SmichaelSmolley/Diplom_Arbeit/Dokumentation/Oficell/michael.watzek@el.htl-hl.ac.at_2026-09-18_11-34-14-229.pdf

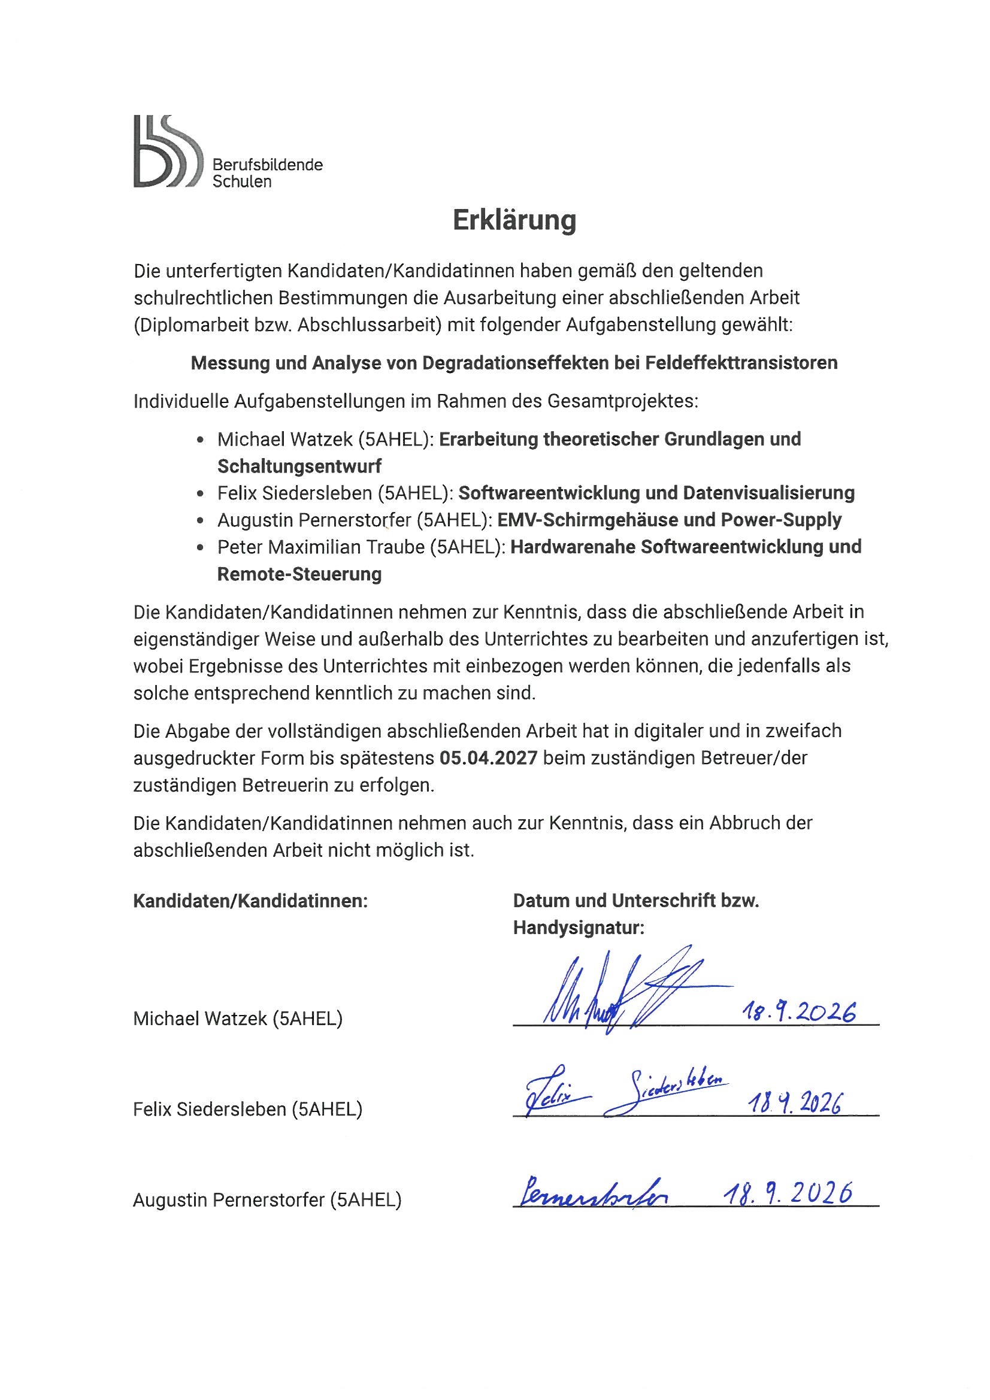
[picture p40: page 1]
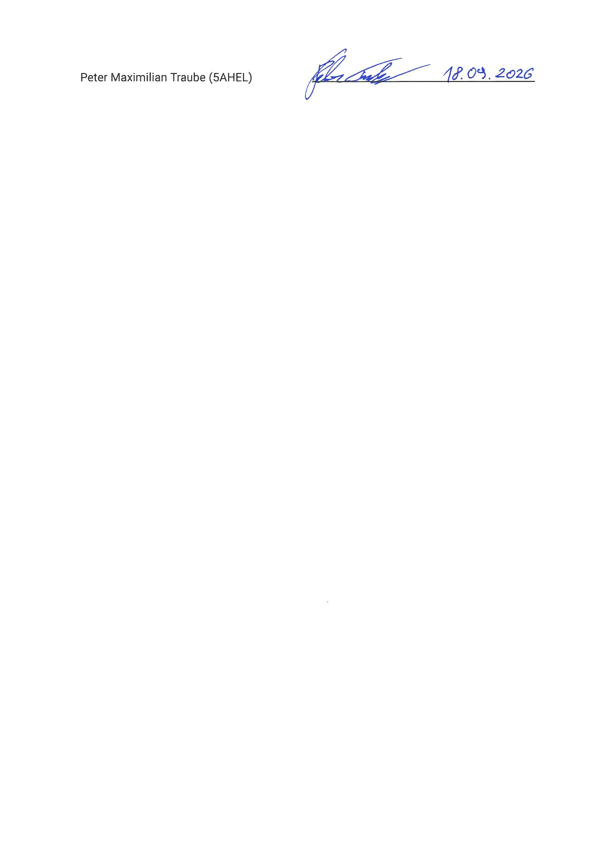
[picture p41: page 2]
