SmichaelSmolley/Diplom_Arbeit/Dokumentation/Datashit/PinkNoise-1durchf.pdf

Quelle:
https://www.analog.com/en/resources/analog-dialogue/articles/understanding-andeliminating-1-fnoise.html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,effectively%2 0reduced%20by%20this%20technique. (https://www.analog.com/en/resources/analog-dialogue/articles/understanding-and-eliminating-1-f-noise.html)

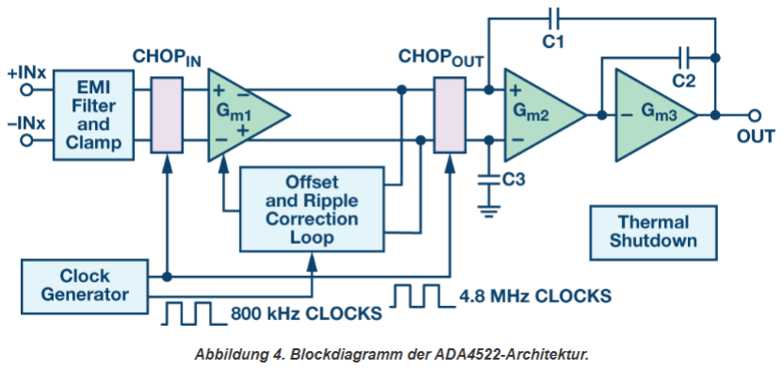
[picture p42: figure]

Möglicher Chopper:
https://www.ti.com/product/de-de/LMP7721
