SmichaelSmolley/Diplom_Arbeit/Dokumentation/Device#01_idvg_05_10.jpg

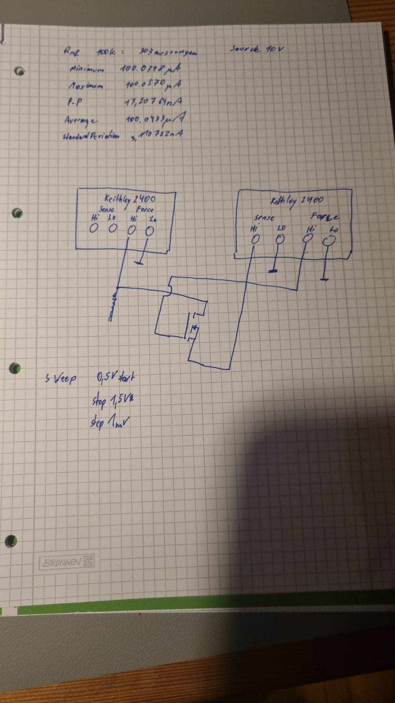
Dokumentation/Device#01_idvg_05_10.jpg
