SmichaelSmolley/Diplom_Arbeit/Dokumentation/dokumentation_bilder/FFTGraph_OV24_Simple.png

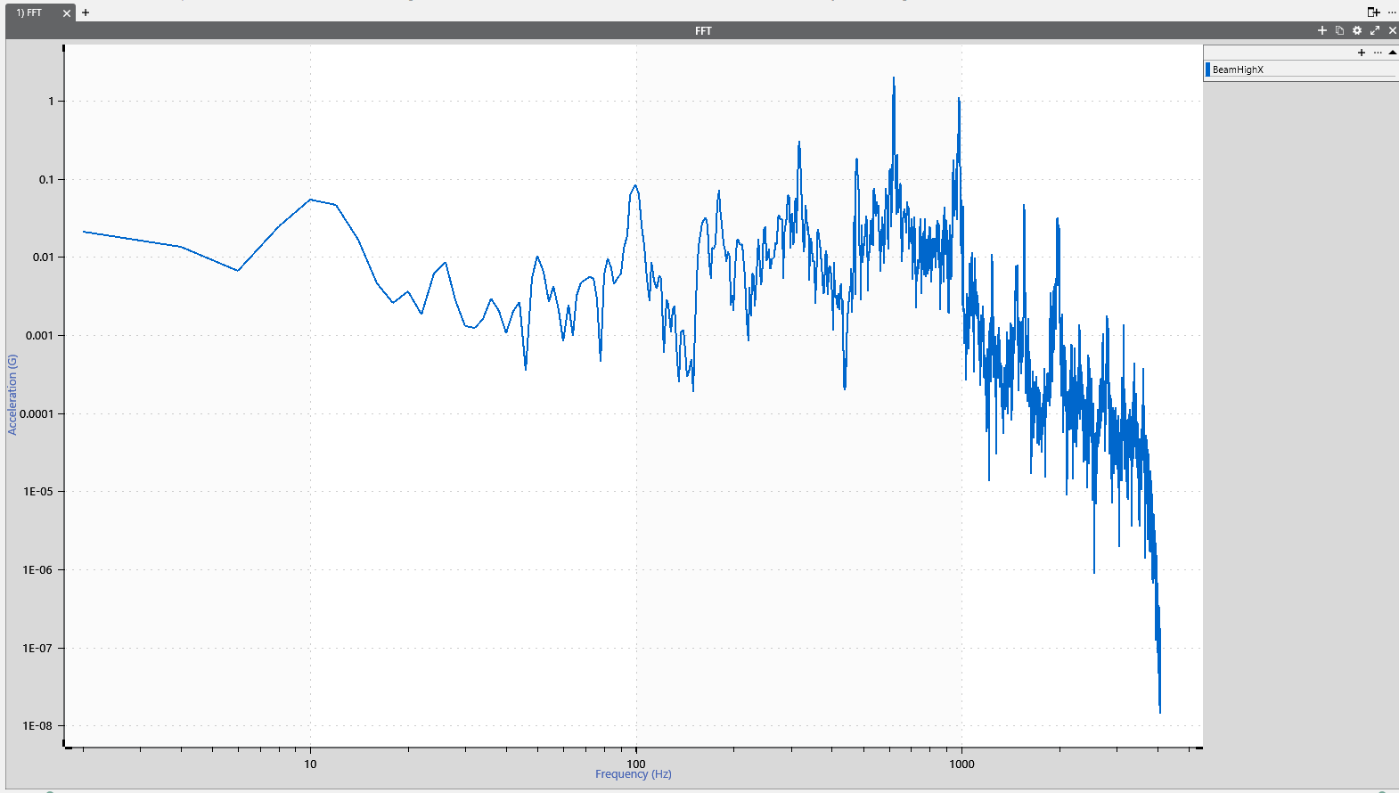
Dokumentation/dokumentation_bilder/FFTGraph_OV24_Simple.png
