SmichaelSmolley/Diplom_Arbeit/Dokumentation/dokumentation_bilder/Screenshot 2026-03-04 135011.png

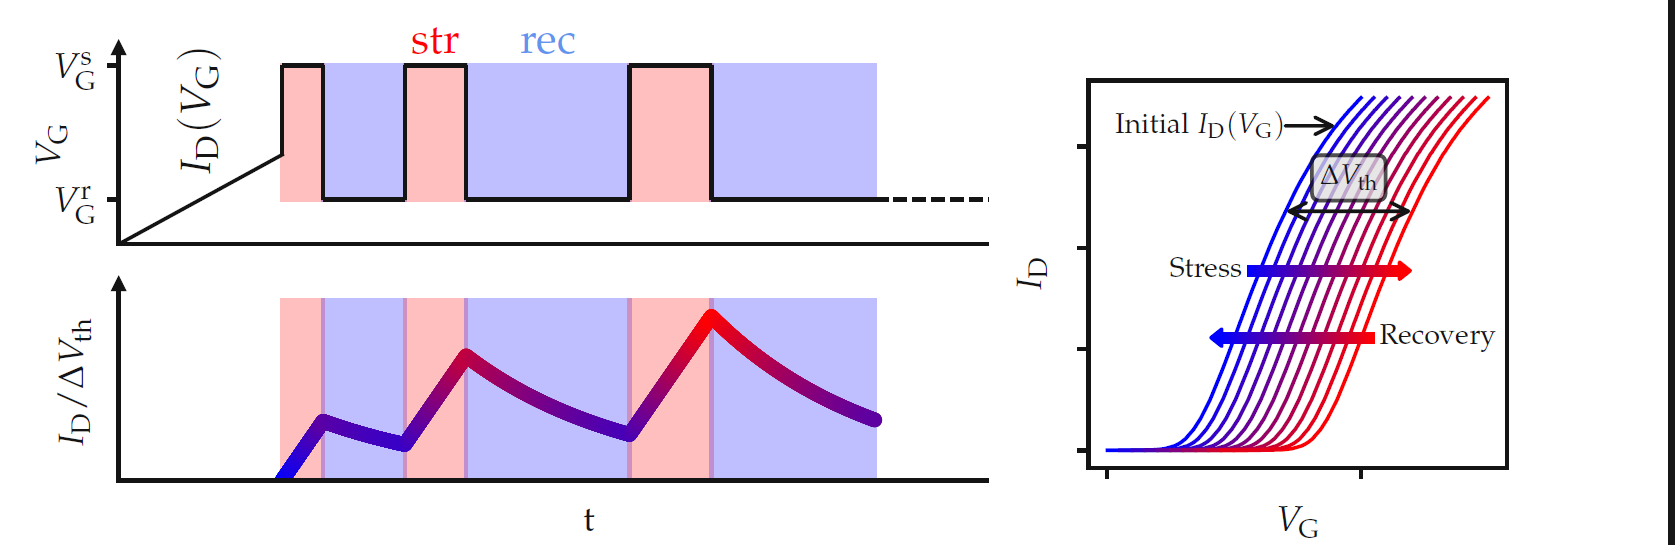
Dokumentation/dokumentation_bilder/Screenshot 2026-03-04 135011.png
