SmichaelSmolley/Diplom_Arbeit/Dokumentation/dokumentation_bilder/signal-2026-05-28-094256_002.jpeg

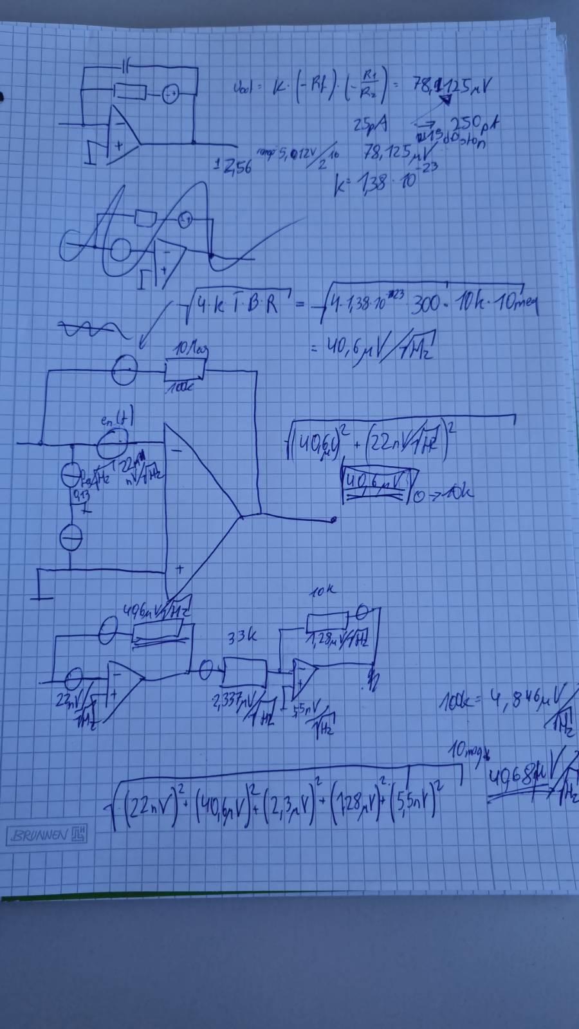
Dokumentation/dokumentation_bilder/signal-2026-05-28-094256_002.jpeg
