SmichaelSmolley/Diplom_Arbeit/Dokumentation/IDVG_BS170_log_17_03_2026.png

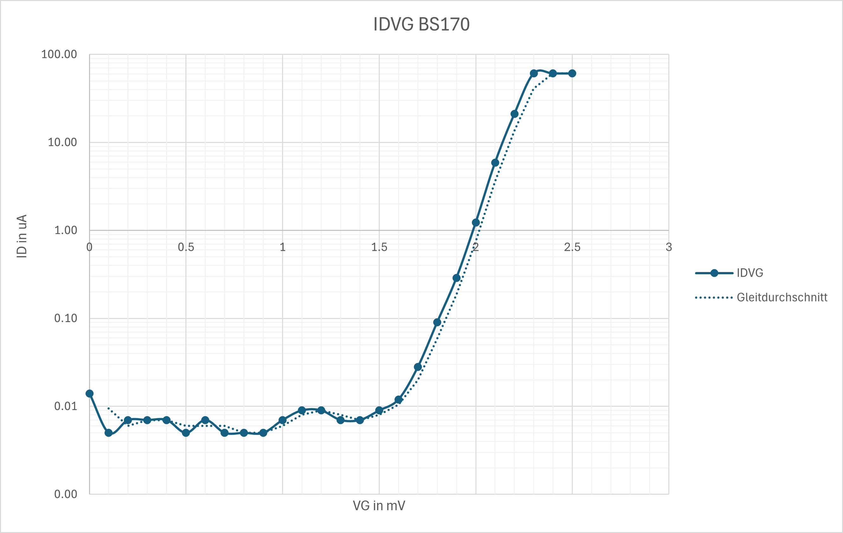
Dokumentation/IDVG_BS170_log_17_03_2026.png
