SmichaelSmolley/Diplom_Arbeit/Software/firmware/Unterlagen_ELLFI/1 Klasse EL/Verbindungsplatine_3D_Top.JPG

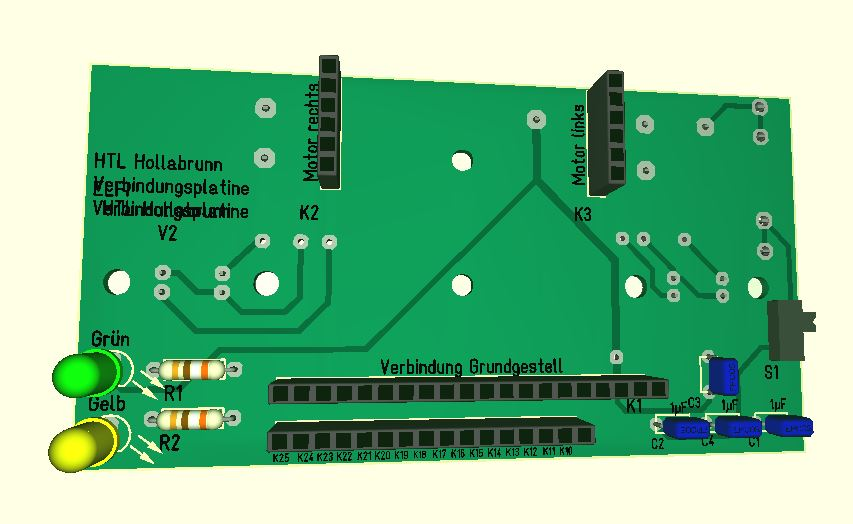
Software/firmware/Unterlagen_ELLFI/1 Klasse EL/Verbindungsplatine_3D_Top.JPG
