SmichaelSmolley/Diplom_Arbeit/Software/firmware/Unterlagen_ELLFI/2 Klasse EL/4erSensorplatine_3D_Top.JPG

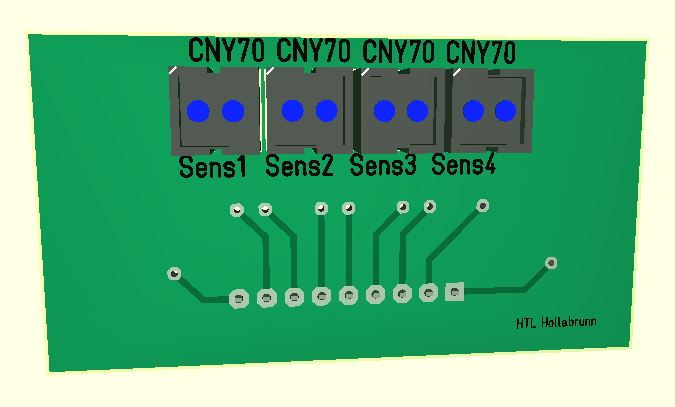
Software/firmware/Unterlagen_ELLFI/2 Klasse EL/4erSensorplatine_3D_Top.JPG
