SmichaelSmolley/Diplom_Arbeit/Software/firmware/Unterlagen_ELLFI/2 Klasse EL/Hauptplatine_3D.JPG

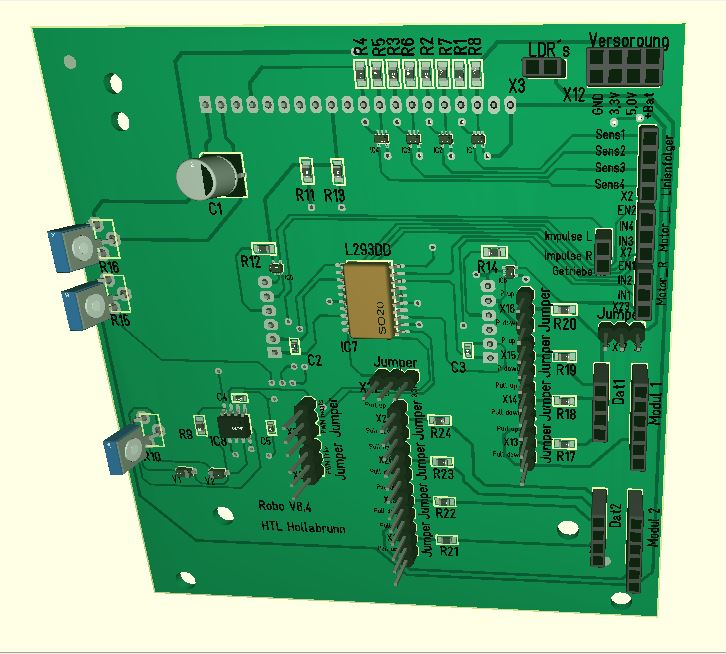
Software/firmware/Unterlagen_ELLFI/2 Klasse EL/Hauptplatine_3D.JPG
