SmichaelSmolley/Diplom_Arbeit/Dokumentation/Rechnungen/99712510.xlsx

# | MENGE | TEILENUMMER | HERSTELLER-TEILENUMMER | BESCHREIBUNG | KUNDENREFERENZ | LIEFERRÜCKSTÄNDE | STÜCKPREIS | GESAMTPREIS
1 | 2 | Z5234-ND | G6SK-2 DC3 | RELAY TELECOM DPDT 2A 3V |  | 0 | 4.04 | 8.08
2 | 2 | Z3287-ND | G6SK-2F DC3 | RELAY TELECOM DPDT 2A 3V |  | 2 | 4.67 | 9.34
3 | 1 | Y0062-100KA-ND | Y0062100K000T9L | RES 100K OHM 0.6W 0.01% RADIAL |  | 0 | 34.06 | 34.06
