SmichaelSmolley/Diplom_Arbeit/Hardware/Altium_libs/ul_OPA197IDBVR/Altium/OPA197IDBVR/DBV5_TEX.step

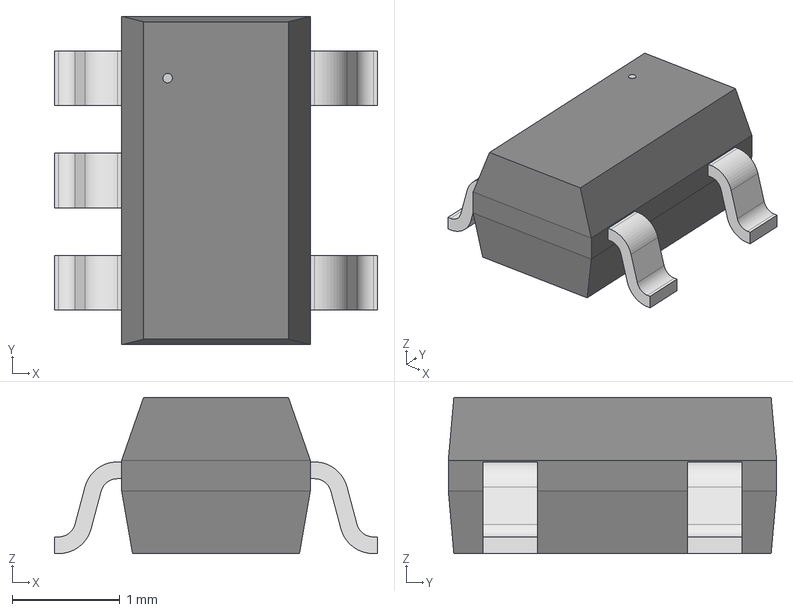
[picture p78: CAD file, 2026-04-23]
Hardware/Altium_libs/ul_OPA197IDBVR/Altium/OPA197IDBVR/DBV5_TEX.step
3.00 x 3.05 x 1.45 mm
