SmichaelSmolley/Diplom_Arbeit/Hardware/Altium_libs/ul_TLV76733DGNR/Altium/TLV76733DGNR/VSSOP8_DGN_TEX.step

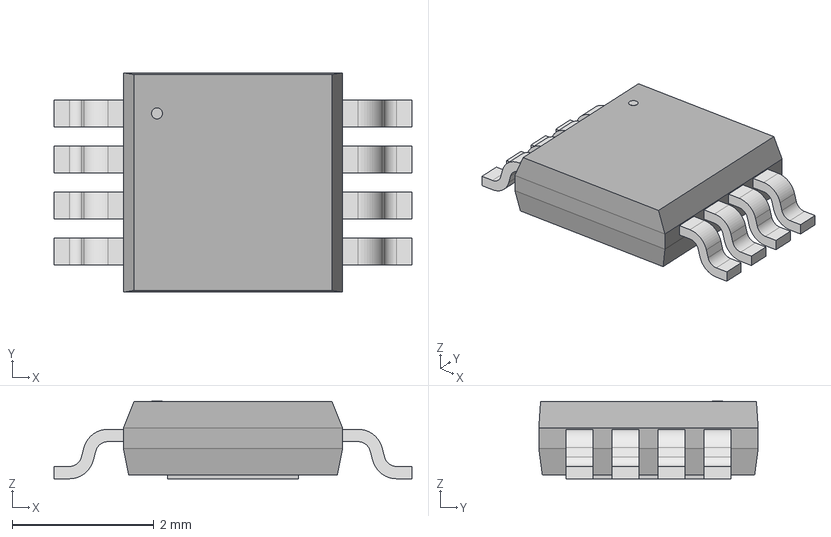
[picture p79: CAD file, 2026-05-05]
Hardware/Altium_libs/ul_TLV76733DGNR/Altium/TLV76733DGNR/VSSOP8_DGN_TEX.step
5.05 x 3.10 x 1.09 mm
