SmichaelSmolley/Diplom_Arbeit/Hardware/Altium_libs/ul_Y0062100K000T9L/Altium/RES_S102K_7P62X2P67_VIS.step

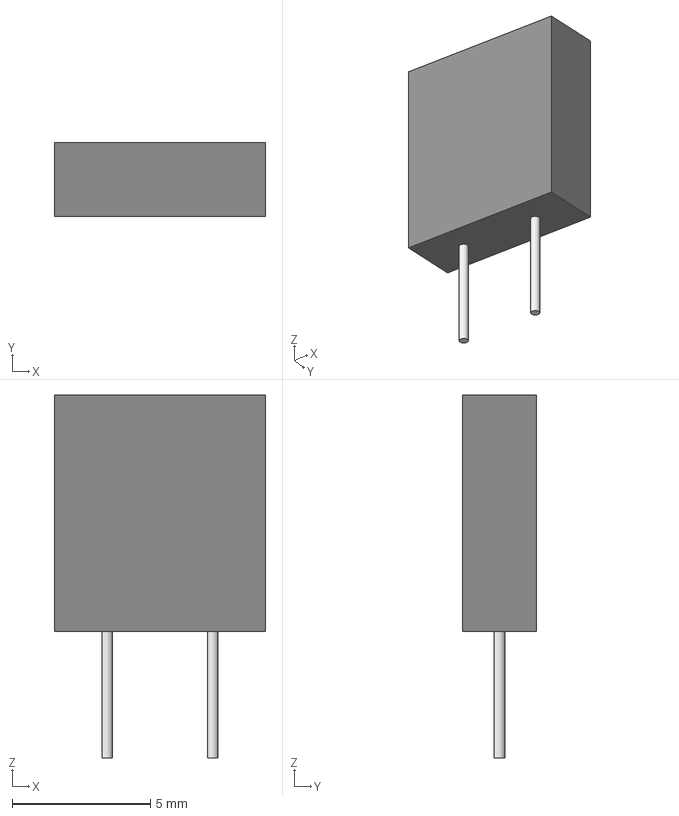
[picture p80: CAD file, 2026-05-07]
Hardware/Altium_libs/ul_Y0062100K000T9L/Altium/RES_S102K_7P62X2P67_VIS.step
7.62 x 2.67 x 13.1 mm
