SmichaelSmolley/Diplom_Arbeit/Software/firmware/PCB_test_code_peda/Objects/PCB_test.htm

# Static Call Graph for image .\Objects\PCB_test.axf

#<CALLGRAPH># ARM Linker, 6190004: Last Updated: Wed Sep 16 19:25:18 2026

### Maximum Stack Usage = 132 bytes + Unknown(Functions without stacksize, Cycles, Untraceable Function Pointers)

### Call chain for Maximum Stack Depth:

__rt_entry_main ⇒ main ⇒ scpi_set_source_voltage ⇒ uart1_put_float ⇒ uart1_put_int ⇒ uart_put_char

### Functions with no stack information

- __user_initial_stackheap

### Mutually Recursive functions

- NMI_Handler ⇒ NMI_Handler
- HardFault_Handler ⇒ HardFault_Handler
- MemManage_Handler ⇒ MemManage_Handler
- BusFault_Handler ⇒ BusFault_Handler
- UsageFault_Handler ⇒ UsageFault_Handler
- SVC_Handler ⇒ SVC_Handler
- DebugMon_Handler ⇒ DebugMon_Handler
- PendSV_Handler ⇒ PendSV_Handler
- SysTick_Handler ⇒ SysTick_Handler
- ADC1_2_IRQHandler ⇒ ADC1_2_IRQHandler

### Function Pointers

- ADC1_2_IRQHandler from startup_stm32f10x_md.o(.text) referenced from startup_stm32f10x_md.o(RESET)
- BusFault_Handler from startup_stm32f10x_md.o(.text) referenced from startup_stm32f10x_md.o(RESET)
- CAN1_RX1_IRQHandler from startup_stm32f10x_md.o(.text) referenced from startup_stm32f10x_md.o(RESET)
- CAN1_SCE_IRQHandler from startup_stm32f10x_md.o(.text) referenced from startup_stm32f10x_md.o(RESET)
- DMA1_Channel1_IRQHandler from startup_stm32f10x_md.o(.text) referenced from startup_stm32f10x_md.o(RESET)
- DMA1_Channel2_IRQHandler from startup_stm32f10x_md.o(.text) referenced from startup_stm32f10x_md.o(RESET)
- DMA1_Channel3_IRQHandler from startup_stm32f10x_md.o(.text) referenced from startup_stm32f10x_md.o(RESET)
- DMA1_Channel4_IRQHandler from startup_stm32f10x_md.o(.text) referenced from startup_stm32f10x_md.o(RESET)
- DMA1_Channel5_IRQHandler from startup_stm32f10x_md.o(.text) referenced from startup_stm32f10x_md.o(RESET)
- DMA1_Channel6_IRQHandler from startup_stm32f10x_md.o(.text) referenced from startup_stm32f10x_md.o(RESET)
- DMA1_Channel7_IRQHandler from startup_stm32f10x_md.o(.text) referenced from startup_stm32f10x_md.o(RESET)
- DebugMon_Handler from startup_stm32f10x_md.o(.text) referenced from startup_stm32f10x_md.o(RESET)
- EXTI0_IRQHandler from startup_stm32f10x_md.o(.text) referenced from startup_stm32f10x_md.o(RESET)
- EXTI15_10_IRQHandler from startup_stm32f10x_md.o(.text) referenced from startup_stm32f10x_md.o(RESET)
- EXTI1_IRQHandler from startup_stm32f10x_md.o(.text) referenced from startup_stm32f10x_md.o(RESET)
- EXTI2_IRQHandler from startup_stm32f10x_md.o(.text) referenced from startup_stm32f10x_md.o(RESET)
- EXTI3_IRQHandler from startup_stm32f10x_md.o(.text) referenced from startup_stm32f10x_md.o(RESET)
- EXTI4_IRQHandler from startup_stm32f10x_md.o(.text) referenced from startup_stm32f10x_md.o(RESET)
- EXTI9_5_IRQHandler from startup_stm32f10x_md.o(.text) referenced from startup_stm32f10x_md.o(RESET)
- FLASH_IRQHandler from startup_stm32f10x_md.o(.text) referenced from startup_stm32f10x_md.o(RESET)
- HardFault_Handler from startup_stm32f10x_md.o(.text) referenced from startup_stm32f10x_md.o(RESET)
- I2C1_ER_IRQHandler from startup_stm32f10x_md.o(.text) referenced from startup_stm32f10x_md.o(RESET)
- I2C1_EV_IRQHandler from startup_stm32f10x_md.o(.text) referenced from startup_stm32f10x_md.o(RESET)
- I2C2_ER_IRQHandler from startup_stm32f10x_md.o(.text) referenced from startup_stm32f10x_md.o(RESET)
- I2C2_EV_IRQHandler from startup_stm32f10x_md.o(.text) referenced from startup_stm32f10x_md.o(RESET)
- MemManage_Handler from startup_stm32f10x_md.o(.text) referenced from startup_stm32f10x_md.o(RESET)
- NMI_Handler from startup_stm32f10x_md.o(.text) referenced from startup_stm32f10x_md.o(RESET)
- PVD_IRQHandler from startup_stm32f10x_md.o(.text) referenced from startup_stm32f10x_md.o(RESET)
- PendSV_Handler from startup_stm32f10x_md.o(.text) referenced from startup_stm32f10x_md.o(RESET)
- RCC_IRQHandler from startup_stm32f10x_md.o(.text) referenced from startup_stm32f10x_md.o(RESET)
- RTCAlarm_IRQHandler from startup_stm32f10x_md.o(.text) referenced from startup_stm32f10x_md.o(RESET)
- RTC_IRQHandler from startup_stm32f10x_md.o(.text) referenced from startup_stm32f10x_md.o(RESET)
- Reset_Handler from startup_stm32f10x_md.o(.text) referenced from startup_stm32f10x_md.o(RESET)
- SPI1_IRQHandler from startup_stm32f10x_md.o(.text) referenced from startup_stm32f10x_md.o(RESET)
- SPI2_IRQHandler from startup_stm32f10x_md.o(.text) referenced from startup_stm32f10x_md.o(RESET)
- SVC_Handler from startup_stm32f10x_md.o(.text) referenced from startup_stm32f10x_md.o(RESET)
- SysTick_Handler from startup_stm32f10x_md.o(.text) referenced from startup_stm32f10x_md.o(RESET)
- SystemInit from system_stm32f10x.o(.text.SystemInit) referenced from startup_stm32f10x_md.o(.text)
- TAMPER_IRQHandler from startup_stm32f10x_md.o(.text) referenced from startup_stm32f10x_md.o(RESET)
- TIM1_BRK_IRQHandler from startup_stm32f10x_md.o(.text) referenced from startup_stm32f10x_md.o(RESET)
- TIM1_CC_IRQHandler from startup_stm32f10x_md.o(.text) referenced from startup_stm32f10x_md.o(RESET)
- TIM1_TRG_COM_IRQHandler from startup_stm32f10x_md.o(.text) referenced from startup_stm32f10x_md.o(RESET)
- TIM1_UP_IRQHandler from startup_stm32f10x_md.o(.text) referenced from startup_stm32f10x_md.o(RESET)
- TIM2_IRQHandler from startup_stm32f10x_md.o(.text) referenced from startup_stm32f10x_md.o(RESET)
- TIM3_IRQHandler from startup_stm32f10x_md.o(.text) referenced from startup_stm32f10x_md.o(RESET)
- TIM4_IRQHandler from startup_stm32f10x_md.o(.text) referenced from startup_stm32f10x_md.o(RESET)
- USART1_IRQHandler from startup_stm32f10x_md.o(.text) referenced from startup_stm32f10x_md.o(RESET)
- USART2_IRQHandler from startup_stm32f10x_md.o(.text) referenced from startup_stm32f10x_md.o(RESET)
- USART3_IRQHandler from startup_stm32f10x_md.o(.text) referenced from startup_stm32f10x_md.o(RESET)
- USBWakeUp_IRQHandler from startup_stm32f10x_md.o(.text) referenced from startup_stm32f10x_md.o(RESET)
- USB_HP_CAN1_TX_IRQHandler from startup_stm32f10x_md.o(.text) referenced from startup_stm32f10x_md.o(RESET)
- USB_LP_CAN1_RX0_IRQHandler from startup_stm32f10x_md.o(.text) referenced from startup_stm32f10x_md.o(RESET)
- UsageFault_Handler from startup_stm32f10x_md.o(.text) referenced from startup_stm32f10x_md.o(RESET)
- WWDG_IRQHandler from startup_stm32f10x_md.o(.text) referenced from startup_stm32f10x_md.o(RESET)
- __main from __main.o(!!!main) referenced from startup_stm32f10x_md.o(.text)

### Global Symbols

__main (Thumb, 8 bytes, Stack size 0 bytes, __main.o(!!!main))

[Calls]

- >> __scatterload
- >> __rt_entry

[Address Reference Count : 1]

- startup_stm32f10x_md.o(.text)

__scatterload (Thumb, 0 bytes, Stack size unknown bytes, __scatter.o(!!!scatter))

[Called By]

- >> __main

__scatterload_rt2 (Thumb, 44 bytes, Stack size unknown bytes, __scatter.o(!!!scatter), UNUSED)

[Calls]

- >> __rt_entry

__scatterload_rt2_thumb_only (Thumb, 0 bytes, Stack size unknown bytes, __scatter.o(!!!scatter), UNUSED)

__scatterload_null (Thumb, 0 bytes, Stack size unknown bytes, __scatter.o(!!!scatter), UNUSED)

__scatterload_zeroinit (Thumb, 28 bytes, Stack size unknown bytes, __scatter_zi.o(!!handler_zi), UNUSED)

__rt_lib_init (Thumb, 0 bytes, Stack size unknown bytes, libinit.o(.ARM.Collect$$libinit$$00000000))

[Called By]

- >> __rt_entry_li

__rt_lib_init_alloca_1 (Thumb, 0 bytes, Stack size unknown bytes, libinit2.o(.ARM.Collect$$libinit$$00000030))

__rt_lib_init_argv_1 (Thumb, 0 bytes, Stack size unknown bytes, libinit2.o(.ARM.Collect$$libinit$$0000002E))

__rt_lib_init_atexit_1 (Thumb, 0 bytes, Stack size unknown bytes, libinit2.o(.ARM.Collect$$libinit$$0000001D))

__rt_lib_init_clock_1 (Thumb, 0 bytes, Stack size unknown bytes, libinit2.o(.ARM.Collect$$libinit$$00000023))

__rt_lib_init_cpp_1 (Thumb, 0 bytes, Stack size unknown bytes, libinit2.o(.ARM.Collect$$libinit$$00000034))

__rt_lib_init_exceptions_1 (Thumb, 0 bytes, Stack size unknown bytes, libinit2.o(.ARM.Collect$$libinit$$00000032))

__rt_lib_init_fp_1 (Thumb, 0 bytes, Stack size unknown bytes, libinit2.o(.ARM.Collect$$libinit$$00000002))

__rt_lib_init_fp_trap_1 (Thumb, 0 bytes, Stack size unknown bytes, libinit2.o(.ARM.Collect$$libinit$$00000021))

__rt_lib_init_getenv_1 (Thumb, 0 bytes, Stack size unknown bytes, libinit2.o(.ARM.Collect$$libinit$$00000025))

__rt_lib_init_heap_1 (Thumb, 0 bytes, Stack size unknown bytes, libinit2.o(.ARM.Collect$$libinit$$0000000C))

__rt_lib_init_lc_collate_1 (Thumb, 0 bytes, Stack size unknown bytes, libinit2.o(.ARM.Collect$$libinit$$00000013))

__rt_lib_init_lc_ctype_1 (Thumb, 0 bytes, Stack size unknown bytes, libinit2.o(.ARM.Collect$$libinit$$00000015))

__rt_lib_init_lc_monetary_1 (Thumb, 0 bytes, Stack size unknown bytes, libinit2.o(.ARM.Collect$$libinit$$00000017))

__rt_lib_init_lc_numeric_1 (Thumb, 0 bytes, Stack size unknown bytes, libinit2.o(.ARM.Collect$$libinit$$00000019))

__rt_lib_init_lc_time_1 (Thumb, 0 bytes, Stack size unknown bytes, libinit2.o(.ARM.Collect$$libinit$$0000001B))

__rt_lib_init_preinit_1 (Thumb, 0 bytes, Stack size unknown bytes, libinit2.o(.ARM.Collect$$libinit$$00000006))

__rt_lib_init_rand_1 (Thumb, 0 bytes, Stack size unknown bytes, libinit2.o(.ARM.Collect$$libinit$$00000010))

__rt_lib_init_relocate_pie_1 (Thumb, 0 bytes, Stack size unknown bytes, libinit2.o(.ARM.Collect$$libinit$$00000004))

__rt_lib_init_return (Thumb, 0 bytes, Stack size unknown bytes, libinit2.o(.ARM.Collect$$libinit$$00000035))

__rt_lib_init_signal_1 (Thumb, 0 bytes, Stack size unknown bytes, libinit2.o(.ARM.Collect$$libinit$$0000001F))

__rt_lib_init_stdio_1 (Thumb, 0 bytes, Stack size unknown bytes, libinit2.o(.ARM.Collect$$libinit$$00000027))

__rt_lib_init_user_alloc_1 (Thumb, 0 bytes, Stack size unknown bytes, libinit2.o(.ARM.Collect$$libinit$$0000000E))

__rt_lib_shutdown (Thumb, 0 bytes, Stack size unknown bytes, libshutdown.o(.ARM.Collect$$libshutdown$$00000000))

[Called By]

- >> __rt_exit_ls

__rt_lib_shutdown_cpp_1 (Thumb, 0 bytes, Stack size unknown bytes, libshutdown2.o(.ARM.Collect$$libshutdown$$00000002))

__rt_lib_shutdown_fp_trap_1 (Thumb, 0 bytes, Stack size unknown bytes, libshutdown2.o(.ARM.Collect$$libshutdown$$00000007))

__rt_lib_shutdown_heap_1 (Thumb, 0 bytes, Stack size unknown bytes, libshutdown2.o(.ARM.Collect$$libshutdown$$0000000F))

__rt_lib_shutdown_return (Thumb, 0 bytes, Stack size unknown bytes, libshutdown2.o(.ARM.Collect$$libshutdown$$00000010))

__rt_lib_shutdown_signal_1 (Thumb, 0 bytes, Stack size unknown bytes, libshutdown2.o(.ARM.Collect$$libshutdown$$0000000A))

__rt_lib_shutdown_stdio_1 (Thumb, 0 bytes, Stack size unknown bytes, libshutdown2.o(.ARM.Collect$$libshutdown$$00000004))

__rt_lib_shutdown_user_alloc_1 (Thumb, 0 bytes, Stack size unknown bytes, libshutdown2.o(.ARM.Collect$$libshutdown$$0000000C))

__rt_entry (Thumb, 0 bytes, Stack size unknown bytes, __rtentry.o(.ARM.Collect$$rtentry$$00000000))

[Called By]

- >> __scatterload_rt2
- >> __main

__rt_entry_presh_1 (Thumb, 0 bytes, Stack size unknown bytes, __rtentry2.o(.ARM.Collect$$rtentry$$00000002))

__rt_entry_sh (Thumb, 0 bytes, Stack size unknown bytes, __rtentry4.o(.ARM.Collect$$rtentry$$00000004))

[Stack]

- Max Depth = 8 + Unknown Stack Size
- Call Chain = __rt_entry_sh ⇒ __user_setup_stackheap

[Calls]

- >> __user_setup_stackheap

__rt_entry_li (Thumb, 0 bytes, Stack size unknown bytes, __rtentry2.o(.ARM.Collect$$rtentry$$0000000A))

[Calls]

- >> __rt_lib_init

__rt_entry_postsh_1 (Thumb, 0 bytes, Stack size unknown bytes, __rtentry2.o(.ARM.Collect$$rtentry$$00000009))

__rt_entry_main (Thumb, 0 bytes, Stack size unknown bytes, __rtentry2.o(.ARM.Collect$$rtentry$$0000000D))

[Stack]

- Max Depth = 132 + Unknown Stack Size
- Call Chain = __rt_entry_main ⇒ main ⇒ scpi_set_source_voltage ⇒ uart1_put_float ⇒ uart1_put_int ⇒ uart_put_char

[Calls]

- >> exit
- >> main

__rt_entry_postli_1 (Thumb, 0 bytes, Stack size unknown bytes, __rtentry2.o(.ARM.Collect$$rtentry$$0000000C))

__rt_exit (Thumb, 0 bytes, Stack size unknown bytes, rtexit.o(.ARM.Collect$$rtexit$$00000000))

[Called By]

- >> exit

__rt_exit_ls (Thumb, 0 bytes, Stack size unknown bytes, rtexit2.o(.ARM.Collect$$rtexit$$00000003))

[Calls]

- >> __rt_lib_shutdown

__rt_exit_prels_1 (Thumb, 0 bytes, Stack size unknown bytes, rtexit2.o(.ARM.Collect$$rtexit$$00000002))

__rt_exit_exit (Thumb, 0 bytes, Stack size unknown bytes, rtexit2.o(.ARM.Collect$$rtexit$$00000004))

[Calls]

- >> _sys_exit

Reset_Handler (Thumb, 8 bytes, Stack size 0 bytes, startup_stm32f10x_md.o(.text))
[Address Reference Count : 1]

- startup_stm32f10x_md.o(RESET)

NMI_Handler (Thumb, 2 bytes, Stack size 0 bytes, startup_stm32f10x_md.o(.text))

[Calls]

- >> NMI_Handler

[Called By]

- >> NMI_Handler

[Address Reference Count : 1]

- startup_stm32f10x_md.o(RESET)

HardFault_Handler (Thumb, 2 bytes, Stack size 0 bytes, startup_stm32f10x_md.o(.text))

[Calls]

- >> HardFault_Handler

[Called By]

- >> HardFault_Handler

[Address Reference Count : 1]

- startup_stm32f10x_md.o(RESET)

MemManage_Handler (Thumb, 2 bytes, Stack size 0 bytes, startup_stm32f10x_md.o(.text))

[Calls]

- >> MemManage_Handler

[Called By]

- >> MemManage_Handler

[Address Reference Count : 1]

- startup_stm32f10x_md.o(RESET)

BusFault_Handler (Thumb, 2 bytes, Stack size 0 bytes, startup_stm32f10x_md.o(.text))

[Calls]

- >> BusFault_Handler

[Called By]

- >> BusFault_Handler

[Address Reference Count : 1]

- startup_stm32f10x_md.o(RESET)

UsageFault_Handler (Thumb, 2 bytes, Stack size 0 bytes, startup_stm32f10x_md.o(.text))

[Calls]

- >> UsageFault_Handler

[Called By]

- >> UsageFault_Handler

[Address Reference Count : 1]

- startup_stm32f10x_md.o(RESET)

SVC_Handler (Thumb, 2 bytes, Stack size 0 bytes, startup_stm32f10x_md.o(.text))

[Calls]

- >> SVC_Handler

[Called By]

- >> SVC_Handler

[Address Reference Count : 1]

- startup_stm32f10x_md.o(RESET)

DebugMon_Handler (Thumb, 2 bytes, Stack size 0 bytes, startup_stm32f10x_md.o(.text))

[Calls]

- >> DebugMon_Handler

[Called By]

- >> DebugMon_Handler

[Address Reference Count : 1]

- startup_stm32f10x_md.o(RESET)

PendSV_Handler (Thumb, 2 bytes, Stack size 0 bytes, startup_stm32f10x_md.o(.text))

[Calls]

- >> PendSV_Handler

[Called By]

- >> PendSV_Handler

[Address Reference Count : 1]

- startup_stm32f10x_md.o(RESET)

SysTick_Handler (Thumb, 2 bytes, Stack size 0 bytes, startup_stm32f10x_md.o(.text))

[Calls]

- >> SysTick_Handler

[Called By]

- >> SysTick_Handler

[Address Reference Count : 1]

- startup_stm32f10x_md.o(RESET)

ADC1_2_IRQHandler (Thumb, 0 bytes, Stack size 0 bytes, startup_stm32f10x_md.o(.text))

[Calls]

- >> ADC1_2_IRQHandler

[Called By]

- >> ADC1_2_IRQHandler

[Address Reference Count : 1]

- startup_stm32f10x_md.o(RESET)

CAN1_RX1_IRQHandler (Thumb, 0 bytes, Stack size 0 bytes, startup_stm32f10x_md.o(.text))
[Address Reference Count : 1]

- startup_stm32f10x_md.o(RESET)

CAN1_SCE_IRQHandler (Thumb, 0 bytes, Stack size 0 bytes, startup_stm32f10x_md.o(.text))
[Address Reference Count : 1]

- startup_stm32f10x_md.o(RESET)

DMA1_Channel1_IRQHandler (Thumb, 0 bytes, Stack size 0 bytes, startup_stm32f10x_md.o(.text))
[Address Reference Count : 1]

- startup_stm32f10x_md.o(RESET)

DMA1_Channel2_IRQHandler (Thumb, 0 bytes, Stack size 0 bytes, startup_stm32f10x_md.o(.text))
[Address Reference Count : 1]

- startup_stm32f10x_md.o(RESET)

DMA1_Channel3_IRQHandler (Thumb, 0 bytes, Stack size 0 bytes, startup_stm32f10x_md.o(.text))
[Address Reference Count : 1]

- startup_stm32f10x_md.o(RESET)

DMA1_Channel4_IRQHandler (Thumb, 0 bytes, Stack size 0 bytes, startup_stm32f10x_md.o(.text))
[Address Reference Count : 1]

- startup_stm32f10x_md.o(RESET)

DMA1_Channel5_IRQHandler (Thumb, 0 bytes, Stack size 0 bytes, startup_stm32f10x_md.o(.text))
[Address Reference Count : 1]

- startup_stm32f10x_md.o(RESET)

DMA1_Channel6_IRQHandler (Thumb, 0 bytes, Stack size 0 bytes, startup_stm32f10x_md.o(.text))
[Address Reference Count : 1]

- startup_stm32f10x_md.o(RESET)

DMA1_Channel7_IRQHandler (Thumb, 0 bytes, Stack size 0 bytes, startup_stm32f10x_md.o(.text))
[Address Reference Count : 1]

- startup_stm32f10x_md.o(RESET)

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
[Address Reference Count : 1]

- startup_stm32f10x_md.o(RESET)

USBWakeUp_IRQHandler (Thumb, 0 bytes, Stack size 0 bytes, startup_stm32f10x_md.o(.text))
[Address Reference Count : 1]

- startup_stm32f10x_md.o(RESET)

USB_HP_CAN1_TX_IRQHandler (Thumb, 0 bytes, Stack size 0 bytes, startup_stm32f10x_md.o(.text))
[Address Reference Count : 1]

- startup_stm32f10x_md.o(RESET)

USB_LP_CAN1_RX0_IRQHandler (Thumb, 0 bytes, Stack size 0 bytes, startup_stm32f10x_md.o(.text))
[Address Reference Count : 1]

- startup_stm32f10x_md.o(RESET)

WWDG_IRQHandler (Thumb, 0 bytes, Stack size 0 bytes, startup_stm32f10x_md.o(.text))
[Address Reference Count : 1]

- startup_stm32f10x_md.o(RESET)

__user_initial_stackheap (Thumb, 0 bytes, Stack size unknown bytes, startup_stm32f10x_md.o(.text))

[Called By]

- >> __user_setup_stackheap

__use_two_region_memory (Thumb, 2 bytes, Stack size 0 bytes, heapauxi.o(.text), UNUSED)

__rt_heap_escrow$2region (Thumb, 2 bytes, Stack size 0 bytes, heapauxi.o(.text), UNUSED)

__rt_heap_expand$2region (Thumb, 2 bytes, Stack size 0 bytes, heapauxi.o(.text), UNUSED)

__user_setup_stackheap (Thumb, 74 bytes, Stack size 8 bytes, sys_stackheap_outer.o(.text))

[Stack]

- Max Depth = 8 + Unknown Stack Size
- Call Chain = __user_setup_stackheap

[Calls]

- >> __user_perproc_libspace
- >> __user_initial_stackheap

[Called By]

- >> __rt_entry_sh

exit (Thumb, 18 bytes, Stack size 8 bytes, exit.o(.text))

[Stack]

- Max Depth = 8 + Unknown Stack Size
- Call Chain = exit

[Calls]

- >> __rt_exit

[Called By]

- >> __rt_entry_main

__user_libspace (Thumb, 8 bytes, Stack size 0 bytes, libspace.o(.text), UNUSED)

__user_perproc_libspace (Thumb, 0 bytes, Stack size 0 bytes, libspace.o(.text))

[Called By]

- >> __user_setup_stackheap

__user_perthread_libspace (Thumb, 0 bytes, Stack size 0 bytes, libspace.o(.text), UNUSED)

_sys_exit (Thumb, 8 bytes, Stack size 0 bytes, sys_exit.o(.text))

[Called By]

- >> __rt_exit_exit

__I$use$semihosting (Thumb, 0 bytes, Stack size 0 bytes, use_no_semi.o(.text), UNUSED)

__use_no_semihosting_swi (Thumb, 2 bytes, Stack size 0 bytes, use_no_semi.o(.text), UNUSED)

__semihosting_library_function (Thumb, 0 bytes, Stack size unknown bytes, indicate_semi.o(.text), UNUSED)

PIN_init (Thumb, 276 bytes, Stack size 4 bytes, pins.o(.text.PIN_init))

[Stack]

- Max Depth = 4
- Call Chain = PIN_init

[Called By]

- >> main

SystemInit (Thumb, 102 bytes, Stack size 8 bytes, system_stm32f10x.o(.text.SystemInit))

[Stack]

- Max Depth = 32
- Call Chain = SystemInit ⇒ SetSysClock ⇒ SetSysClockTo48

[Calls]

- >> SetSysClock

[Address Reference Count : 1]

- startup_stm32f10x_md.o(.text)

main (Thumb, 244 bytes, Stack size 40 bytes, main.o(.text.main))

[Stack]

- Max Depth = 132
- Call Chain = main ⇒ scpi_set_source_voltage ⇒ uart1_put_float ⇒ uart1_put_int ⇒ uart_put_char

[Calls]

- >> __aeabi_fcmpgt
- >> __aeabi_fadd
- >> __aeabi_f2d
- >> wait_ms
- >> PIN_init
- >> scpi_stop_measurement
- >> scpi_start_measurement
- >> scpi_set_sense_autorange
- >> scpi_set_sense_range
- >> scpi_set_source_output
- >> scpi_set_source_voltage
- >> scpi_set_source_prot
- >> scpi_set_source_range
- >> scpi_reset
- >> uart_put_string
- >> set_up_uart1

[Called By]

- >> __rt_entry_main

scpi_reset (Thumb, 28 bytes, Stack size 8 bytes, scpi_commands.o(.text.scpi_reset))

[Stack]

- Max Depth = 28
- Call Chain = scpi_reset ⇒ uart_put_string ⇒ uart_put_char

[Calls]

- >> uart_put_string

[Called By]

- >> main

scpi_set_sense_autorange (Thumb, 74 bytes, Stack size 16 bytes, scpi_commands.o(.text.scpi_set_sense_autorange))

[Stack]

- Max Depth = 36
- Call Chain = scpi_set_sense_autorange ⇒ uart_put_string ⇒ uart_put_char

[Calls]

- >> uart_put_string

[Called By]

- >> main

scpi_set_sense_range (Thumb, 40 bytes, Stack size 16 bytes, scpi_commands.o(.text.scpi_set_sense_range))

[Stack]

- Max Depth = 36
- Call Chain = scpi_set_sense_range ⇒ uart_put_string ⇒ uart_put_char

[Calls]

- >> uart_put_string

[Called By]

- >> main

scpi_set_source_output (Thumb, 98 bytes, Stack size 16 bytes, scpi_commands.o(.text.scpi_set_source_output))

[Stack]

- Max Depth = 52
- Call Chain = scpi_set_source_output ⇒ uart1_put_int ⇒ uart_put_char

[Calls]

- >> uart1_put_int
- >> uart_put_string

[Called By]

- >> main

scpi_set_source_prot (Thumb, 66 bytes, Stack size 16 bytes, scpi_commands.o(.text.scpi_set_source_prot))

[Stack]

- Max Depth = 92
- Call Chain = scpi_set_source_prot ⇒ uart1_put_float ⇒ uart1_put_int ⇒ uart_put_char

[Calls]

- >> uart1_put_float
- >> uart1_put_int
- >> uart_put_string

[Called By]

- >> main

scpi_set_source_range (Thumb, 64 bytes, Stack size 16 bytes, scpi_commands.o(.text.scpi_set_source_range))

[Stack]

- Max Depth = 52
- Call Chain = scpi_set_source_range ⇒ uart1_put_int ⇒ uart_put_char

[Calls]

- >> uart1_put_int
- >> uart_put_string

[Called By]

- >> main

scpi_set_source_voltage (Thumb, 66 bytes, Stack size 16 bytes, scpi_commands.o(.text.scpi_set_source_voltage))

[Stack]

- Max Depth = 92
- Call Chain = scpi_set_source_voltage ⇒ uart1_put_float ⇒ uart1_put_int ⇒ uart_put_char

[Calls]

- >> uart1_put_float
- >> uart1_put_int
- >> uart_put_string

[Called By]

- >> main

scpi_start_measurement (Thumb, 28 bytes, Stack size 8 bytes, scpi_commands.o(.text.scpi_start_measurement))

[Stack]

- Max Depth = 28
- Call Chain = scpi_start_measurement ⇒ uart_put_string ⇒ uart_put_char

[Calls]

- >> uart_put_string

[Called By]

- >> main

scpi_stop_measurement (Thumb, 28 bytes, Stack size 8 bytes, scpi_commands.o(.text.scpi_stop_measurement))

[Stack]

- Max Depth = 28
- Call Chain = scpi_stop_measurement ⇒ uart_put_string ⇒ uart_put_char

[Calls]

- >> uart_put_string

[Called By]

- >> main

set_up_uart1 (Thumb, 136 bytes, Stack size 0 bytes, uart.o(.text.set_up_uart1))

[Called By]

- >> main

uart1_put_float (Thumb, 148 bytes, Stack size 40 bytes, scpi_commands.o(.text.uart1_put_float))

[Stack]

- Max Depth = 76
- Call Chain = uart1_put_float ⇒ uart1_put_int ⇒ uart_put_char

[Calls]

- >> __aeabi_fmul
- >> __aeabi_i2f
- >> __aeabi_f2iz
- >> __aeabi_fcmpge
- >> __aeabi_fsub
- >> uart1_put_int
- >> uart_put_char

[Called By]

- >> scpi_set_source_voltage
- >> scpi_set_source_prot

uart1_put_int (Thumb, 144 bytes, Stack size 32 bytes, scpi_commands.o(.text.uart1_put_int))

[Stack]

- Max Depth = 36
- Call Chain = uart1_put_int ⇒ uart_put_char

[Calls]

- >> uart_put_char

[Called By]

- >> scpi_set_source_output
- >> scpi_set_source_voltage
- >> scpi_set_source_prot
- >> scpi_set_source_range
- >> uart1_put_float

uart_put_char (Thumb, 46 bytes, Stack size 4 bytes, uart.o(.text.uart_put_char))

[Stack]

- Max Depth = 4
- Call Chain = uart_put_char

[Called By]

- >> uart1_put_float
- >> uart1_put_int
- >> uart_put_string

uart_put_string (Thumb, 34 bytes, Stack size 16 bytes, uart.o(.text.uart_put_string))

[Stack]

- Max Depth = 20
- Call Chain = uart_put_string ⇒ uart_put_char

[Calls]

- >> uart_put_char

[Called By]

- >> main
- >> scpi_stop_measurement
- >> scpi_start_measurement
- >> scpi_set_sense_autorange
- >> scpi_set_sense_range
- >> scpi_set_source_output
- >> scpi_set_source_voltage
- >> scpi_set_source_prot
- >> scpi_set_source_range
- >> scpi_reset

wait_ms (Thumb, 40 bytes, Stack size 8 bytes, timer.o(.text.wait_ms))

[Stack]

- Max Depth = 8
- Call Chain = wait_ms

[Called By]

- >> main

__fpl_dretinf (Thumb, 12 bytes, Stack size 0 bytes, dretinf.o(x$fpl$dretinf), UNUSED)

[Called By]

- >> _f2d

__aeabi_f2d (Thumb, 0 bytes, Stack size 16 bytes, f2d.o(x$fpl$f2d))

[Stack]

- Max Depth = 16
- Call Chain = __aeabi_f2d

[Called By]

- >> main

_f2d (Thumb, 86 bytes, Stack size 16 bytes, f2d.o(x$fpl$f2d), UNUSED)

[Calls]

- >> __fpl_fnaninf
- >> __fpl_dretinf

__aeabi_fadd (Thumb, 0 bytes, Stack size 16 bytes, faddsub_clz.o(x$fpl$fadd))

[Stack]

- Max Depth = 16
- Call Chain = __aeabi_fadd

[Called By]

- >> main

_fadd (Thumb, 196 bytes, Stack size 16 bytes, faddsub_clz.o(x$fpl$fadd), UNUSED)

[Calls]

- >> __fpl_fretinf
- >> __fpl_fnaninf
- >> _fsub1

__aeabi_fcmpeq (Thumb, 0 bytes, Stack size 8 bytes, fcmp.o(x$fpl$fcmp), UNUSED)

_feq (Thumb, 14 bytes, Stack size 8 bytes, fcmp.o(x$fpl$fcmp), UNUSED)

[Calls]

- >> _fcmpeq

_fneq (Thumb, 14 bytes, Stack size 8 bytes, fcmp.o(x$fpl$fcmp), UNUSED)

[Calls]

- >> _fcmpeq

__aeabi_fcmpgt (Thumb, 0 bytes, Stack size 8 bytes, fcmp.o(x$fpl$fcmp))

[Stack]

- Max Depth = 8
- Call Chain = __aeabi_fcmpgt

[Called By]

- >> main

_fgr (Thumb, 14 bytes, Stack size 8 bytes, fcmp.o(x$fpl$fcmp), UNUSED)

[Calls]

- >> _fcmpge

__aeabi_fcmpge (Thumb, 0 bytes, Stack size 8 bytes, fcmp.o(x$fpl$fcmp))

[Stack]

- Max Depth = 8
- Call Chain = __aeabi_fcmpge

[Called By]

- >> uart1_put_float

_fgeq (Thumb, 14 bytes, Stack size 8 bytes, fcmp.o(x$fpl$fcmp), UNUSED)

[Calls]

- >> _fcmpge

__aeabi_fcmple (Thumb, 0 bytes, Stack size 8 bytes, fcmp.o(x$fpl$fcmp), UNUSED)

_fleq (Thumb, 14 bytes, Stack size 8 bytes, fcmp.o(x$fpl$fcmp), UNUSED)

[Calls]

- >> _fcmple

__aeabi_fcmplt (Thumb, 0 bytes, Stack size 8 bytes, fcmp.o(x$fpl$fcmp), UNUSED)

_fls (Thumb, 14 bytes, Stack size 8 bytes, fcmp.o(x$fpl$fcmp), UNUSED)

[Calls]

- >> _fcmple

__fpl_fcmp_Inf (Thumb, 24 bytes, Stack size 0 bytes, fcmpi.o(x$fpl$fcmpinf), UNUSED)

[Called By]

- >> _fcmple
- >> _fcmpge
- >> _fcmpeq

__aeabi_cfcmpeq (Thumb, 0 bytes, Stack size 16 bytes, feqf.o(x$fpl$feqf), UNUSED)

_fcmpeq (Thumb, 104 bytes, Stack size 16 bytes, feqf.o(x$fpl$feqf), UNUSED)

[Calls]

- >> __fpl_fcmp_Inf
- >> __fpl_fnaninf

[Called By]

- >> _fneq
- >> _feq

__aeabi_f2iz (Thumb, 0 bytes, Stack size 16 bytes, ffix.o(x$fpl$ffix))

[Stack]

- Max Depth = 16
- Call Chain = __aeabi_f2iz

[Called By]

- >> uart1_put_float

_ffix (Thumb, 54 bytes, Stack size 16 bytes, ffix.o(x$fpl$ffix), UNUSED)

[Calls]

- >> __fpl_fnaninf

__aeabi_i2f (Thumb, 0 bytes, Stack size 0 bytes, fflt_clz.o(x$fpl$fflt))

[Called By]

- >> uart1_put_float

_fflt (Thumb, 48 bytes, Stack size 0 bytes, fflt_clz.o(x$fpl$fflt), UNUSED)

_fcmpge (Thumb, 104 bytes, Stack size 16 bytes, fgeqf.o(x$fpl$fgeqf), UNUSED)

[Calls]

- >> __fpl_fcmp_Inf
- >> __fpl_fnaninf

[Called By]

- >> _fgeq
- >> _fgr

__aeabi_cfcmple (Thumb, 0 bytes, Stack size 16 bytes, fleqf.o(x$fpl$fleqf), UNUSED)

_fcmple (Thumb, 104 bytes, Stack size 16 bytes, fleqf.o(x$fpl$fleqf), UNUSED)

[Calls]

- >> __fpl_fcmp_Inf
- >> __fpl_fnaninf

[Called By]

- >> _fls
- >> _fleq

__fpl_fcmple_InfNaN (Thumb, 0 bytes, Stack size unknown bytes, fleqf.o(x$fpl$fleqf), UNUSED)

__aeabi_fmul (Thumb, 0 bytes, Stack size 16 bytes, fmul.o(x$fpl$fmul))

[Stack]

- Max Depth = 16
- Call Chain = __aeabi_fmul

[Called By]

- >> uart1_put_float

_fmul (Thumb, 258 bytes, Stack size 16 bytes, fmul.o(x$fpl$fmul), UNUSED)

[Calls]

- >> __fpl_fretinf
- >> __fpl_fnaninf

__fpl_fnaninf (Thumb, 140 bytes, Stack size 8 bytes, fnaninf.o(x$fpl$fnaninf), UNUSED)

[Called By]

- >> _fcmple
- >> _fcmpge
- >> _fcmpeq
- >> _fmul
- >> _ffix
- >> _fsub
- >> _fadd
- >> _f2d

__fpl_fretinf (Thumb, 10 bytes, Stack size 0 bytes, fretinf.o(x$fpl$fretinf), UNUSED)

[Called By]

- >> _fmul
- >> _fadd

__aeabi_fsub (Thumb, 0 bytes, Stack size 16 bytes, faddsub_clz.o(x$fpl$fsub))

[Stack]

- Max Depth = 16
- Call Chain = __aeabi_fsub

[Called By]

- >> uart1_put_float

_fsub (Thumb, 234 bytes, Stack size 16 bytes, faddsub_clz.o(x$fpl$fsub), UNUSED)

[Calls]

- >> __fpl_fnaninf
- >> _fadd1

### Local Symbols

SetSysClock (Thumb, 8 bytes, Stack size 8 bytes, system_stm32f10x.o(.text.SetSysClock))

[Stack]

- Max Depth = 24
- Call Chain = SetSysClock ⇒ SetSysClockTo48

[Calls]

- >> SetSysClockTo48

[Called By]

- >> SystemInit

SetSysClockTo48 (Thumb, 290 bytes, Stack size 16 bytes, system_stm32f10x.o(.text.SetSysClockTo48))

[Stack]

- Max Depth = 16
- Call Chain = SetSysClockTo48

[Called By]

- >> SetSysClock

_fadd1 (Thumb, 0 bytes, Stack size unknown bytes, faddsub_clz.o(x$fpl$fadd), UNUSED)

[Called By]

- >> _fsub

_fsub1 (Thumb, 0 bytes, Stack size unknown bytes, faddsub_clz.o(x$fpl$fsub), UNUSED)

[Called By]

- >> _fadd

### Undefined Global Symbols
