SmichaelSmolley/Diplom_Arbeit/Hardware/PCB_Project/DIP_V01_Testing/PCB_Project/PCB_Project.pdf

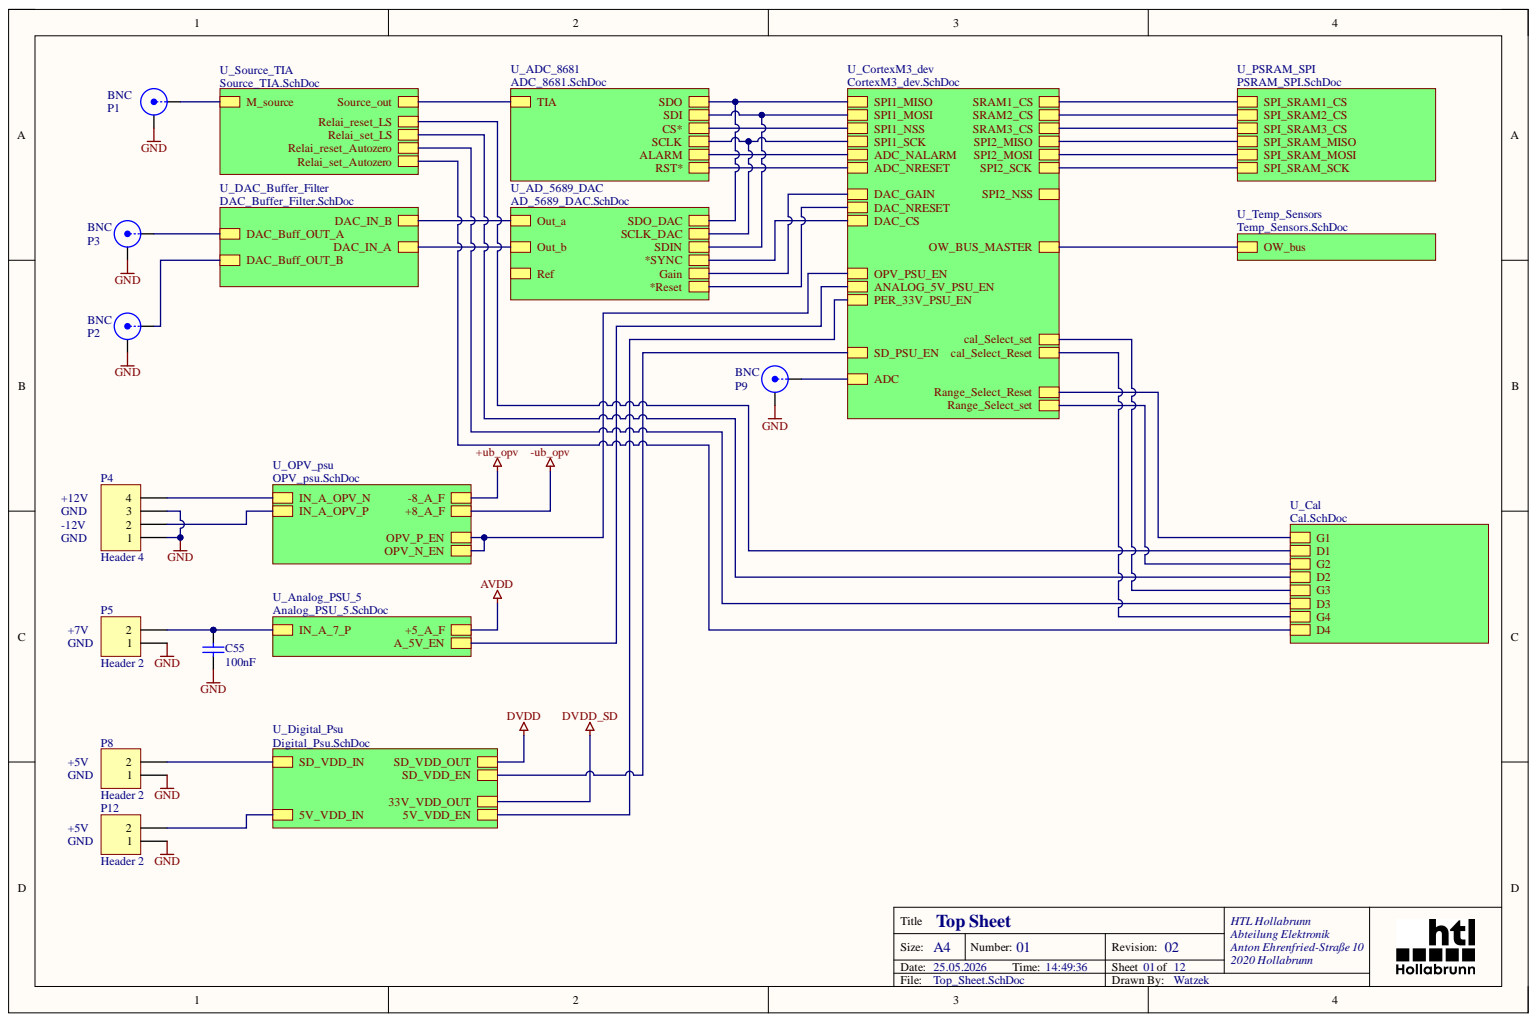
[picture p81: page 1]

A 4 Size : | 0 1 N umb er : | 0 2 Rev i s i o n :
Dat e : 5.0 . T ime : : : | | Shee t o f

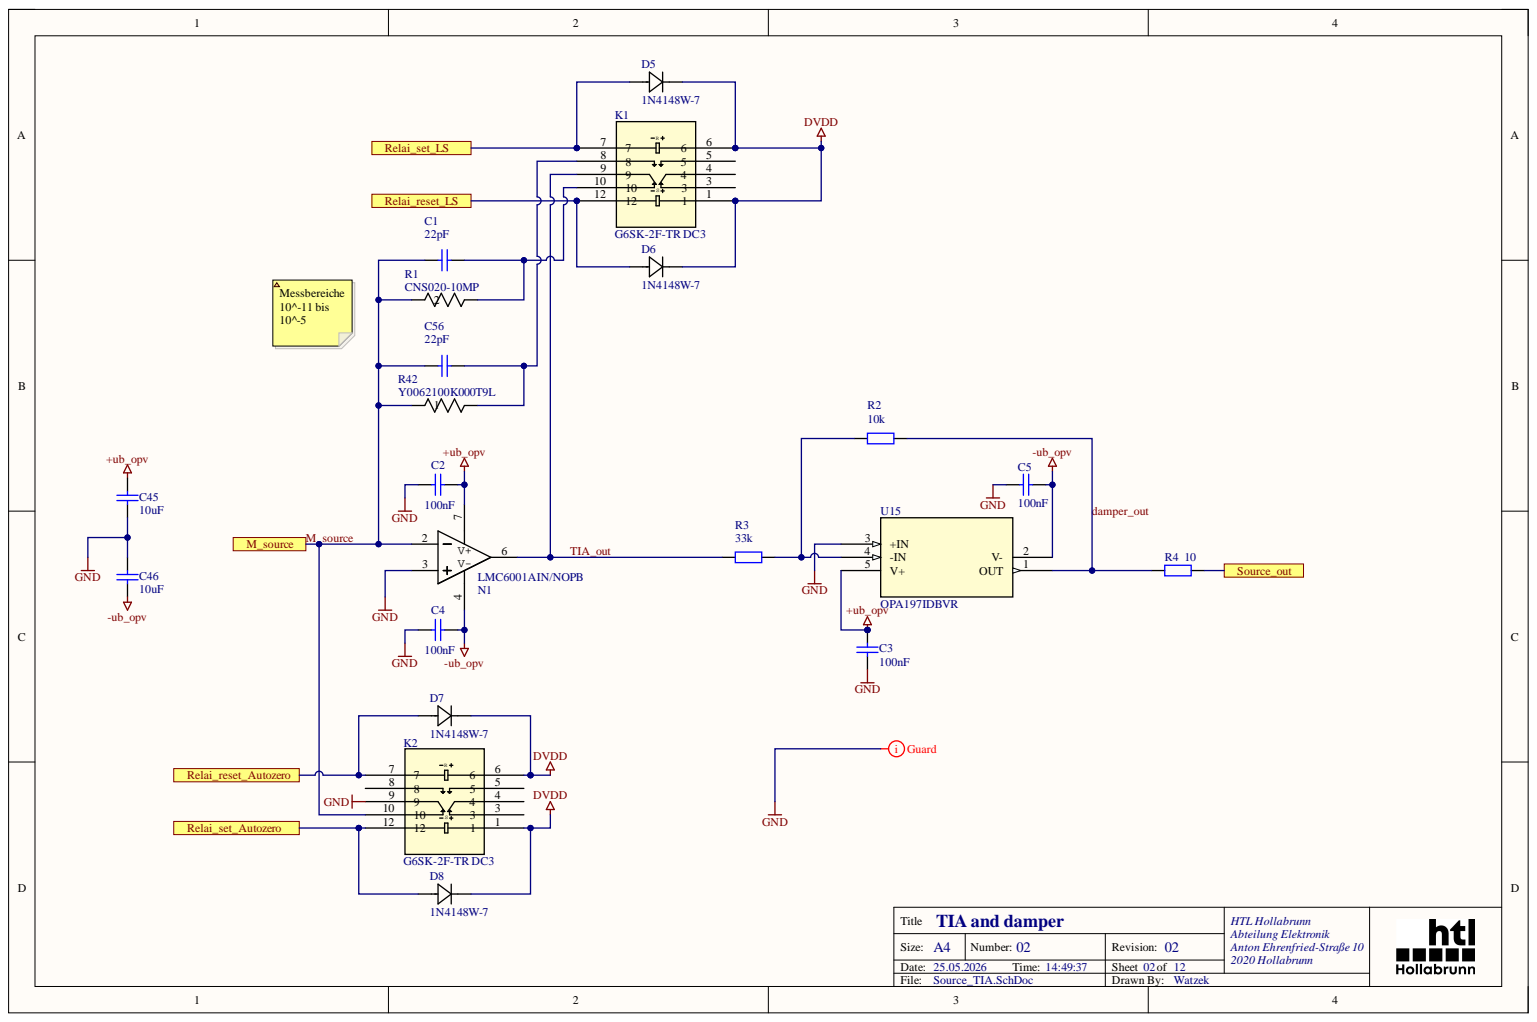
[picture p82: page 2]

12 12 10 10 9 9 8 8 7 7 1 | 1 3 3 4 4 5 5 6 6 DVDD

A4 Size: | 02 Number: | 02 Revision:
Date: 25.05.2026 Time: 14:49:37 | | Sheet of | 2020 Hollabrunn 12

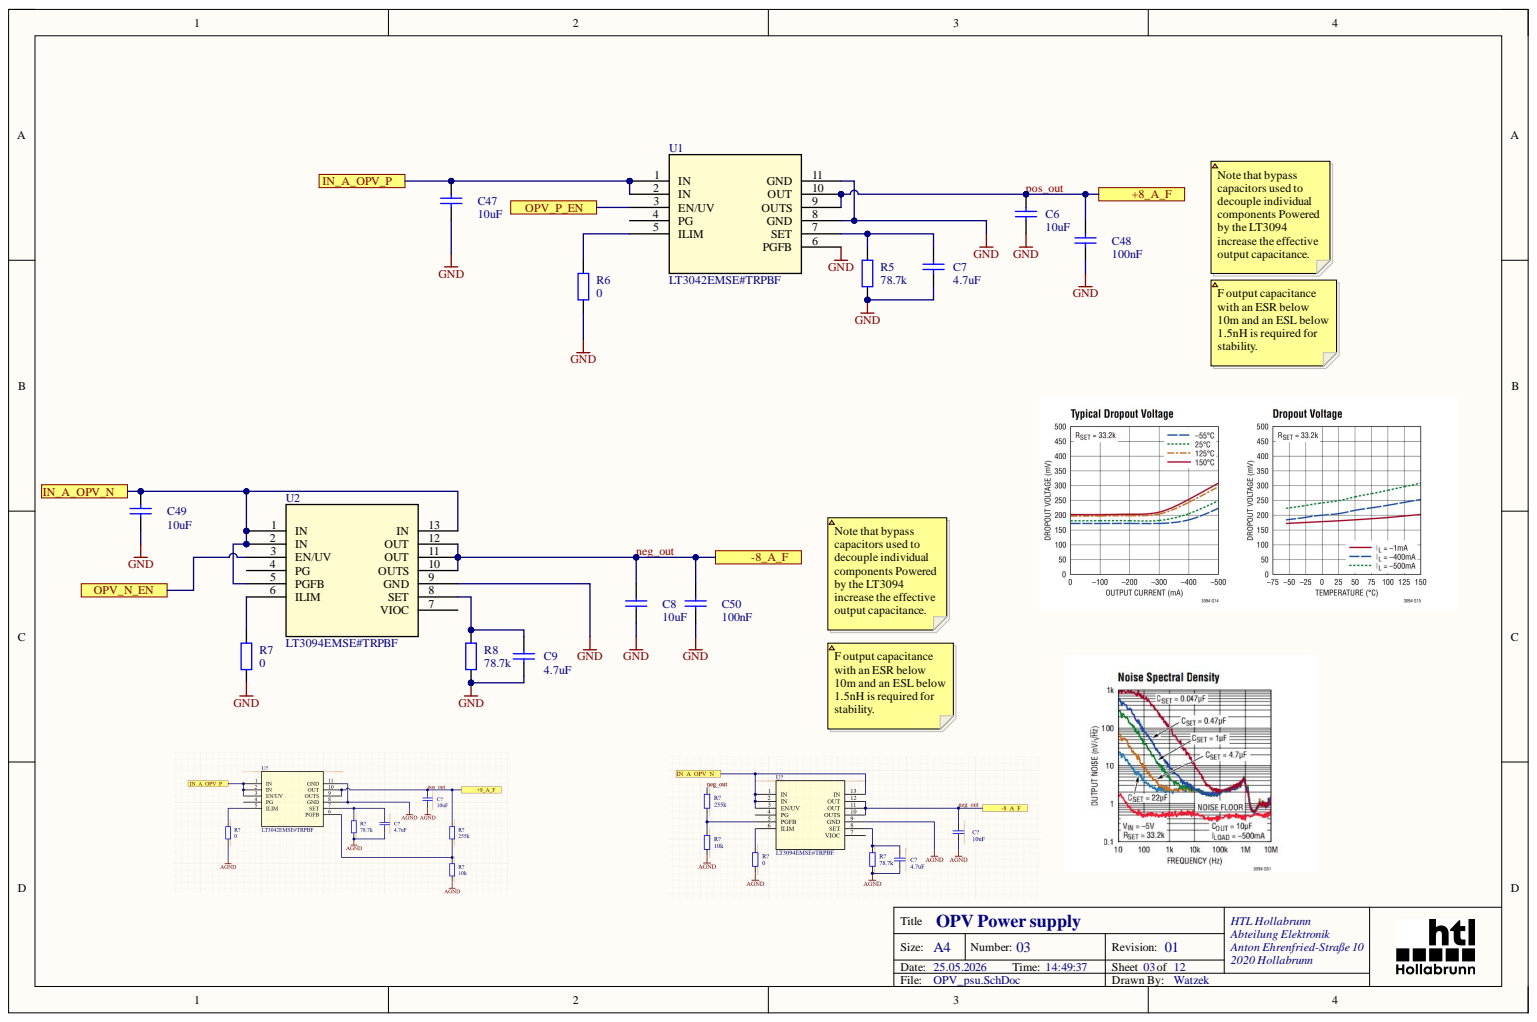
[picture p83: page 3]

F output capacitance
with an ESR below
10m and an ESL below
1.5nH is required for
stability.

A4 Size: | 03 Number: | 01 Revision:

2020 Hollabrunn 12

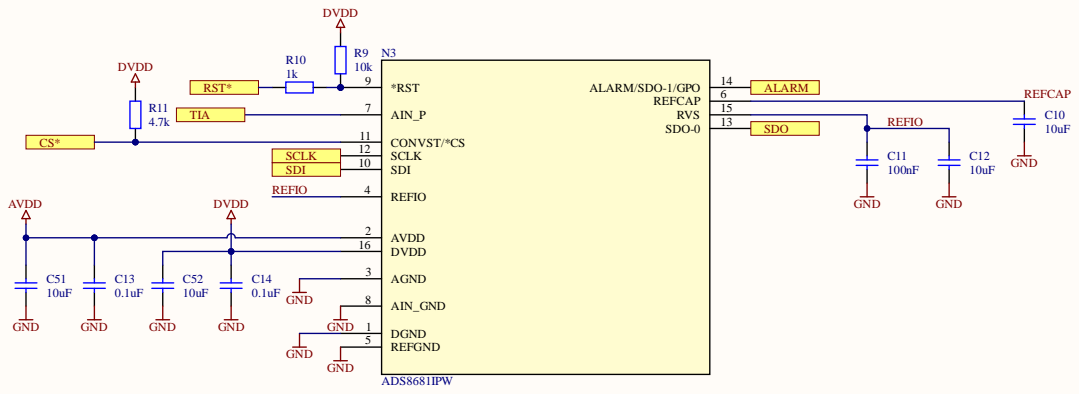
[picture p84: page 4]

A 4 Size : | N umb er : | 0 1 Rev i s i o n :
Dat e : 5.0 . T ime : : : | | Shee t o f

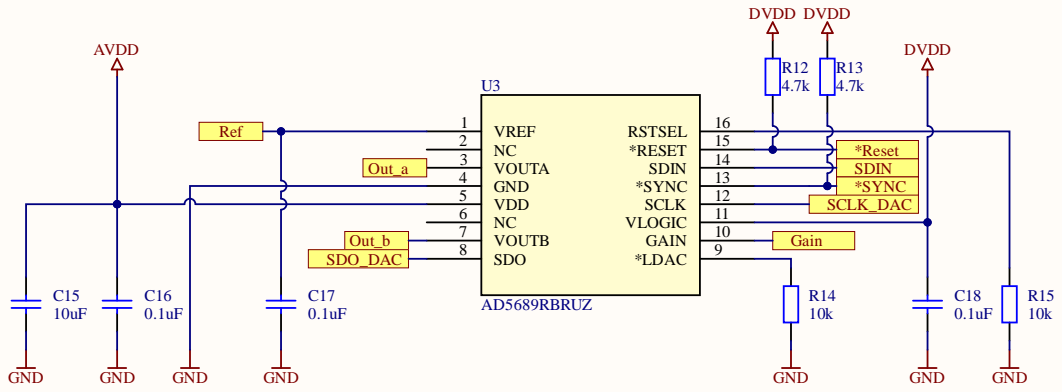
[picture p85: page 5]

14 3 SDIN

5 | | 12 1 SCLK
7 | | 1 0

A 4 Size : | N umb er : | 0 1 Rev i s i o n :
Dat e : 5.0 . T ime : : : | | Shee t o f

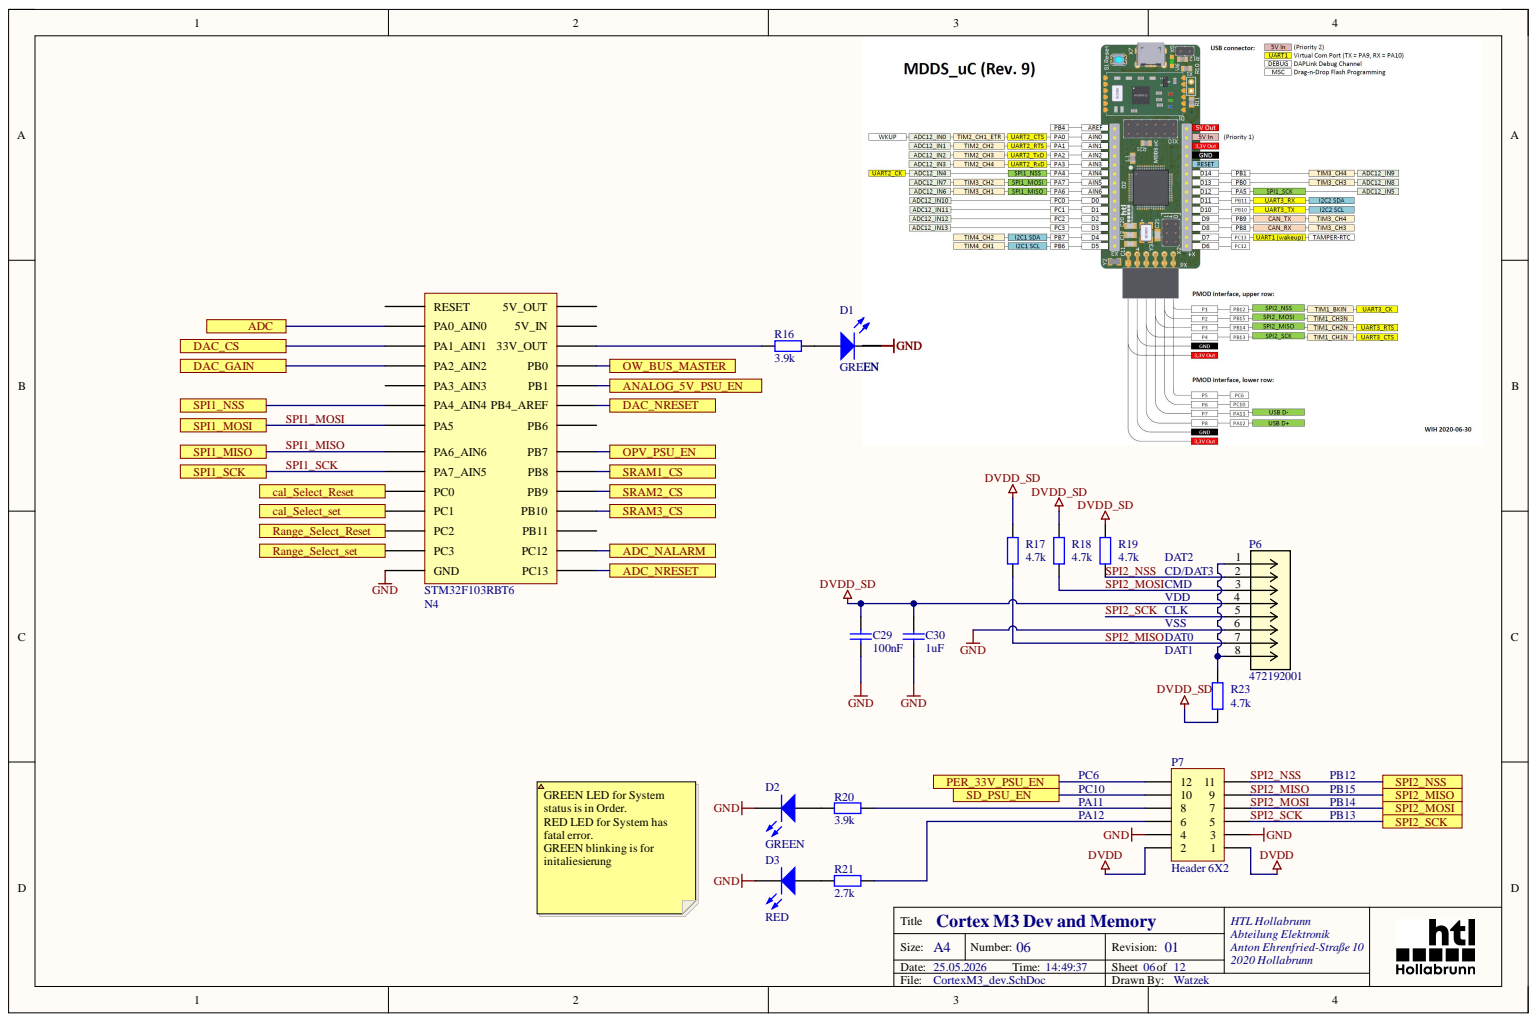
[picture p86: page 6]

GREEN LED for System
status is in Order.
RED LED for System has
fatal error.
GREEN blinking is for
initaliesierung

Cortex M3 Dev and Memory

A4 Size: | 06 Number: | 01 Revision:

2020 Hollabrunn 12

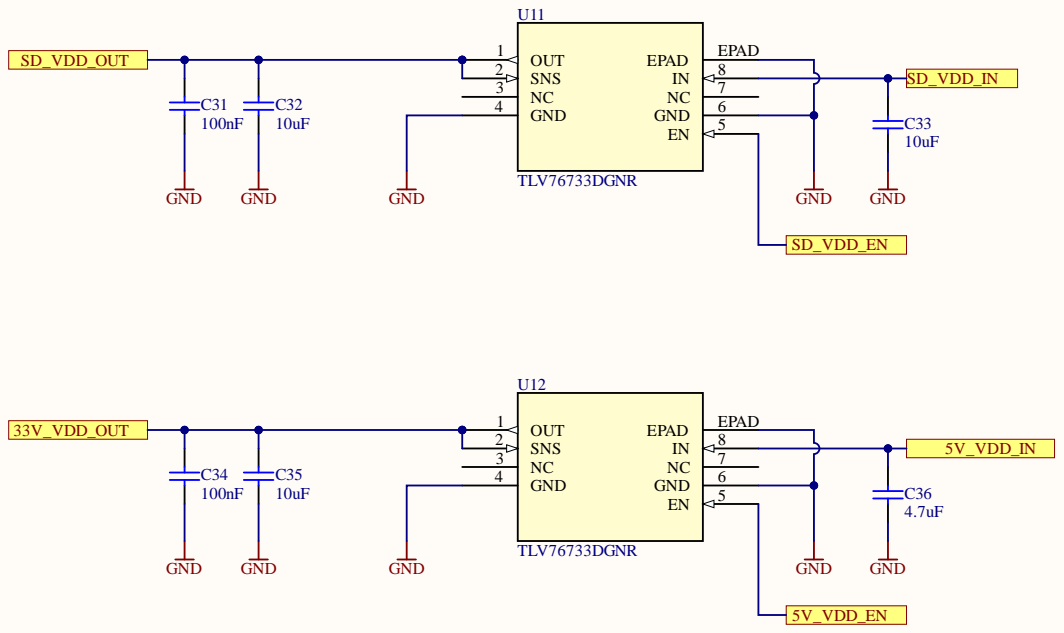
[picture p87: page 7]

A4 Size: | 07 Number: | 02 Revision:

2020 Hollabrunn 12

Drawn By: Michael Watzek

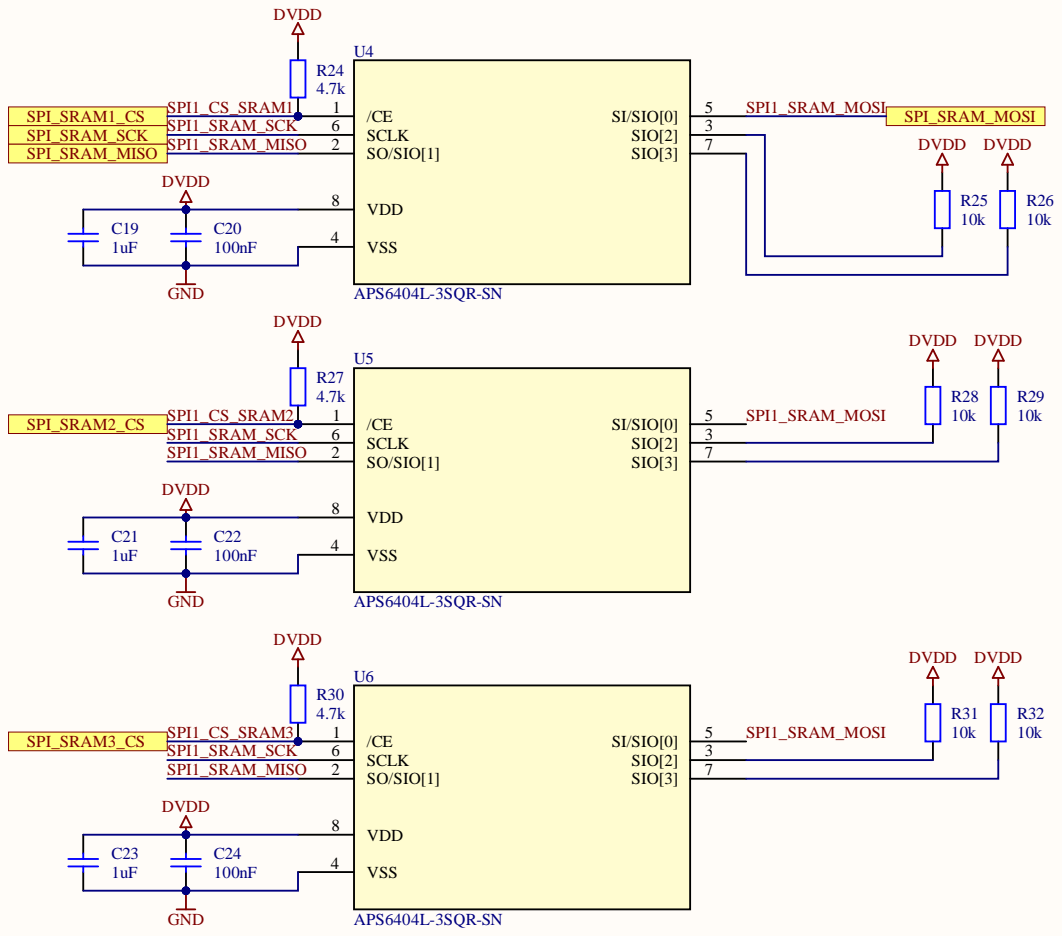
[picture p88: page 8]

A4 Size: | 08 Number: | 02 Revision:

2020 Hollabrunn 12

Drawn By: Michael Watzek

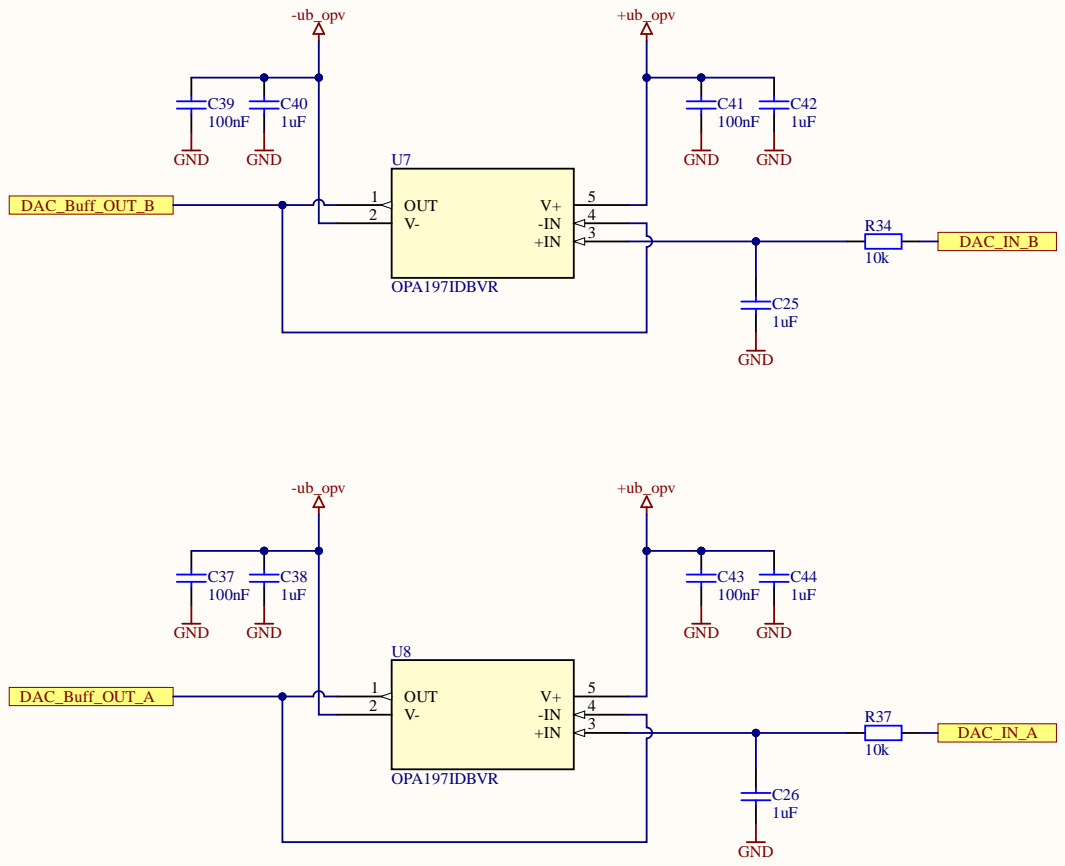
[picture p89: page 9]

A4 Size: | 09 Number: | 01 Revision:

2020 Hollabrunn 12

Drawn By: Michael Watzek

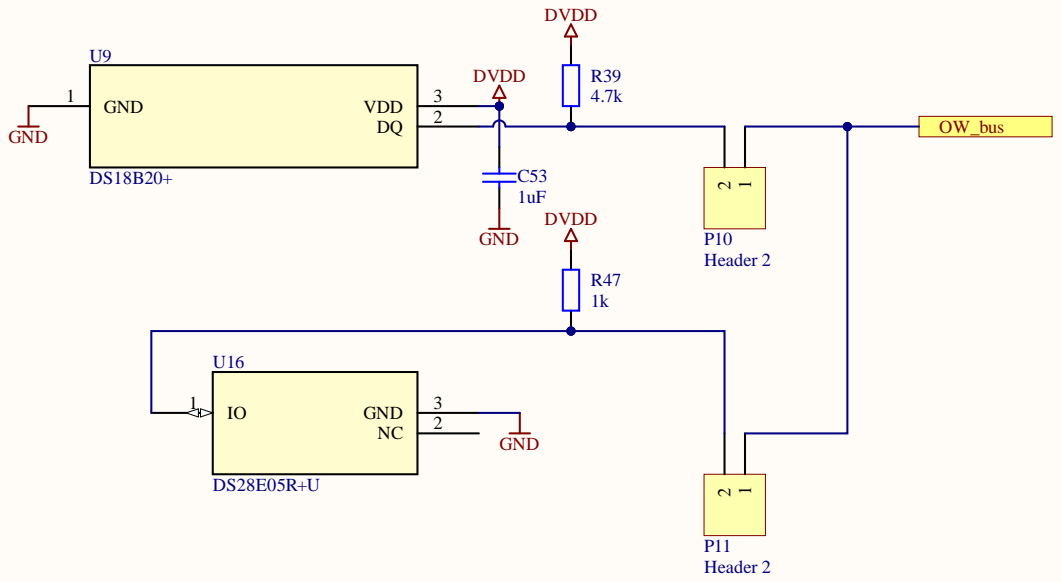
[picture p90: page 10]

A 4 Size : | N umb er : | 0 1 Rev i s i o n :
Dat e : 5.0 . T ime : : : | | Shee t o f

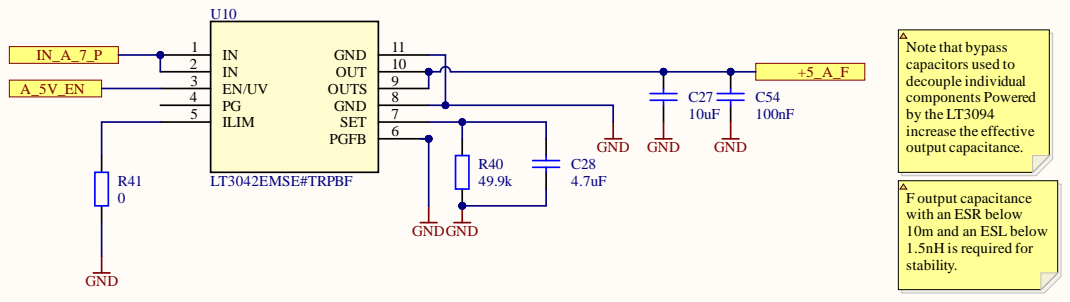
[picture p91: page 11]

6 SET 7 GND 8 OUTS 9 OUT 1

A 4 Size : | N umb er : | 0 2 Rev i s i o n :
Dat e : 5.0 . T ime : : : | | Shee t o f

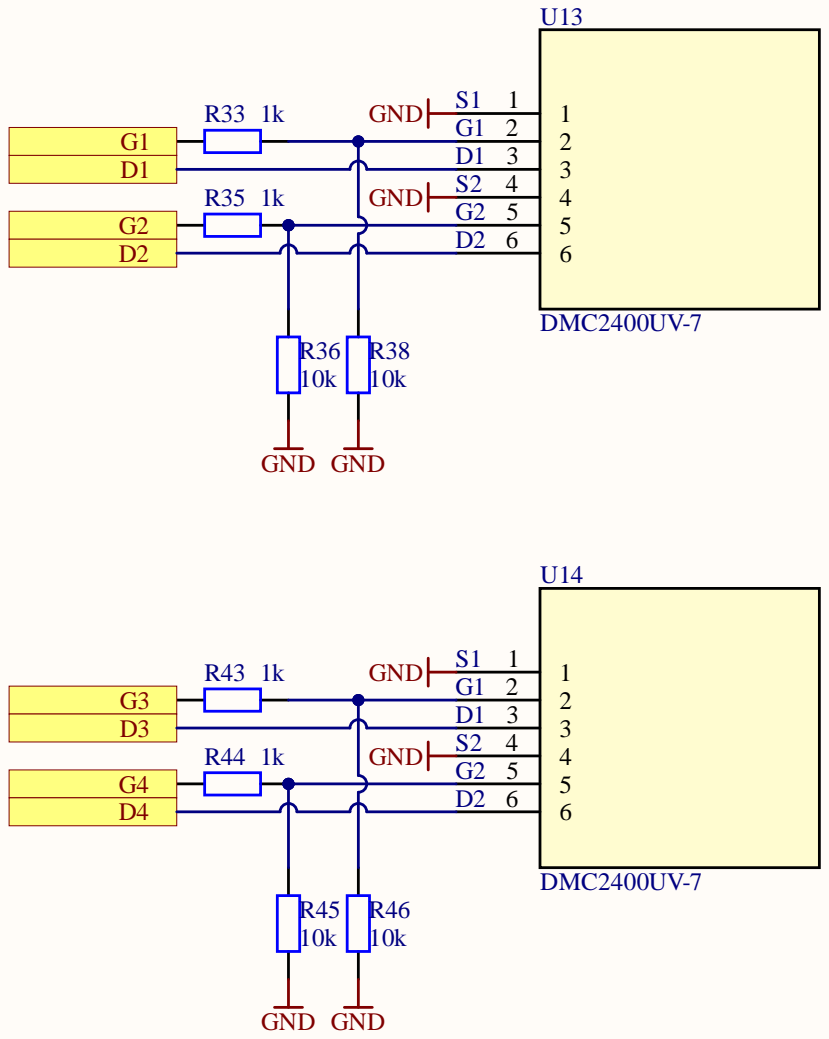
[picture p92: page 12]

A4 Size: | 12 Number: | 01 Revision:

2020 Hollabrunn 12

Drawn By: Michael Watzek

Comment | Description | Designator | Footprint | LibRef | Quantity
22pF | Capacitor | C1, C56 | C1206-KUE | Capacitor | 2
100nF | Capacitor | C2, C3, C4, C5, C11, C20, C22, C24, C29, C31, C34, C37, C39, C41, C43, C48, C50, C54, C55 | C1206-KUE | Capacitor | 19
10uF | Capacitor | C6, C8, C10, C12, C15, C27, C32, C33, C35, C45, C46, C47, C49, C51, C52 | C1206-KUE | Capacitor | 15
4.7uF | Capacitor | C7, C9, C28, C36 | C1206-KUE | Capacitor | 4
0.1uF | Capacitor | C13, C14, C16, C17, C18 | C1206-KUE | Capacitor | 5
1uF | Capacitor | C19, C21, C23, C25, C26, C30, C38, C40, C42, C44, C53 | C1206-KUE | Capacitor | 11
GREEN | Typical INFRARED GaAsLED | D1, D2 | 6-0805_N-KUE | LED0 | 2
RED | Typical INFRARED GaAsLED | D3 | 6-0805_N-KUE | LED0 | 1
1N4148W-7 | Description | D5, D6, D7, D8 | SOD123_DIO | 1N4148W-7 | 4
G6SK-2F-TRDC3 | Description | K1, K2 | RELAY_G6SK-2F DC3_OMR | G6SK-2F-TRDC3 | 2
LMC6001AIN/NOPB | Ultra-LowInput Current Amplifier 8-PDIP-40to 85 | N1 | DIP8 | LMC6001AINNOPB | 1
ADS8681IPW | 16-bit, 1MSPS1-chSAR ADCwith programmable(Â±12V, Â±10V, Â±6V, Â±5V, Â±2.5V)input ranges on5Vsupply16-TSSOP-40to125 | N3 | PW16_TEX | ADS8681IPW | 1
STM32F103 | | N4 | DIP28 | STM32F103 | 1
BNC | BNCElbowConnector | P1, P2, P3, P9 | BNC_RACON | BNC | 4
Header 4 | Header, 4-Pin | P4 | HDR1X4 | Header 4 | 1
Header 2 | Header, 2-Pin | P5, P8, P10, P11, P12 | HDR1X2 | Header 2 | 5
472192001 | 1.10mmPitch microSD CardConnector, Hinge Type, Lead-Free | P6 | CONN_47219-2001_MOL | 472192001 | 1
Header 6X2 | Header, 6-Pin, Dual row | P7 | HDR2X6 | Header 6X2 | 1
CNS020-10MP | CNS02010K0,02%e2 | R1 | RES_CNS020_VIS | CNS020-10KP | 1
10k | Resistor SMD | R2, R9, R14, R15, R25, R26, R28, R29, R31, R32, R34, R36, R37, R38, R45, R46 | C1206-KUE | ResistorSMD | 16
33k | Resistor SMD | R3 | C1206-KUE | ResistorSMD | 1
10 | Resistor SMD | R4 | C1206-KUE | ResistorSMD | 1
78.7k | Resistor SMD | R5, R8 | C1206-KUE | ResistorSMD | 2
0 | Resistor SMD | R6, R7, R41 | C1206-KUE | ResistorSMD | 3
1k | Resistor SMD | R10, R33, R35, R43, R44, R47 | C1206-KUE | ResistorSMD | 6
4.7k | Resistor SMD | R11, R12, R13, R17, R18, R19, R23, R24, R27, R30, R39 | C1206-KUE | ResistorSMD | 11
3.9k | Resistor SMD | R16, R20 | C1206-KUE | ResistorSMD | 2
2.7k | Resistor SMD | R21 | C1206-KUE | ResistorSMD | 1
49.9k | Resistor SMD | R40 | C1206-KUE | ResistorSMD | 1
Y0062100K000T9L | NoDescription Available | R42 | RES_S102K_7P62X2P6 7_VIS | Y0062100K000T9L | 1
LT3042EMSE#TRPBF | 20V, 200mA, Ultralow Noise, UltrahighPSRR RFLinear Regulator | U1, U10 | 05-08-1664_ADI | LT3042EMSETRPBF | 2
LT3094EMSE#TRPBF | âˆ ’20V, 500mA, UltralowNoise, UltrahighPSRR NegativeLinear Regulator | U2 | MSE_05-08-1666_ADI | LT3094EMSETRPBF | 1
AD5689RBRUZ | Dual, 16-Bit nanoDAC+ with 2ppm/Â°C Reference, SPI Interface | U3 | RU_16_ADI | AD5689RBRUZ | 1
APS6404L-3SQR-SN | Description | U4, U5, U6 | APS6404L-3SQR-SN_APY | APS6404L-3SQR-SN | 3
OPA197IDBVR | Single, 36-V, precision, rail-to-rail input output, lowoffset voltageop amp5-SOT-23-40to 125 | U7, U8, U15 | DBV5_TEX | OPA197IDBVR | 3
DS18B20+ | Programmable Resolution1-Wire Digital Thermometer | U9 | 21-0248A_Q3-1_MXM | DS18B20+ | 1
TLV76733DGNR | Adjustable- andfixed-output, 1-A, 16-V, positive-voltagelow-dropout (LDO)linear regulator 8-HVSSOP-40to125 | U11, U12 | VSSOP8_DGN_TEX | TLV76733DGNR | 2
DMC2400UV-7 | Description | U13, U14 | SON_400UV-7_DIO | DMC2400UV-7 | 2
DS28E05R+U | 1-WireEEPROM | U16 | 21-0051H_MXM | DS28E05R+U | 1
