SmichaelSmolley/Diplom_Arbeit/Dokumentation/Device_01_idvg_23_09_26_SAFDAT_log.pdf

## Device 01 IDVG

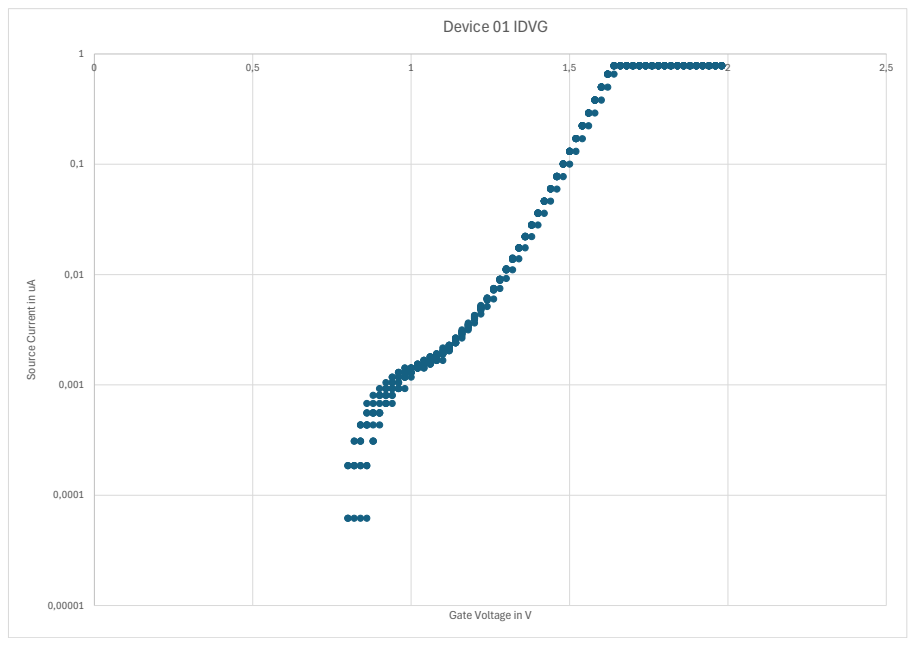
[picture p94: page 1]
2,5 Source Current in uA

Gate Voltage in V
