SmichaelSmolley/Diplom_Arbeit/Dokumentation/Device#01_idvg_05_10.pdf

## Source Current (device #01)

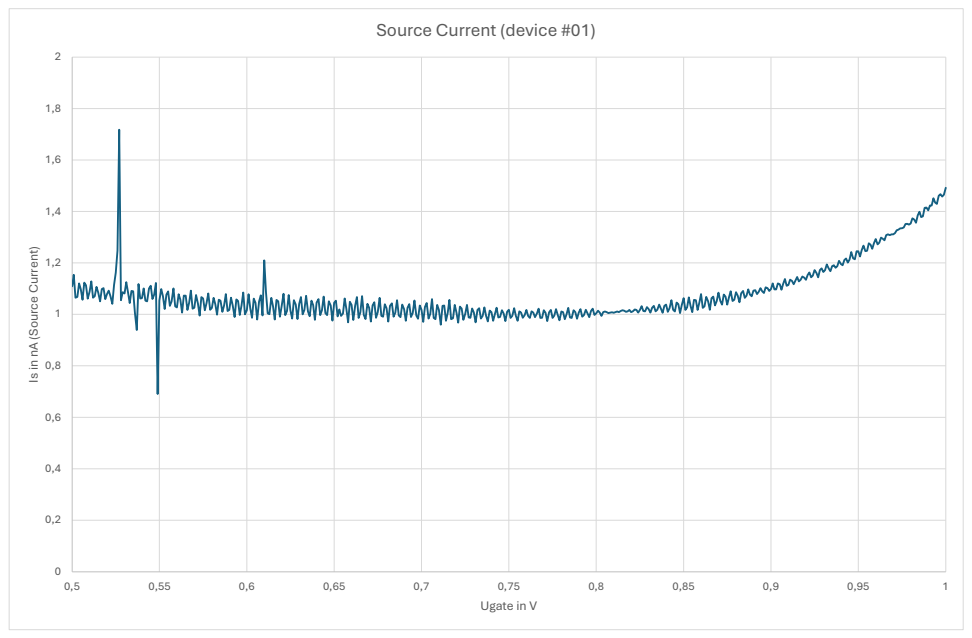
[picture p95: page 1]
1 Is in nA ⁽Source Current); Ugate in V
