SmichaelSmolley/Diplom_Arbeit/Software/firmware/Unterlagen_ELLFI/2 Klasse EL/PWM Generator.pdf

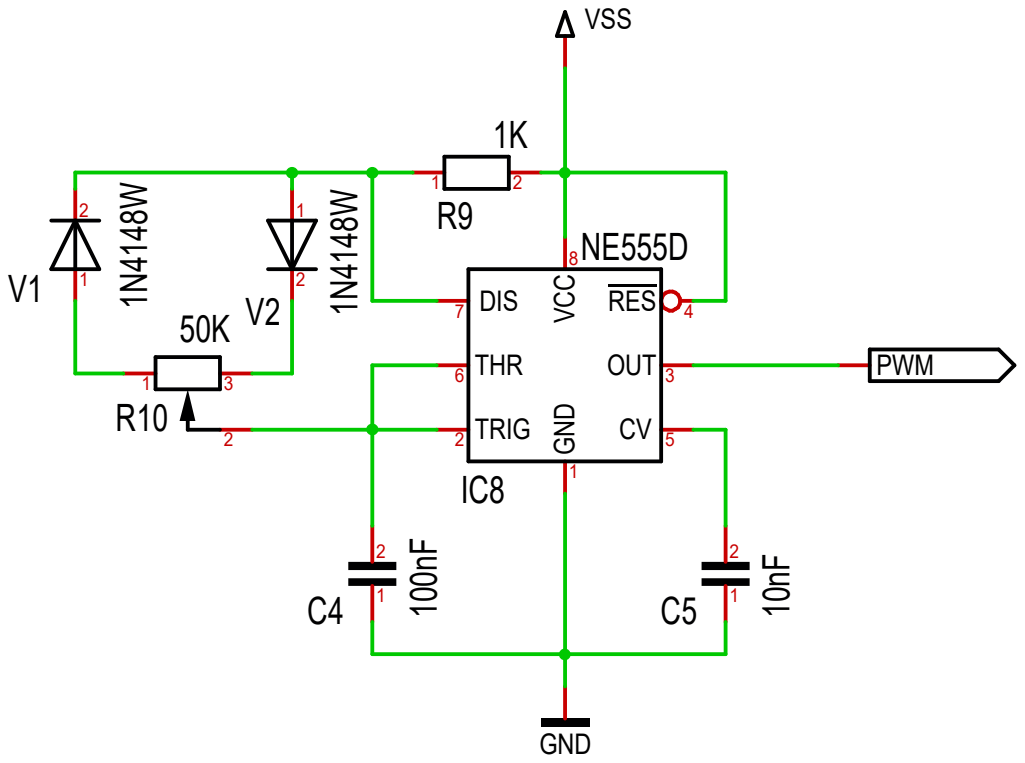
[picture p96: page 1]
ELLFi; 1N⁴¹⁴⁸W2; 1N⁴¹⁴⁸W; GND; VSS; PWM; 7 VCCDIS; 6 THR; 5 RES; 4 OUT 3; 2 TRIG; 1GND; Hauptplatine Robo V65.T3001; Ausgabe; Projekt; Datei

Maßstab 98,00% | Firma HTL Hollabrunn | Zeichner Frasl | Blatt 2

Änderung 11.12.17 09:20 | | Titel PWM Generator
