SmichaelSmolley/Diplom_Arbeit/Software/firmware/MDDS_Unterlagen_neu/MDDS_BaseBoard/Rev05/MDDS_BaseBoard_Rev05_Pinning.pdf

# MDDS-Base Board (Rev.5)

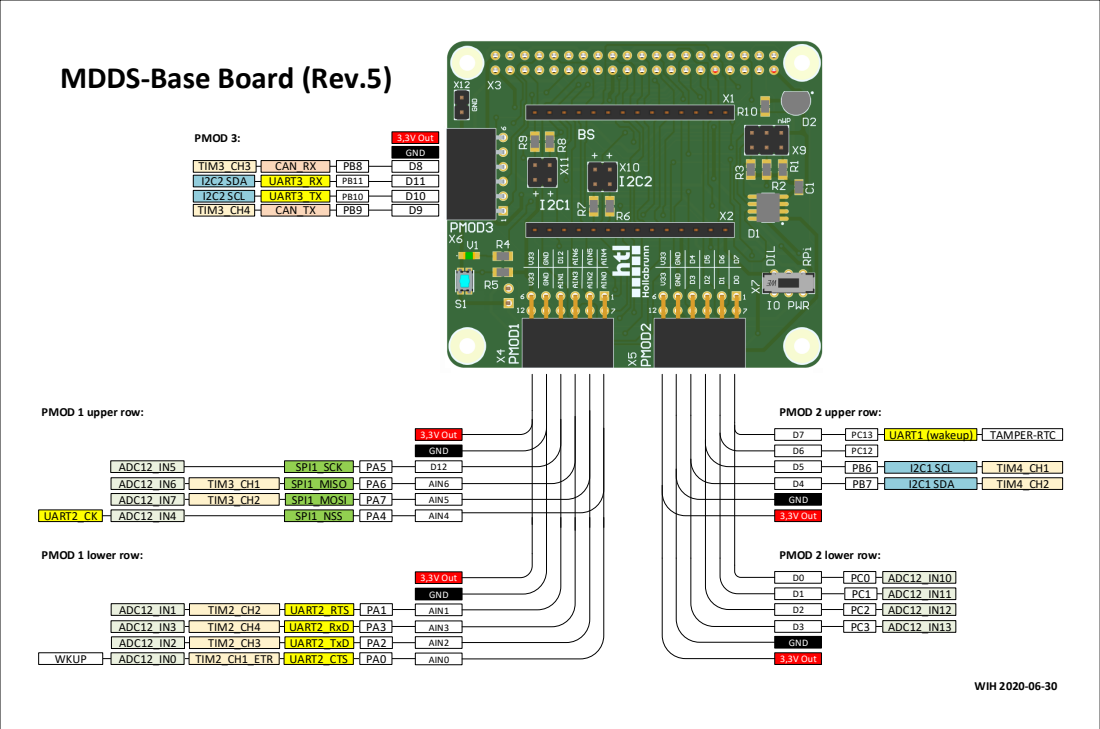
[picture p97: page 1]

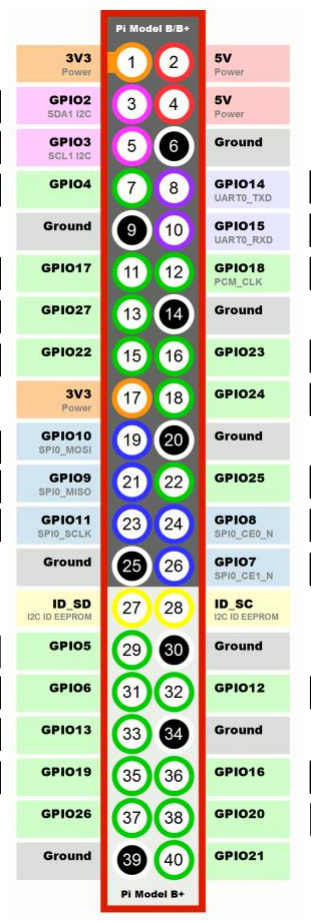
[picture p98: figure]

D11
D10 | PB10 PB11
UART3_TX
UART3_RX | I2C2 SDA I2C2 SCL

# MDDS-Base Board (Rev.5)

# BaseBoard connected

to Raspberry Pi B+/...

D6 | PC12
D7 | PC13 | UART1 (wakeup) | TAMPER-RTC
D13 | PB0 | TIM3_CH3 | ADC12_IN8

WIH 2020-06-30

D14 | PB1 | TIM3_CH4 | ADC12_IN9

## Mögliche Kommunikations-Verbindungen:

## Raspberry UART0 <-> CM3 UART3

Raspberry I²C | <-> CM3 I²C1
Raspberry SPI | <-> CM3 SPI1
AIN4 | PA4 | SPI1_NSS | UART2_CK | ADC12_IN4
AIN0 | PA0 | UART2_CTS | TIM2_CH1_ETR | ADC12_IN0 | WKUP
D8 | PB8 | CAN_RX | TIM3_CH3
| TIM4_CH2 | I2C1 SDA | PB7 | D4
| TIM4_CH1 | I2C1 SCL | PB6 | D5
ADC12_IN1 | TIM2_CH2 | UART2_RTS | PA1 | AIN1
| TIM3_CH4 | CAN_TX | PB9 | D9
| | | PA2 | AIN2
| | | PA3 | AIN3

ADC12_IN2
ADC12_IN3

TIM2_CH3
TIM2_CH4

UART2_TxD
UART2_RxD

AIN5

AIN6
PA7

PA6
ADC12_IN7

ADC12_IN6
SPI1_MOSI

TIM3_CH1 SPI1_MISO
TIM3_CH2
ADC12_IN5 | SPI1_SCK | PA5 | D12

D1
D2
D3

PC1
PC2
PC3

ADC12_IN11
ADC12_IN12
ADC12_IN13
ADC12_IN10 | PC0 | D0

RESET

AREF | PB4
