SmichaelSmolley/Diplom_Arbeit/Software/firmware/MDDS_Unterlagen_neu/MDDS_BaseBoard/Rev05/MDDS_BaseBoard_Rev05_Schaltplan.pdf

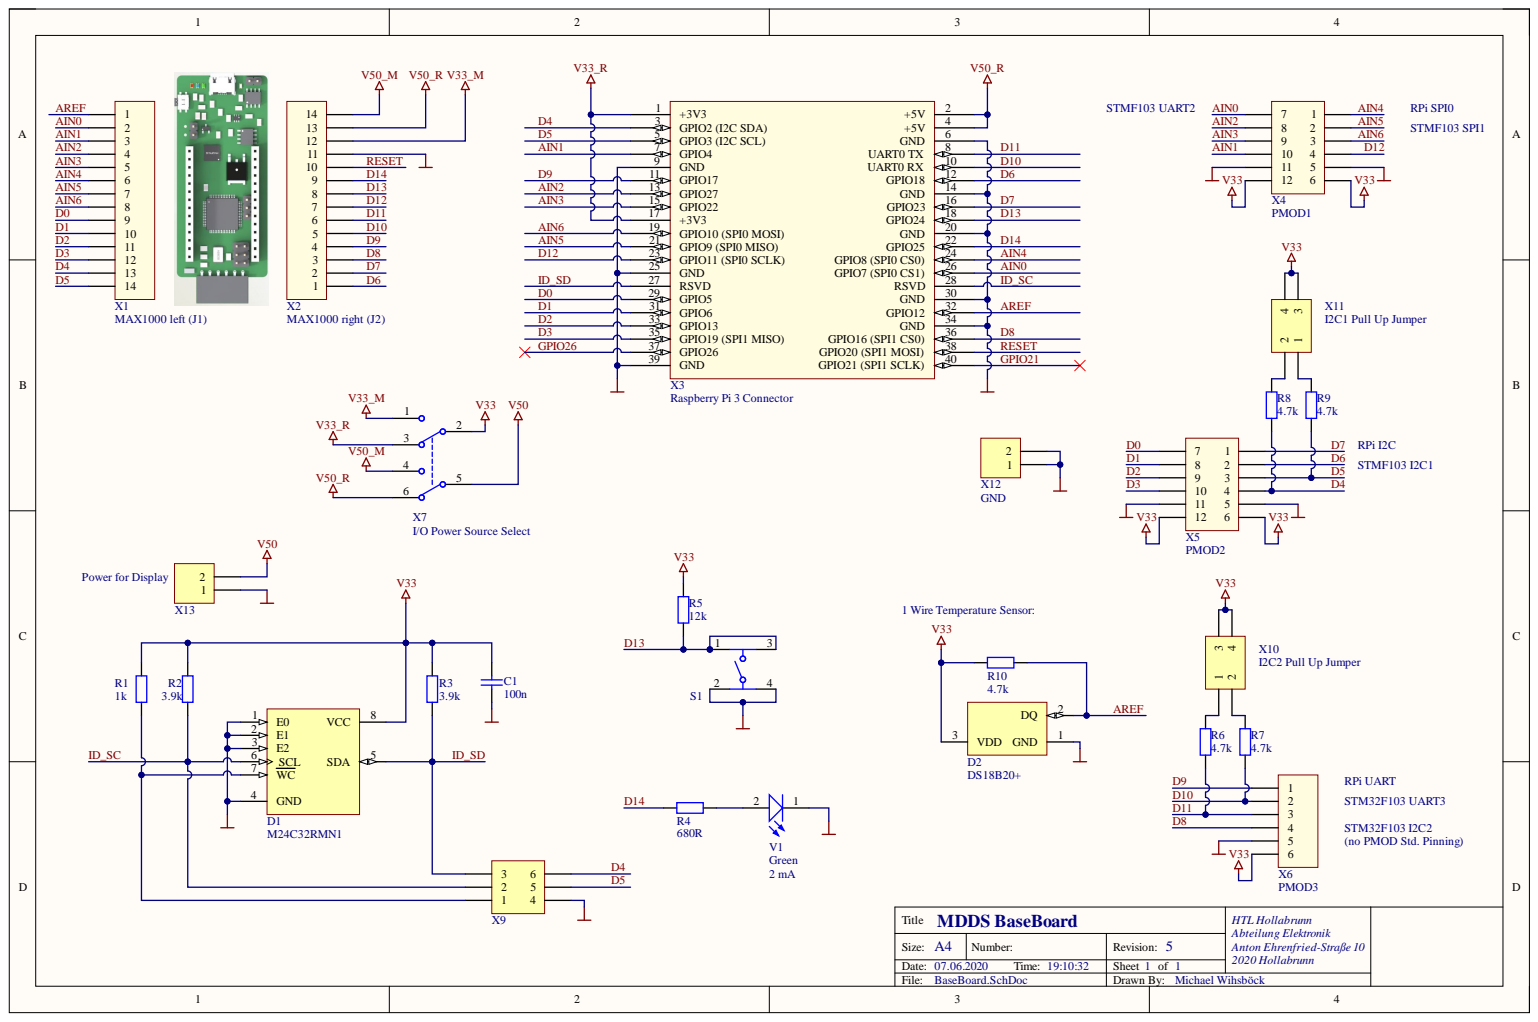
[picture p99: page 1]

E1 2
E2 3

STM32F103 I2C2
(no PMOD Std. Pinning)

Size: A4 | Number: | Revision: 5
Date: 07.06.2020 Time: 19:10:32 | | Sheet 1 of | 2020 Hollabrunn 1

Drawn By: Michael Wihsböck
