SmichaelSmolley/Diplom_Arbeit/Software/firmware/MDDS_Unterlagen_neu/MDDS_DisplayAdapterBoard/Rev01/MDDS_DisplayAdapterBoard_Rev01_Schaltplan.pdf

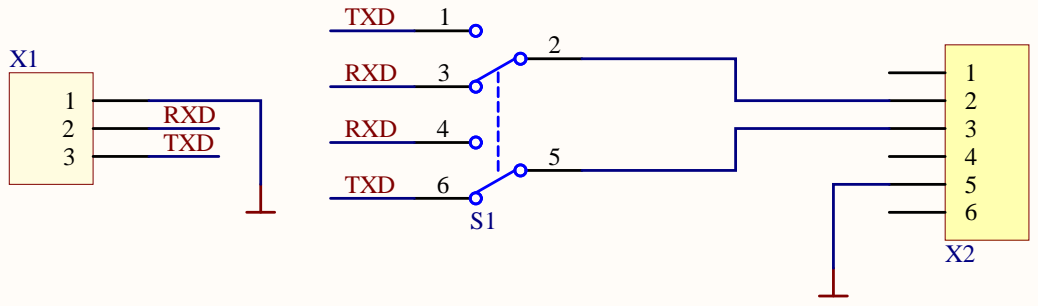
[picture p100: page 1]

PMOD Host-Peri Switch

Size: Size: A A 4 4 | N N u u mber: mber: DA DA 2 2 0 0 2 2 0 0 _ _ 6 6 | Rev Rev i i s s i i o o n n : : V V 0 0 1 1
Date: Date: 0 0 6.0 6.0 9 9 . . 2 2 0 0 2 2 0 0 Ti Ti me: me: 1 1 6 6 : : 0 0 0 0 : : 0 0 1 1 | | Shee Shee t t 1 1 o o f f 1 1
