SmichaelSmolley/Diplom_Arbeit/Software/firmware/MDDS_Unterlagen_neu/MDDS_BaseBoard/Rev05/Fertigungsdokumente/MDDS_BaseBoard_Rev05_Bestueckungsplan.pdf

### View from Front side (Scale 2:1)

# MDDS BaseBoard Rev. 5 Bestückungsplan

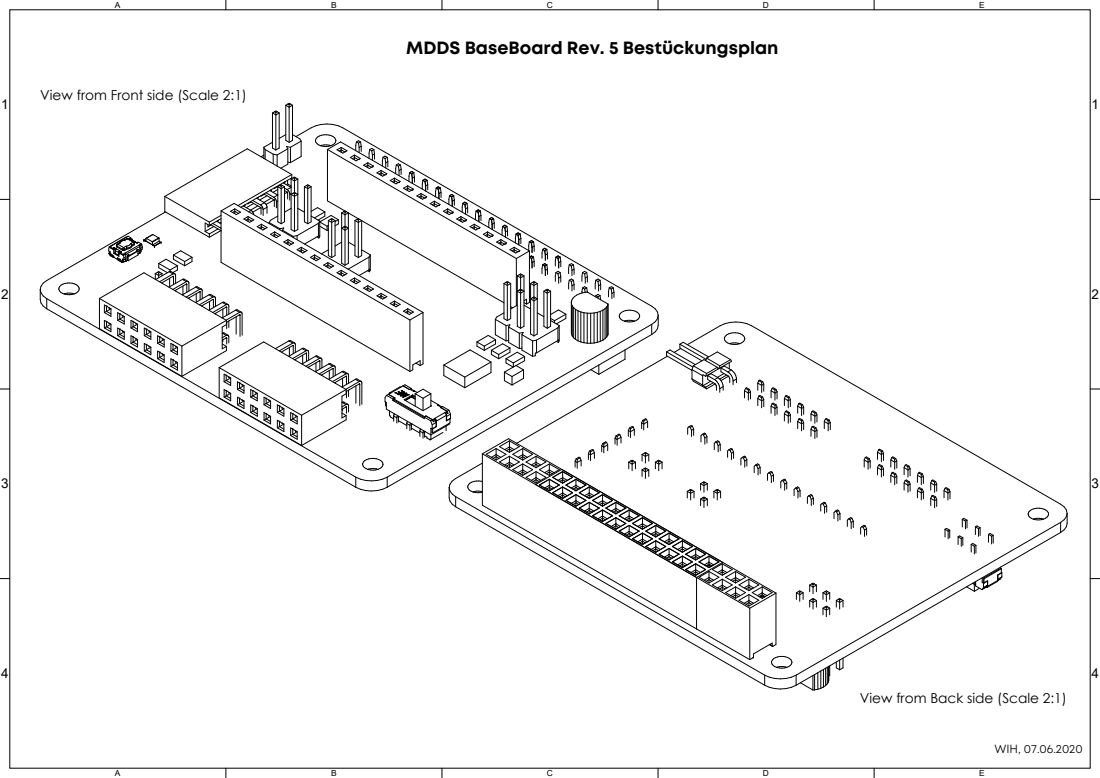
[picture p101: page 1]
WIH, 07.06.2020

View from Back side (Scale 2:1)

### View from Top side (Scale 3)

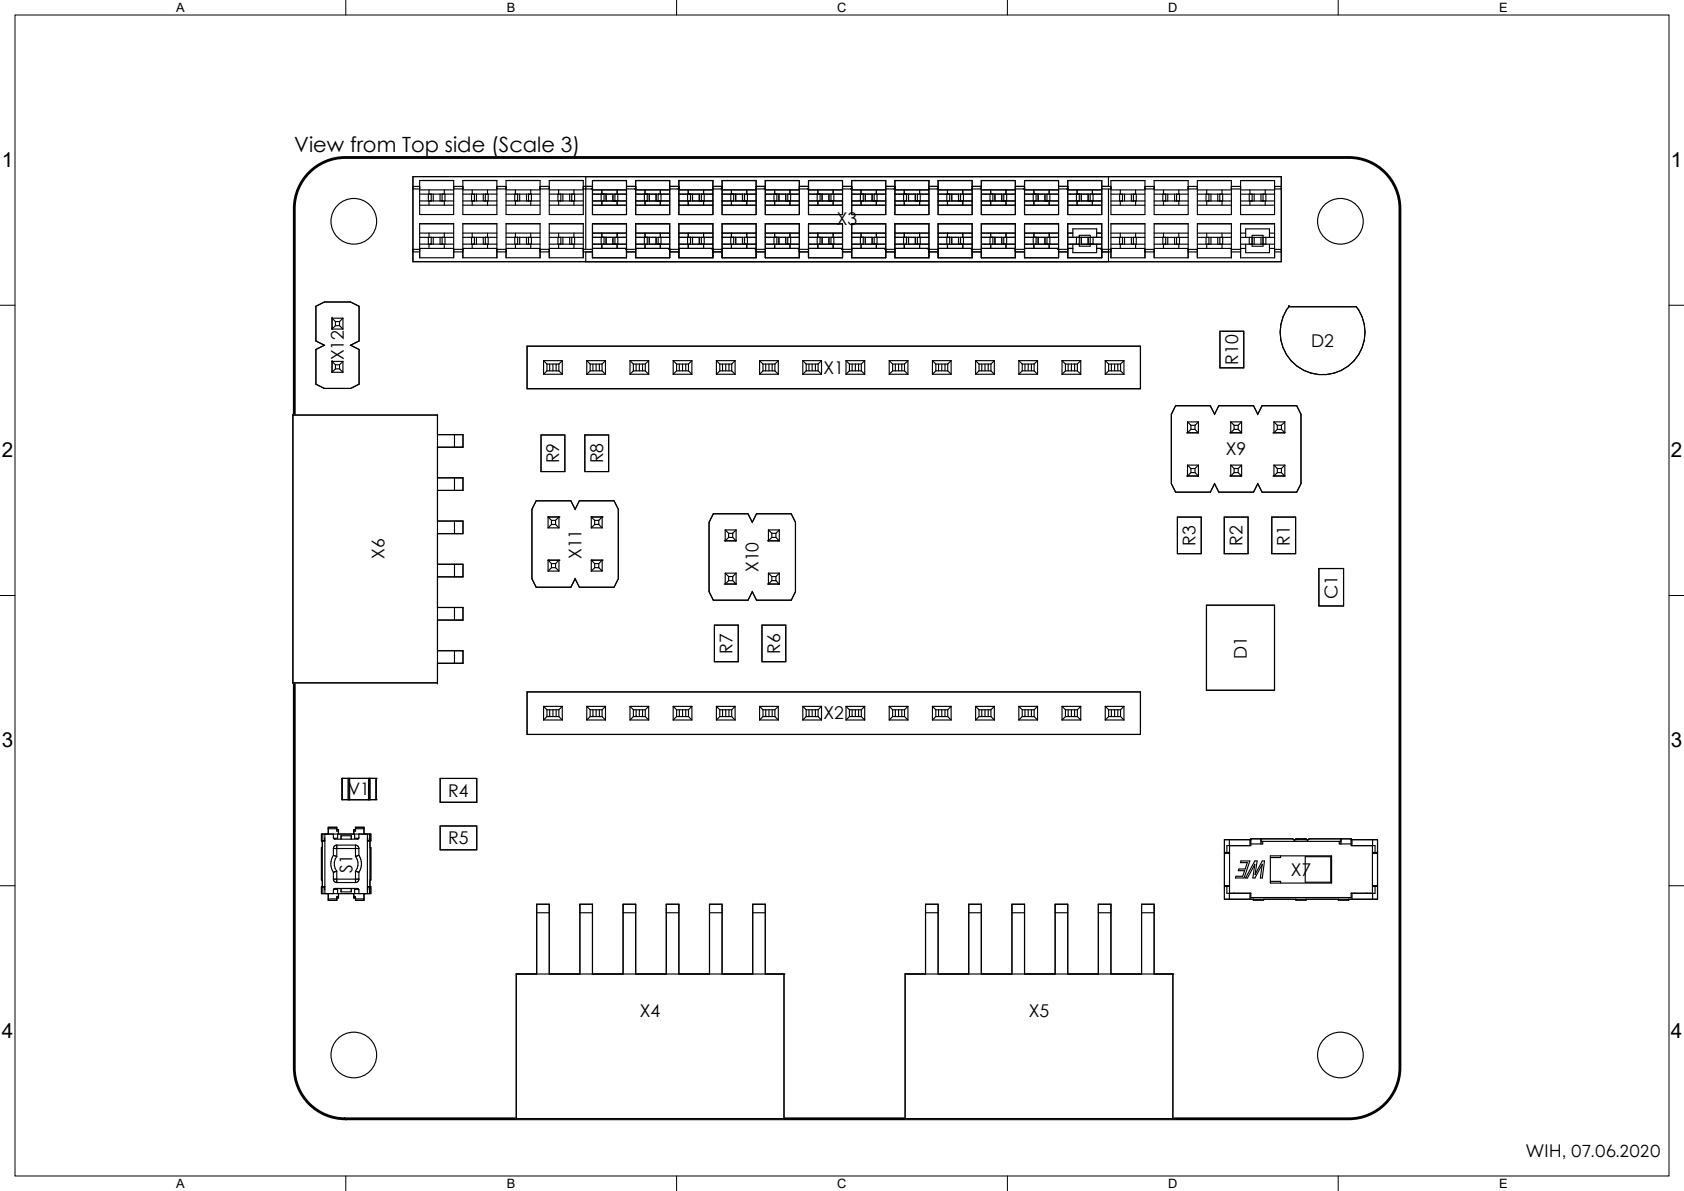
[picture p102: page 2]

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
| Designator | Name | | Description
| R1 | 1k | | Resistor 0805 5% 0.125W
| R2, R3 | 3.9k | | Resistor 0805 5% 0.125W
| R6, R7, R8, R9, R10 | 4.7k | | Resistor 0805 5% 0.125W
| R5 | 12k | | Resistor 0805 5% 0.125W
| C1 | 100n | | Capacitor
| R4 | 680R | | Resistor 0805 5% 0.125W
Line # 29 | S1 | 434153017835 | | 3.5x2.9mm SMD J-Bend WS-TASV, height 1.7 mm, 350 gf
| D2 | DS18B20+ | Quantity 1251111111114111111 | Programmable Resolution Digital Thermometer, 1-Wire Interface, ±0.5°C Accuracy, 3-Pin TO92, -55°C to +125°C, Pb-Free
| X12 | GND | | WR-PHD 2.54 mm THT Pin Header, 02p
| X11 | I2C1 Pull Up Jumper | | WR-PHD 2.54 mm THT Dual Pin Header, 04p
| X10 | I2C2 Pull Up Jumper | | WR-PHD 2.54 mm THT Dual Pin Header, 04p
| X7 | I/O Power Source Select | | WS-SLTV THT Mini Slide Switch, Same Side Connection, DPDT
| | Jumper | | 2 Position Jumper with test point
| V1 | LED Green 2mA | | SMD LED green 0805 2mA
| D1 | M24C32RMN1 | | 32 Kbit Serial I²C Bus EEPROM
| X1 | MAX1000 left (J1) | | WR-PHD 2.54 mm Socket Header, 14p
10 | X2 | MAX1000 right (J2) | | WR-PHD 2.54 mm Socket Header, 14p
11 | X3 | Raspberry Pi 3 Connector | | GPIO Header for Raspberry Pi A+/B+/Pi 2/Pi 3 - 2x20
12 | X4 | PMOD1 | | WR-PHD 2.54 mm Angled Dual Socket Header, 12p

### Bill Of Materials

1 | 1
2 | 2
3 | 3
4 | 4
Line # | Designator | Name | Quantity | Description
13 | X5 | PMOD2 | 1 | WR-PHD 2.54 mm Angled Dual Socket Header, 12p
14 | X6 | PMOD3 | 1 | WR-PHD 2.54 mm Angled Socket Header, 6p
15 | X13 | 02p | 1 | WR-PHD 2.54 mm THT Pin Header, 02p
17 | X9 | 06p | 1 | WR-PHD 2.54 mm THT Dual Pin Header, 06p

### Bill Of Materials
