SmichaelSmolley/Diplom_Arbeit/Software/firmware/MDDS_Unterlagen_neu/MDDS_uC/Rev09/Fertigungsdokumente/MDDS_uC_Rev09_Bestueckungsplan.pdf

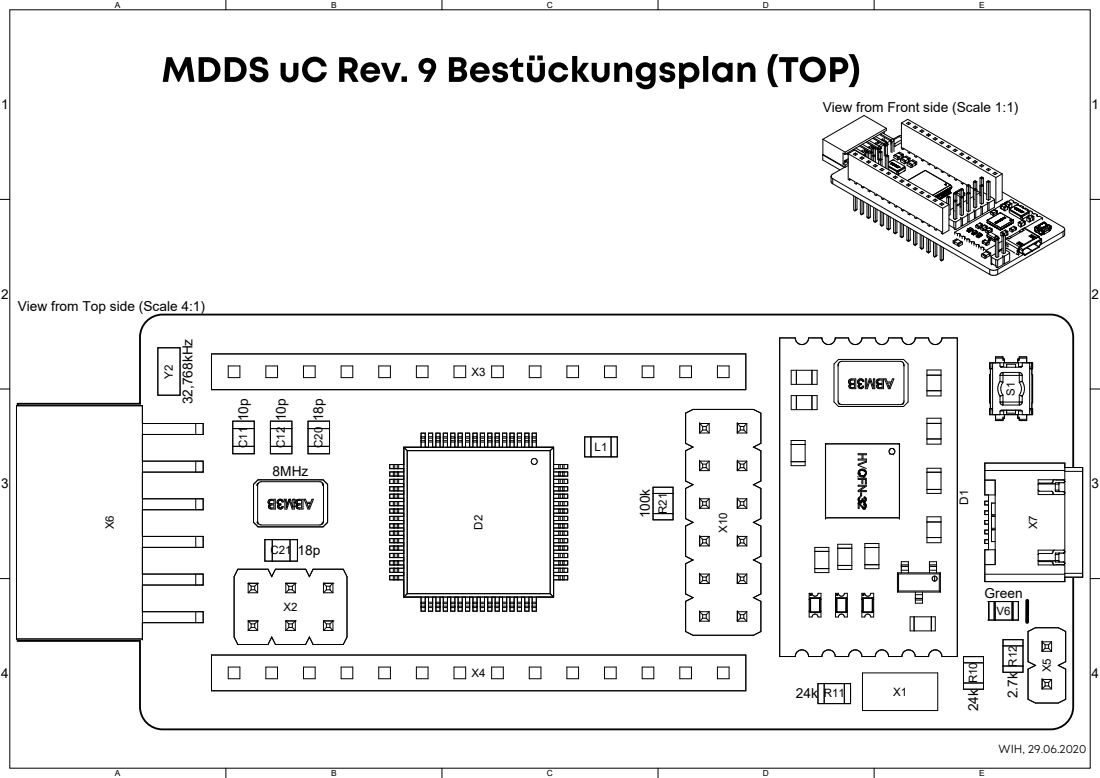
[picture p104: page 1]

View from Front side (Scale 1:1)

View from Top side (Scale 4:1)

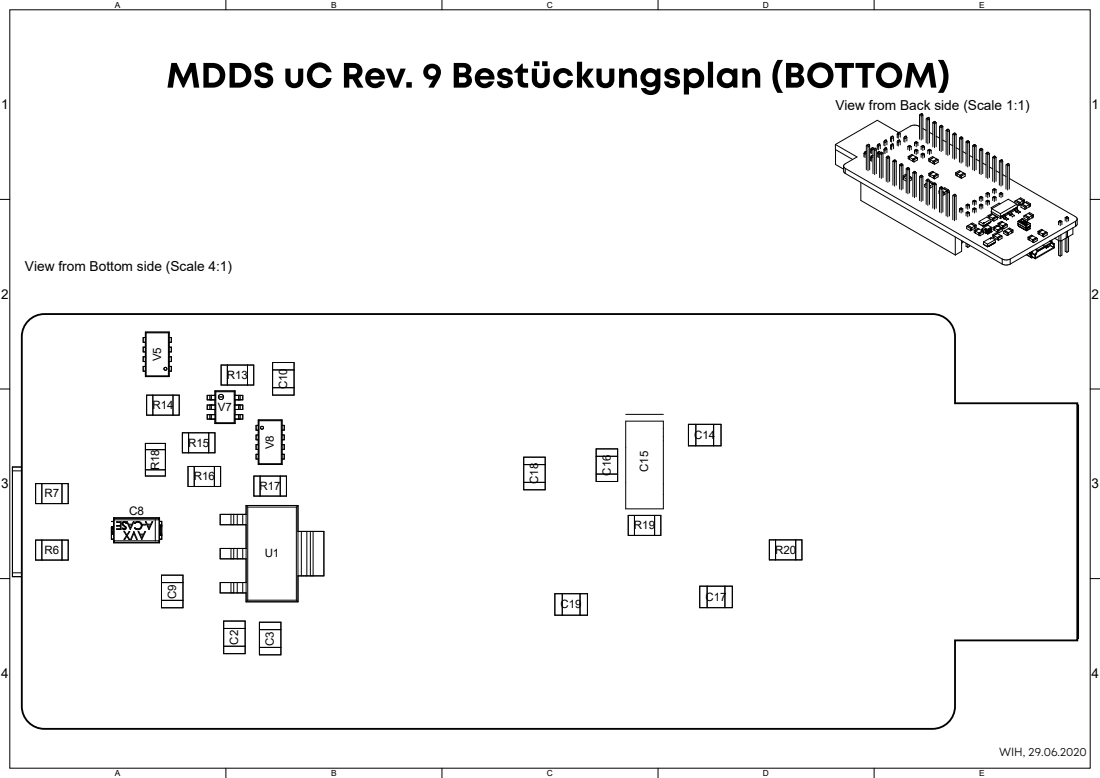
[picture p105: page 2]

View from Back side (Scale 1:1)

View from Bottom side (Scale 4:1)

1 | 1
2 | 2
3 | 3
4 | 4
Line # | Designator | Comment | Quantity | Footprint
1 | C2, C3, C20, C21 | 18p | 4 | CAPC0805(2012)75_M
2 | C8, C15 | 10u | 2 | 1206_Tantal, 1411_Cap_Pol
3 | C9, C10, C14, C16, C17, C18, C19 | 100n | 7 | CAPC0805(2012)75_M
4 | C11, C12 | 10p | 2 | CAPC0805(2012)75_M
5 | D1 | DAPLink Module | 1 | DAPLink Module
6 | D2 | STM32F103RBT6 | 1 | STM32F103RBT6_WIH
7 | L1 | ferrite bead | 1 | RESC0805(2012)_N
8 | R6, R7 | 33R | 2 | RESC0805(2012)_N
9 | R10, R11 | 24k | 2 | RESC0805(2012)_N
10 | R12 | 2.7k | 1 | RESC0805(2012)_N
11 | R13, R16 | 12k 1% | 2 | RESC0805(2012)_N
12 | R14, R17, R18 | 100k 1% | 3 | RESC0805(2012)_N
13 | R15 | 330R 1% | 1 | RESC0805(2012)_N
14 | R19, R20 | 1k | 2 | RESC0805(2012)_N
15 | R21 | 100k | 1 | RESC0805(2012)_N
16 | S1 | 434153017835 | 1 | 434153017835
17 | U1 | TLV1117LV33DCYR | 1 | DCY0004A_N
18 | V5, V8 | TT8J11 | 2 | SOTFL65P190X85-8N
19 | V6 | Green LED | 1 | LED_0805_GREEN
20 | V7 | AO7800 | 1 | SOT363_
21 | X1 | ISP | 1 | HDR1X2
22 | X2 | 61300621121 | 1 | 61300621121
23 | X3, X4 | 14 Pins | 2 | SSQ-114-03-G-S
24 | X5 | GND Test Point | 1 | 61300211121
25 | X6 | 613012243121 | 1 | 613012243121
26 | X7 | micro-USB | 1 | 629105150521
27 | X10 | 61301221121 | 1 | 61301221121
28 | Y2 | 32,768kHz | 1 | ABS07-32.768KHZ-T
29 | Y3 | 8MHz | 1 | ABRA-ABM3B-4_V

Bill Of Materials
