SmichaelSmolley/Diplom_Arbeit/Dokumentation/Rechnungen/referenzen und opv.pdf

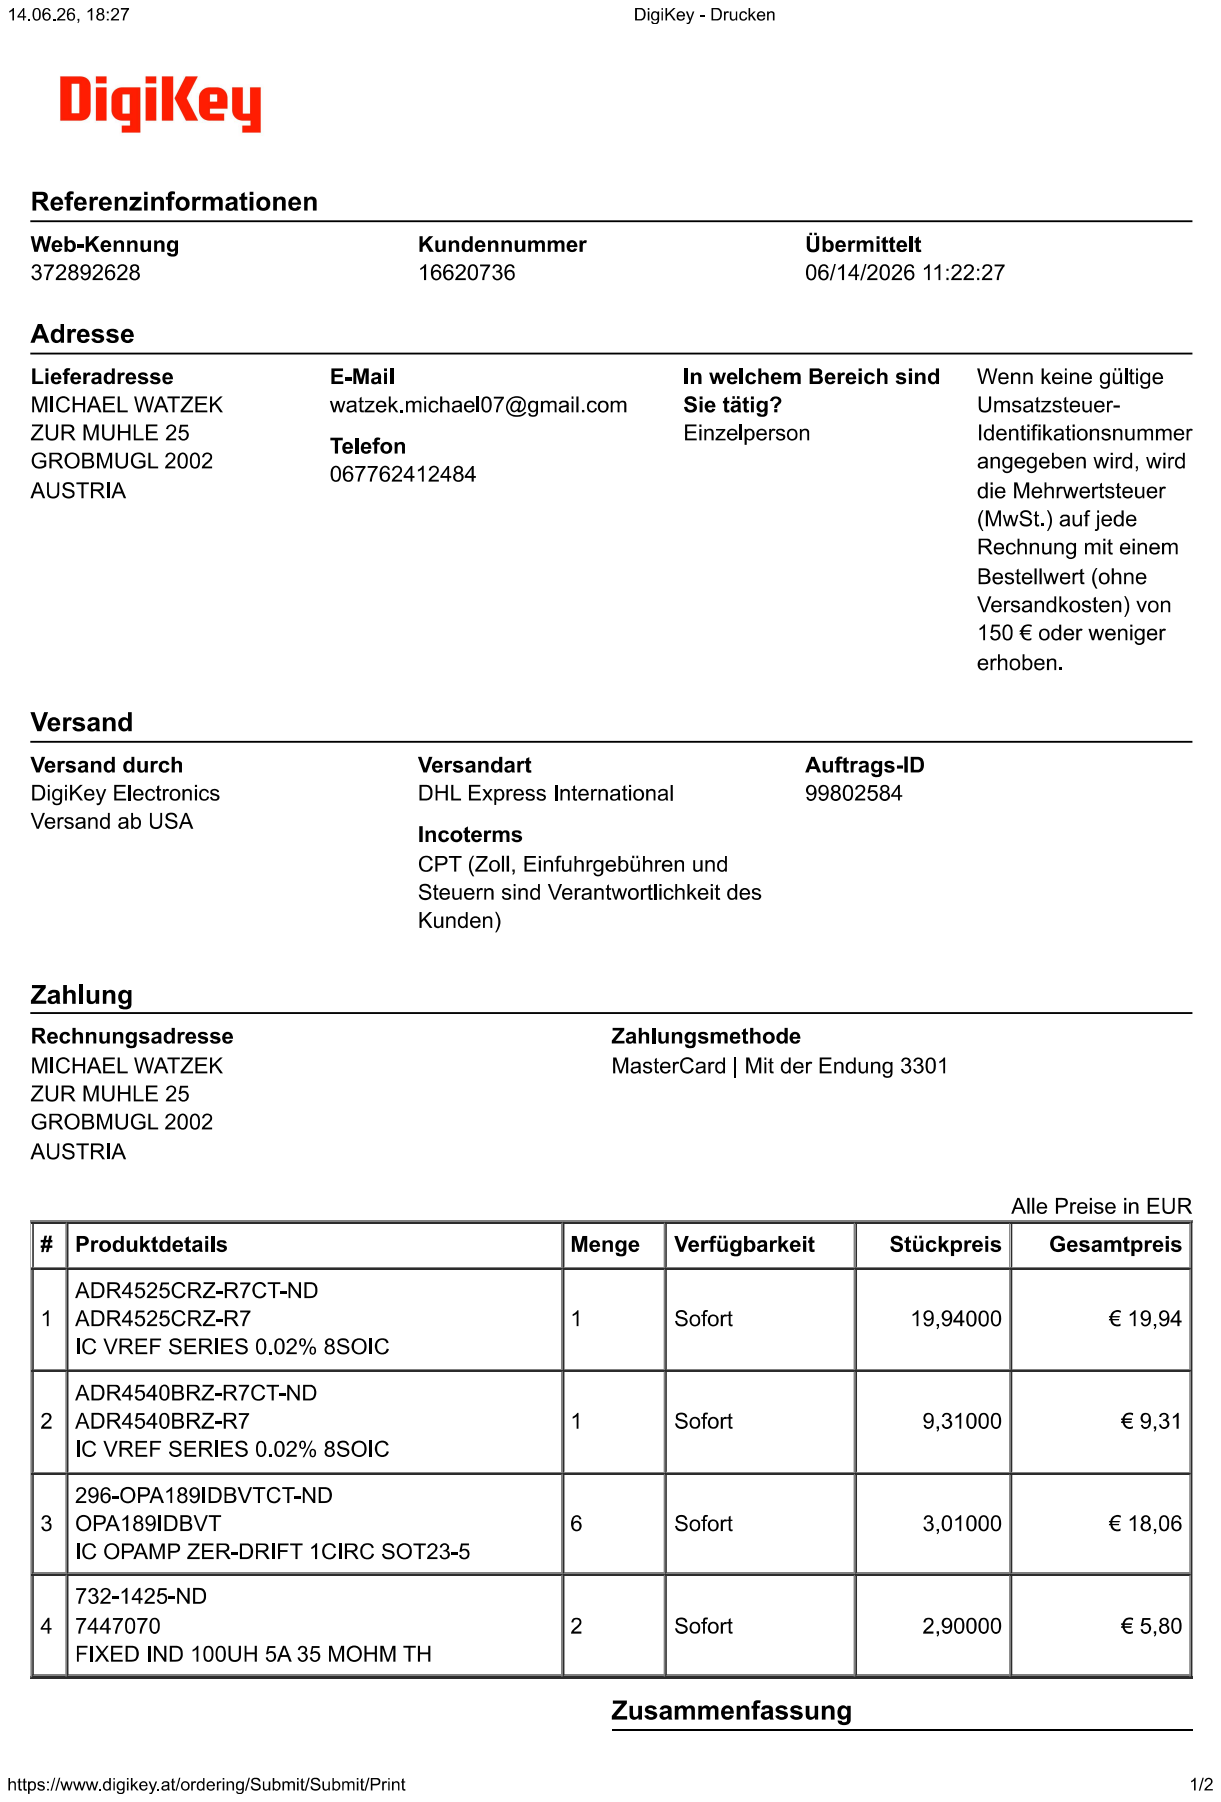
[picture p107: page 1]

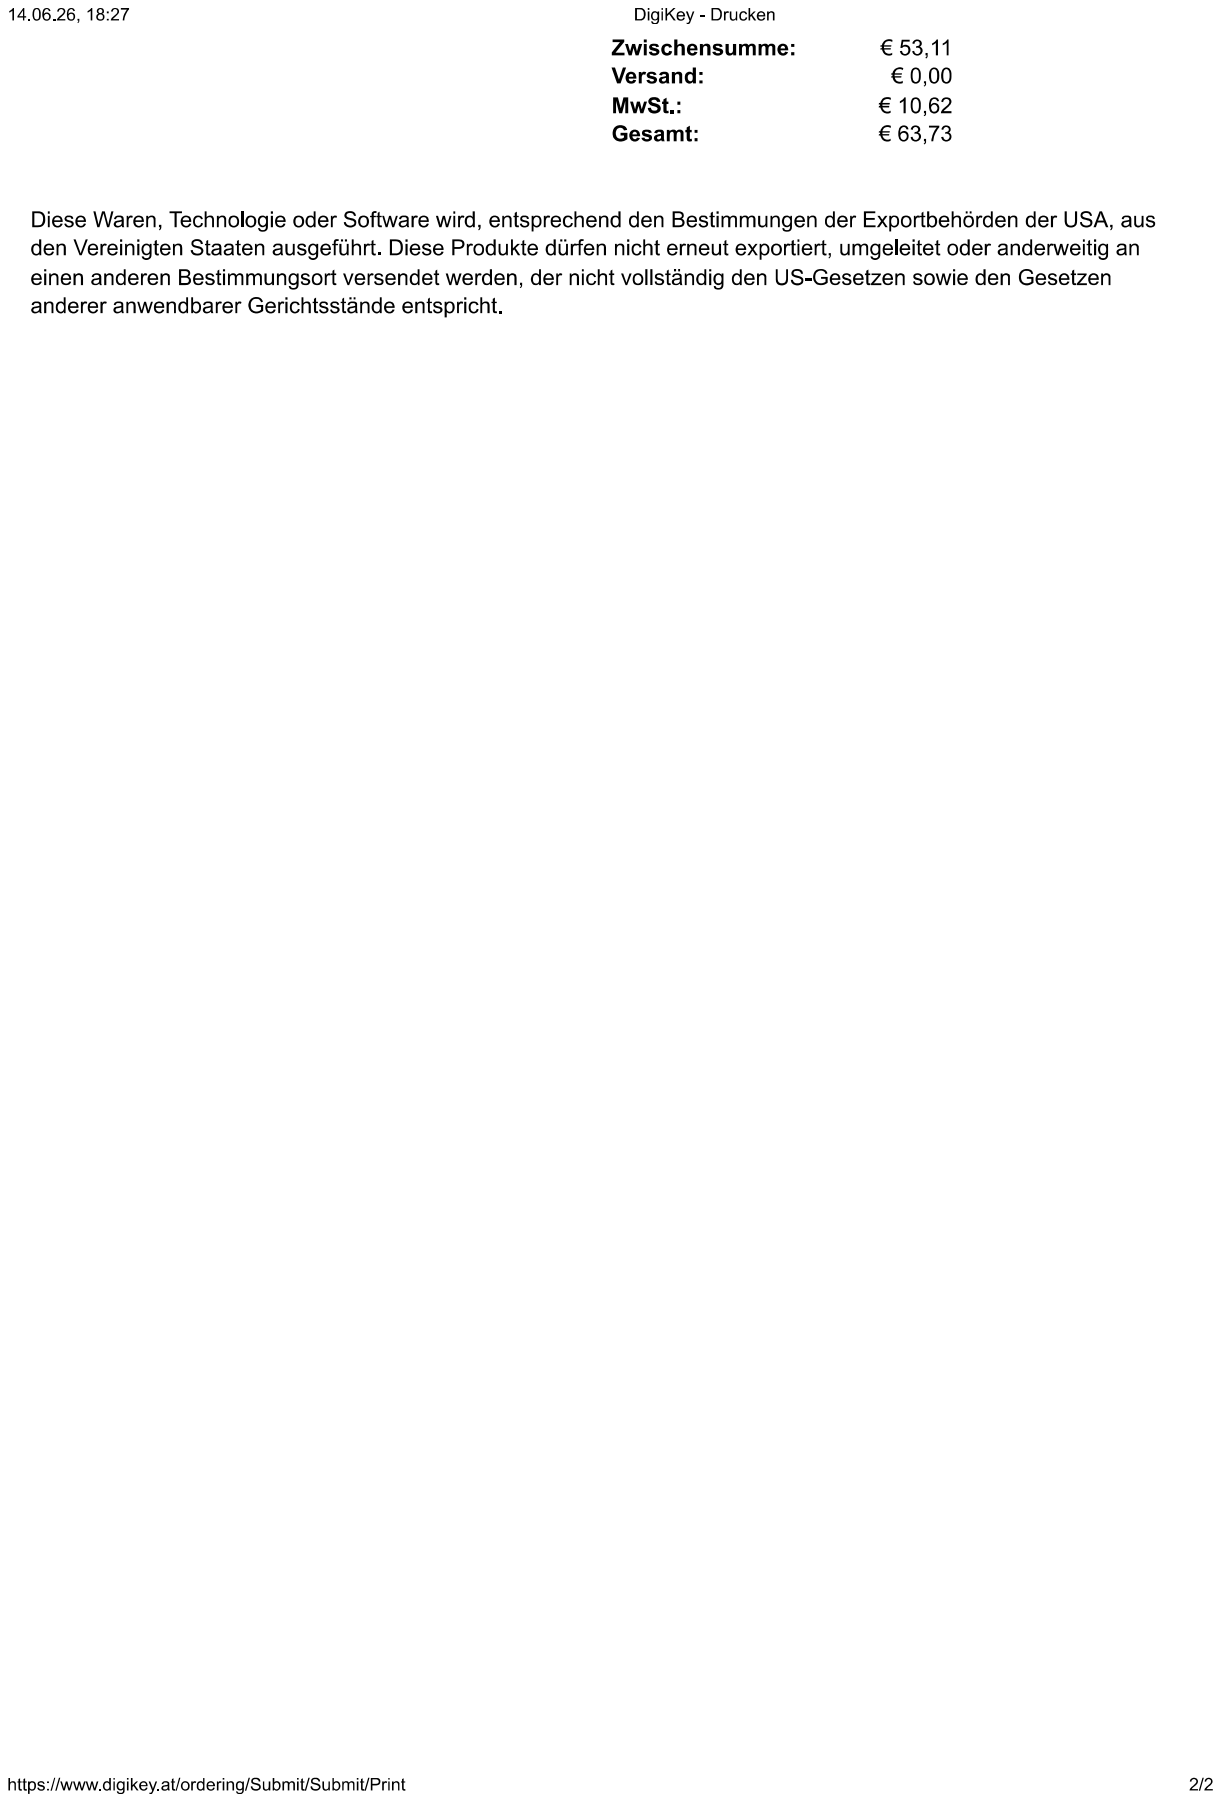
[picture p108: page 2]
