SmichaelSmolley/Diplom_Arbeit/Dokumentation/Simulationen/sim_idvg.pdf

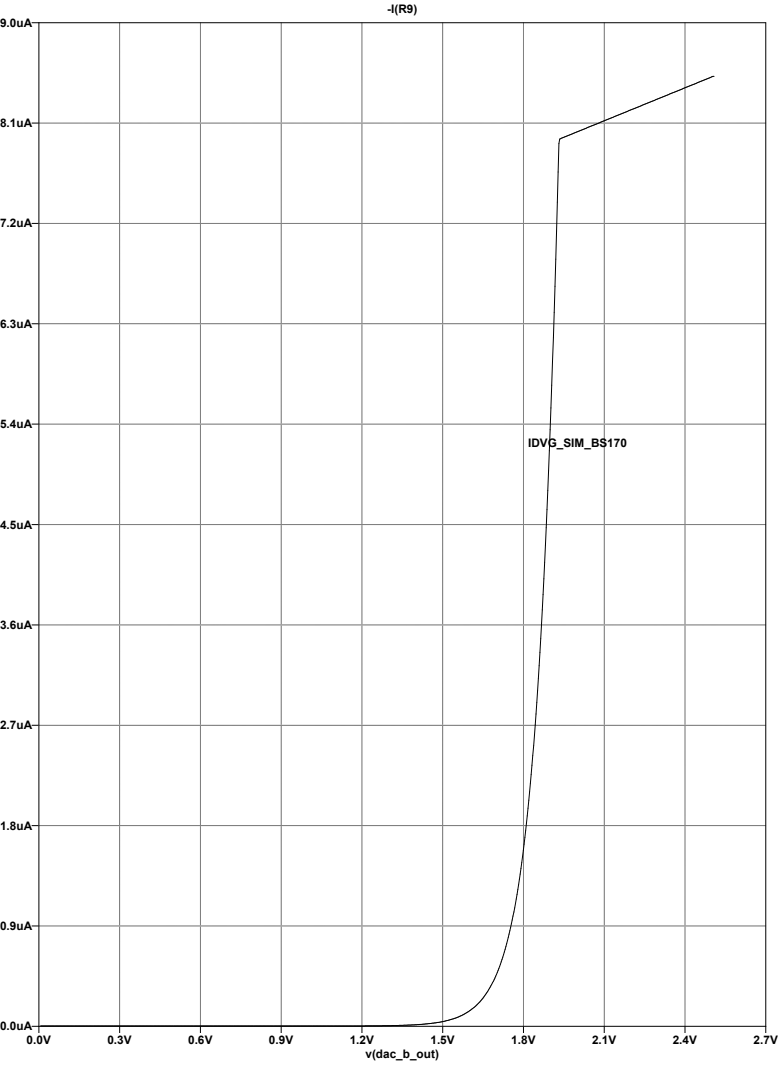
[picture p109: page 1]
v(dac_b_out); IDVG_SIM_BS170

--- C:\Users\Michael Watzek\Documents\Draft1.raw ---
