SmichaelSmolley/Diplom_Arbeit/Software/firmware/Unterlagen_ELLFI/1 Klasse EL/Bestückung_Bot.pdf

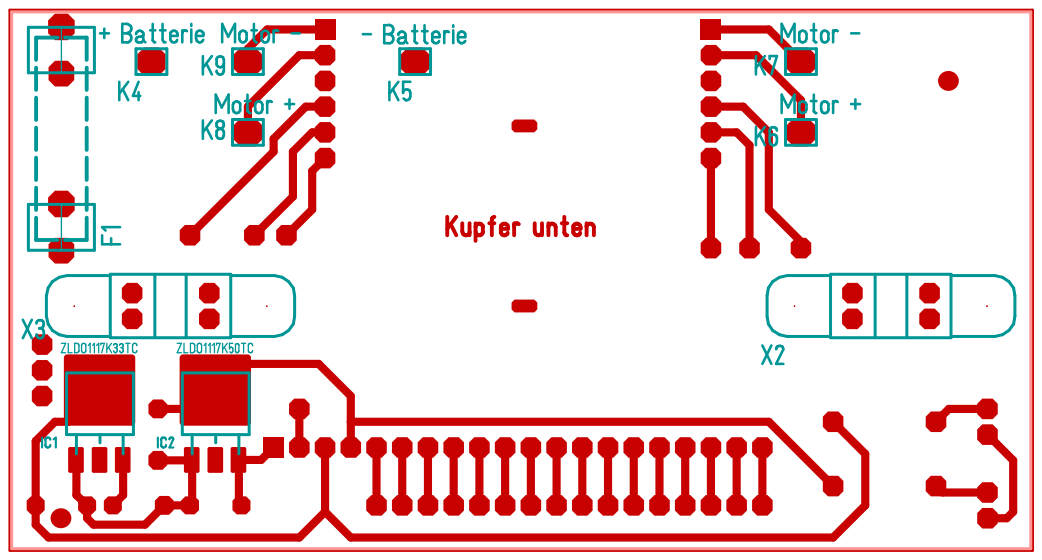
[picture p110: page 1]
