SmichaelSmolley/Diplom_Arbeit/Software/firmware/Unterlagen_ELLFI/1 Klasse EL/Bestückung_Top.pdf

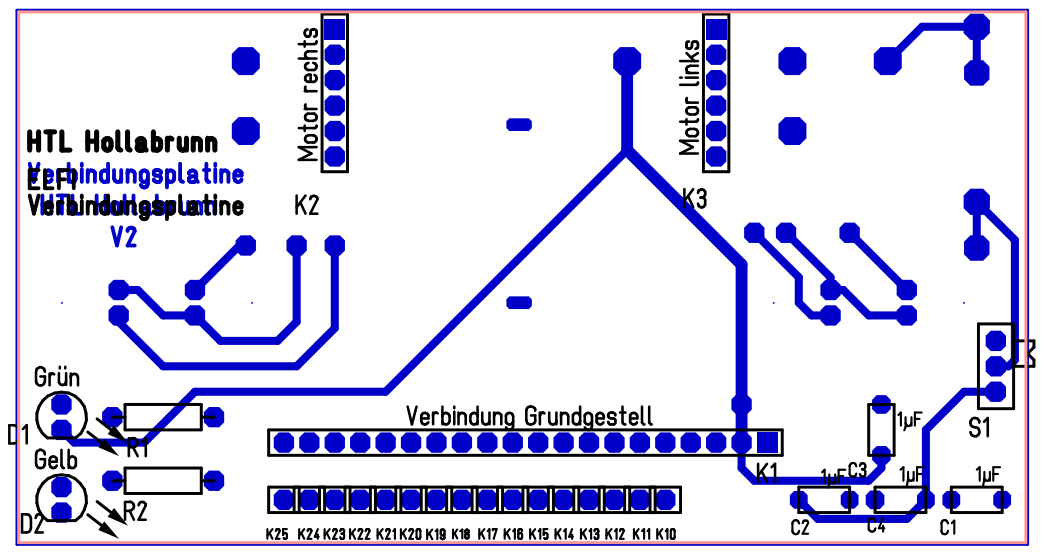
[picture p111: page 1]
