SmichaelSmolley/Diplom_Arbeit/Software/firmware/Unterlagen_ELLFI/1 Klasse EL/Verbindungsplatine_Schaltplan.pdf

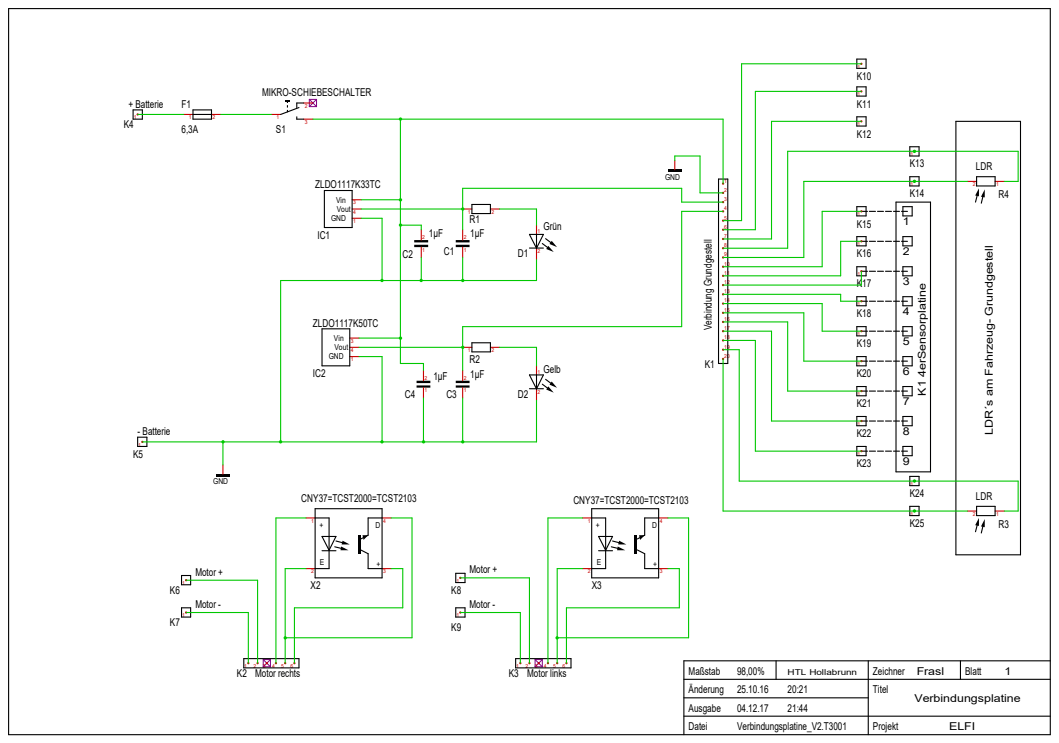
[picture p112: page 1]

Maßstab 98,00% | HTL Hollabrunn | Zeichner Frasl | Blatt 1
Änderung 25.10.16 20:21 | | Titel Verbindungsplatine
