SmichaelSmolley/Diplom_Arbeit/Software/firmware/Unterlagen_ELLFI/2 Klasse EL/4erSensorplatine_Bestückung.pdf

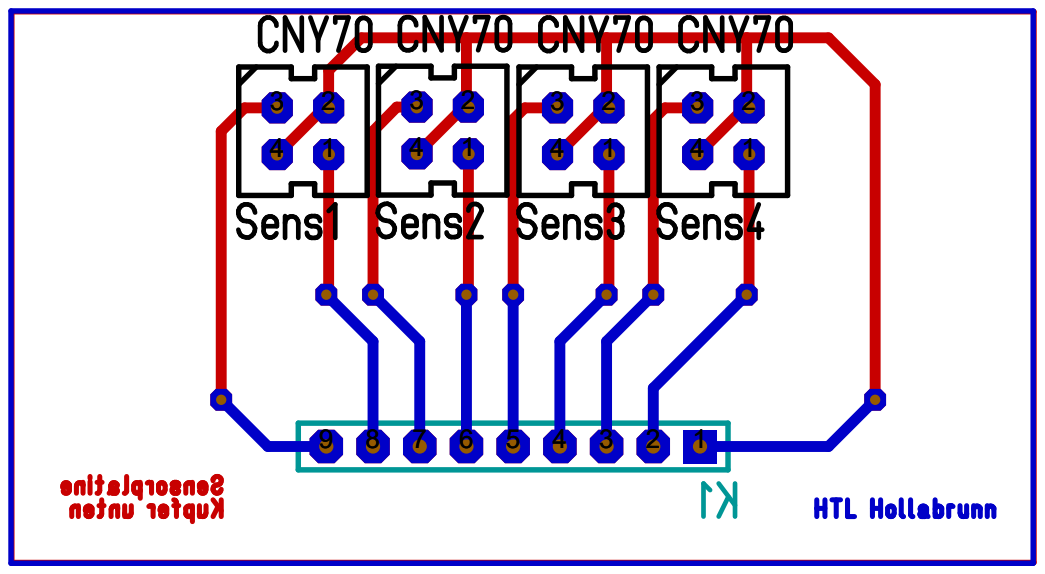
[picture p113: page 1]
