SmichaelSmolley/Diplom_Arbeit/Software/firmware/Unterlagen_ELLFI/2 Klasse EL/Hauptplatine_Bestückung.pdf

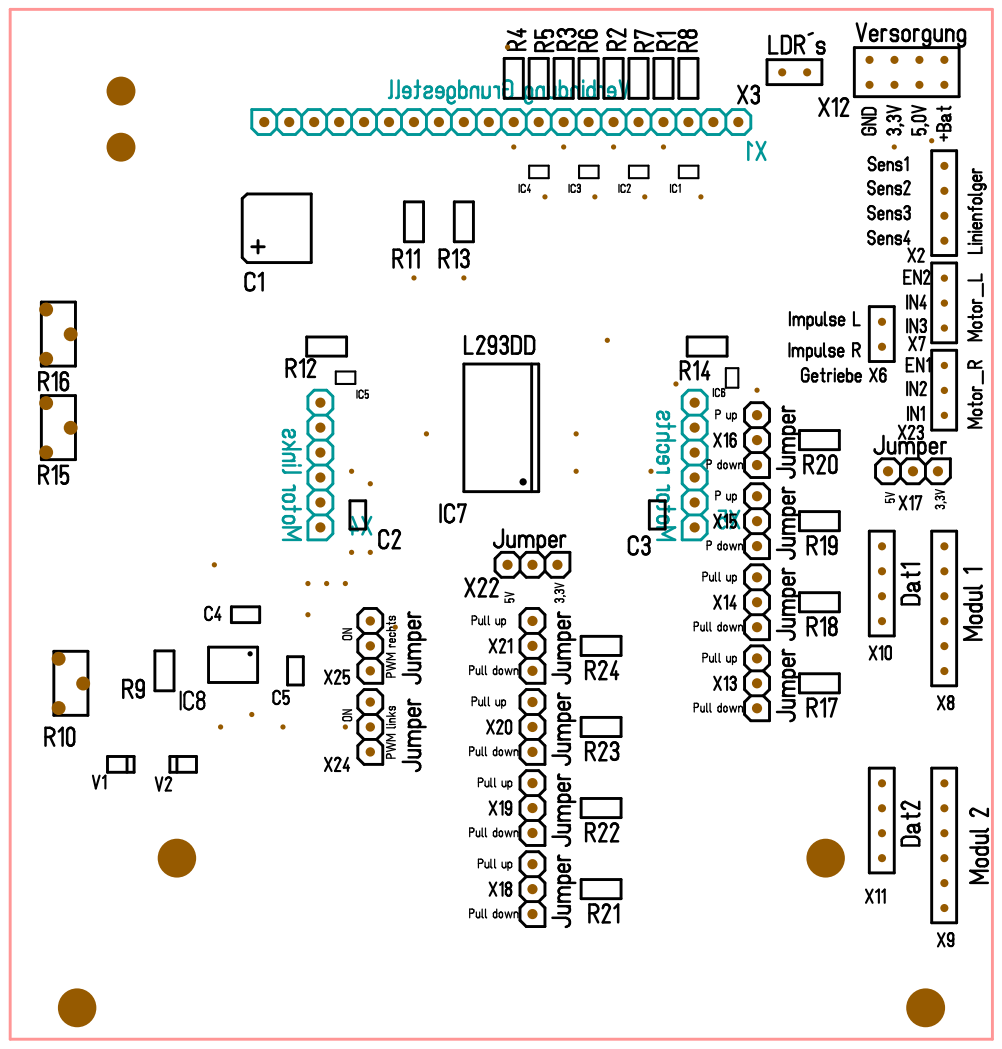
[picture p114: page 1]
