SmichaelSmolley/Diplom_Arbeit/Software/firmware/Unterlagen_ELLFI/2 Klasse EL/Hauptplatine_Schaltplan.pdf

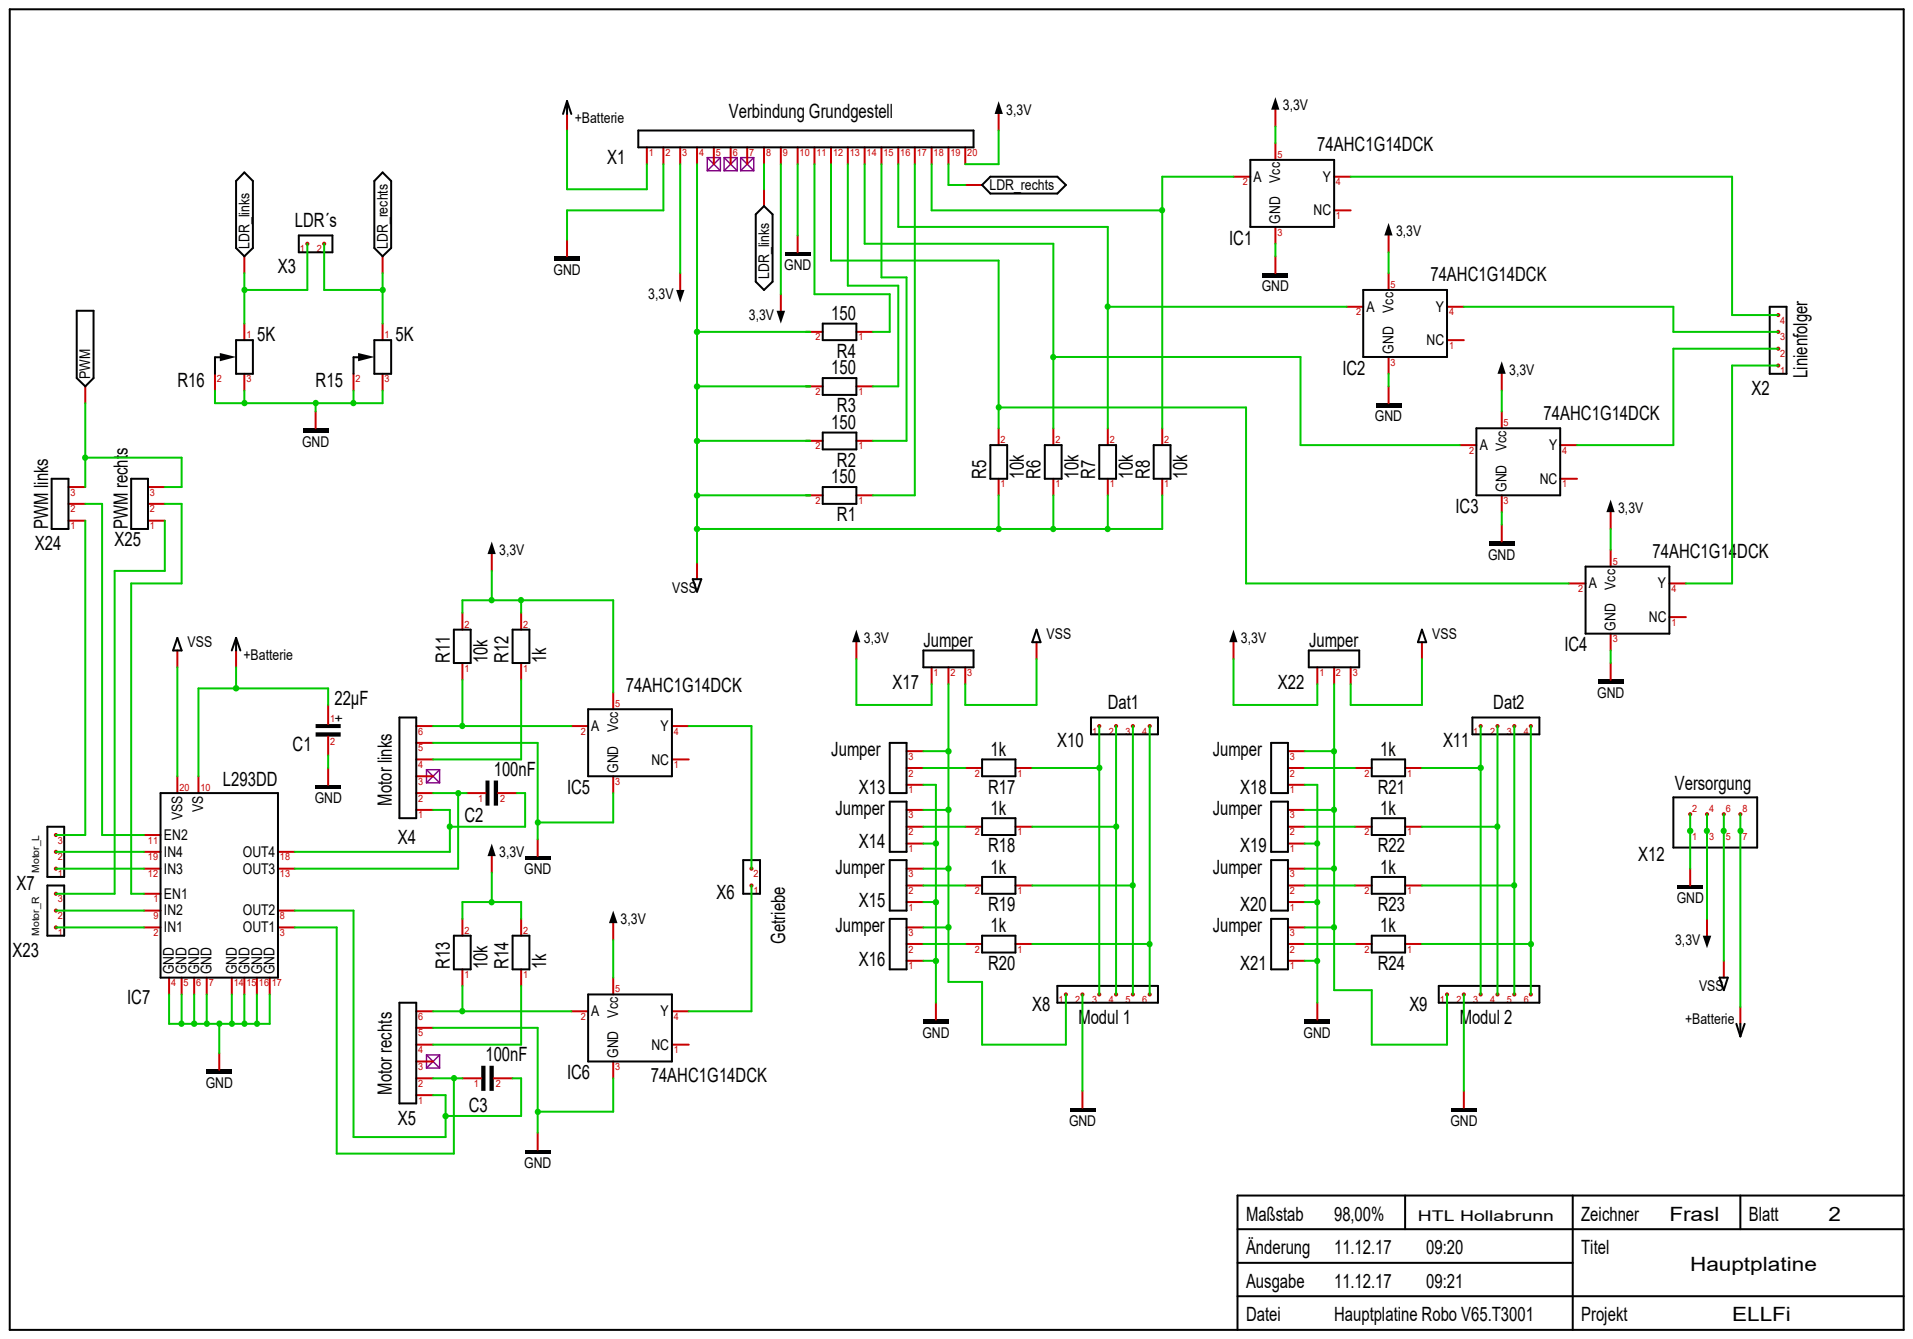
[picture p115: page 1]

Maßstab 98,00% | HTL Hollabrunn | Zeichner Frasl | Blatt 2
Änderung 11.12.17 09:20 | | Titel Hauptplatine
