SmichaelSmolley/Diplom_Arbeit/Software/firmware/MDDS_Unterlagen_neu/MDDS_DAPLink_Module/Rev02/MDDS_DAPLink_Module_Rev02_Schaltplan.pdf

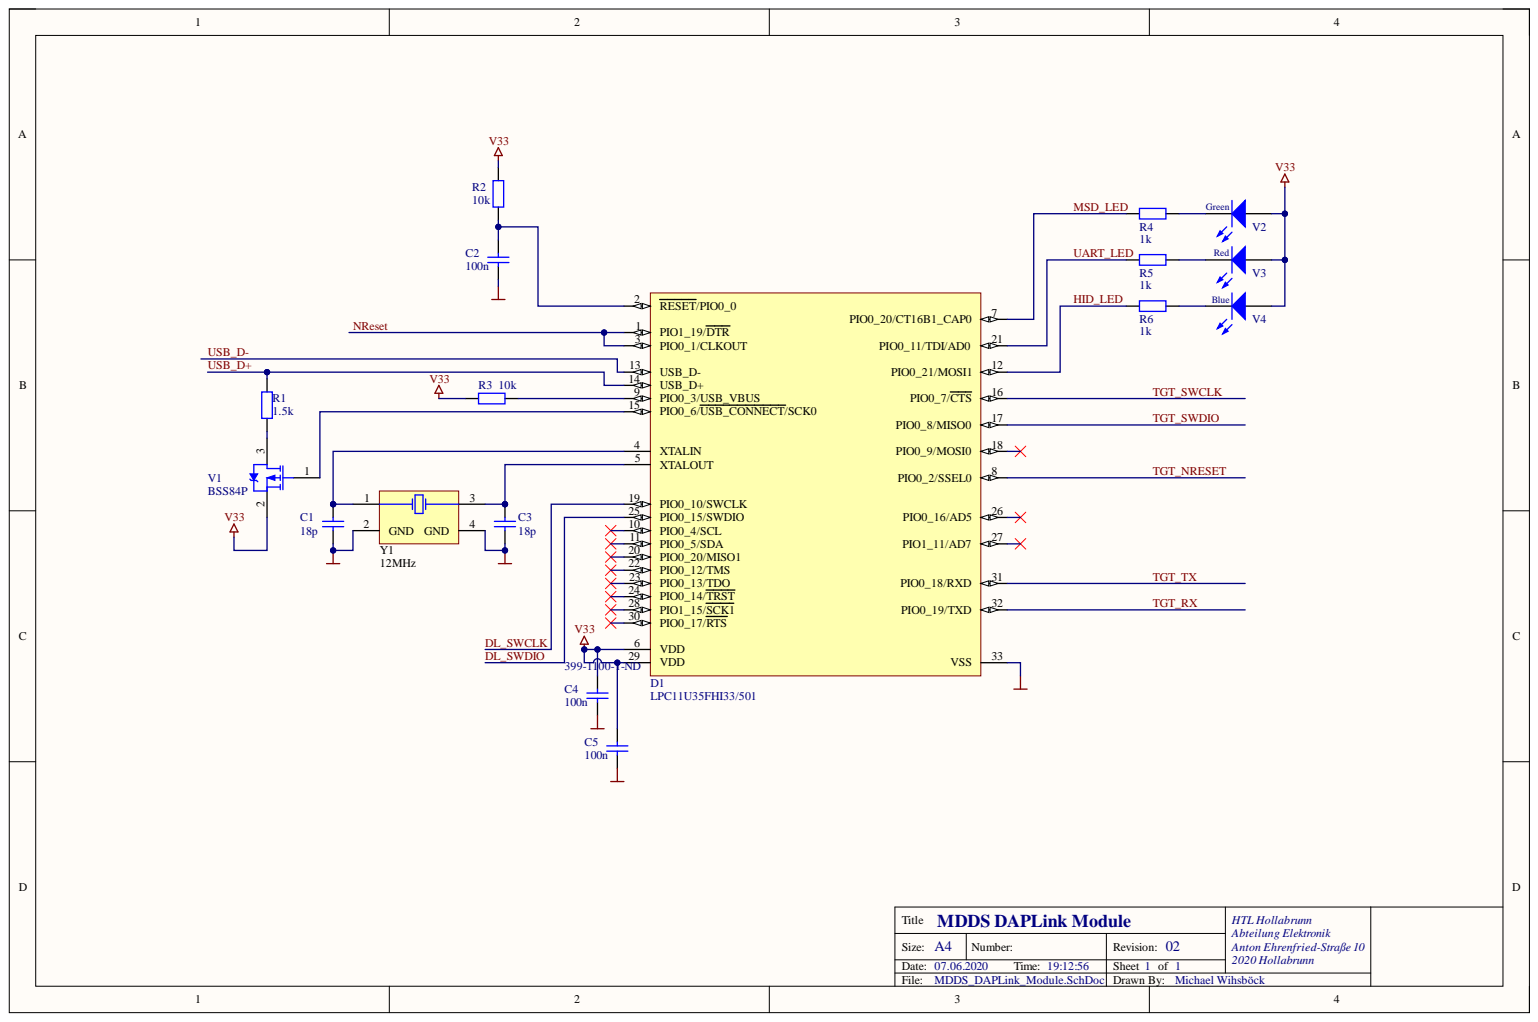
[picture p116: page 1]

C3 18p V 3 3 L_SWCL K | 1 0 1 1 2 2 2 2 3 2 4 2 8 3 0 6

Size: A 4 | N u mber: | Rev i s i o n : 0 2
Date: 0 7.0 6 . 2 0 2 0 Ti me: 1 9 : 1 2 : 5 6 | | Shee t 1 o f 1
