SmichaelSmolley/Diplom_Arbeit/Software/firmware/MDDS_Unterlagen_neu/MDDS_uC/Rev09/MDDS_uC_Rev09_Schaltplan.pdf

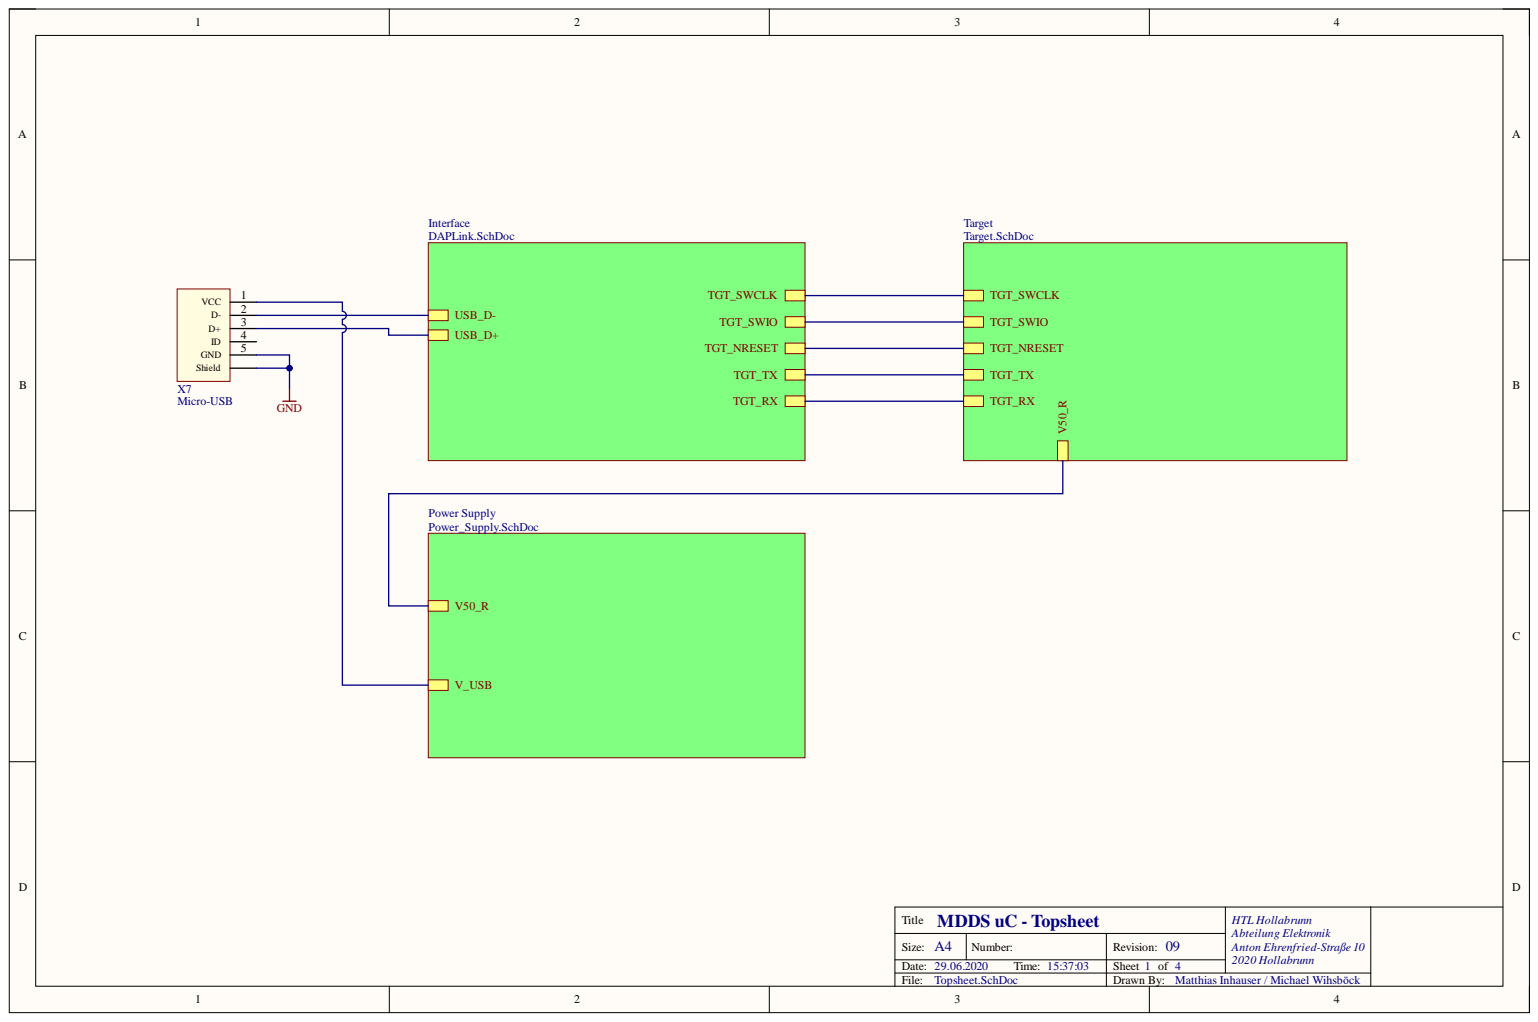
[picture p117: page 1]

Size: A4 | Number: | Revision: 09
Date: 29.06.2020 Time: 15:37:03 | | Sheet of | 2020 Hollabrunn 4

Drawn By: Matthias Inhauser / Michael Wihsböck

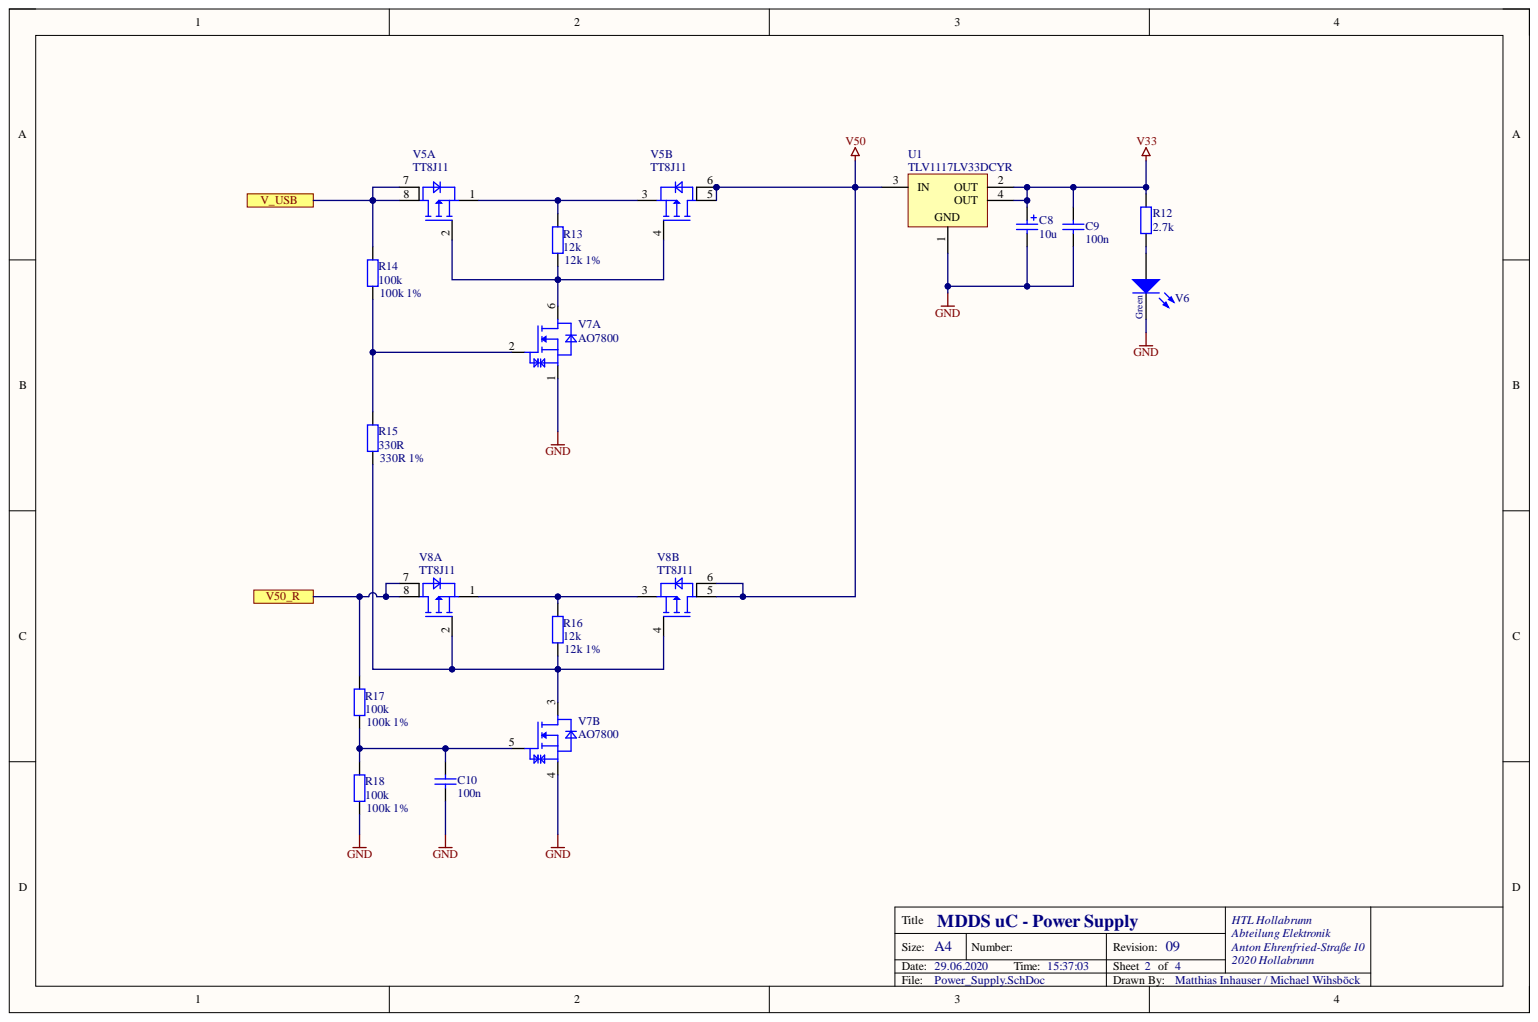
[picture p118: page 2]

Size: A 4 | N u mber: | Rev i s i o n : 0 9

9.0 . Ti me: : : | | Shee t o f

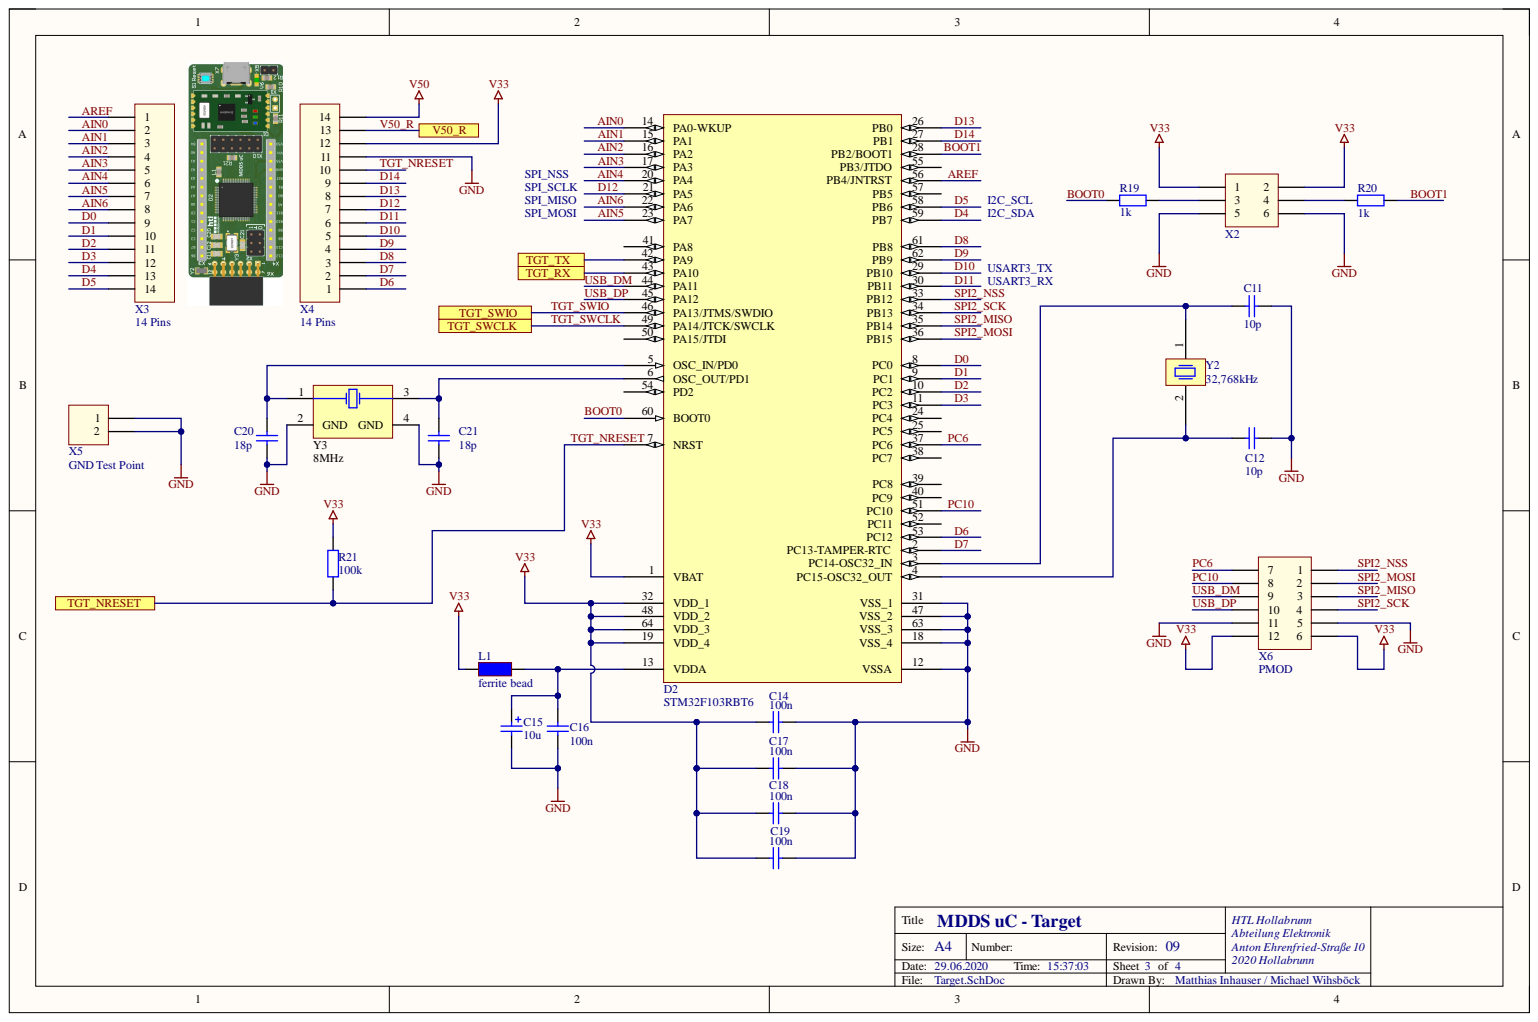
[picture p119: page 3]

Size: A4 | Number: | Revision: 09
29.06.2020 Time: 15:37:03 | | Sheet of | 2020 Hollabrunn 4

Drawn By: Matthias Inhauser / Michael Wihsböck

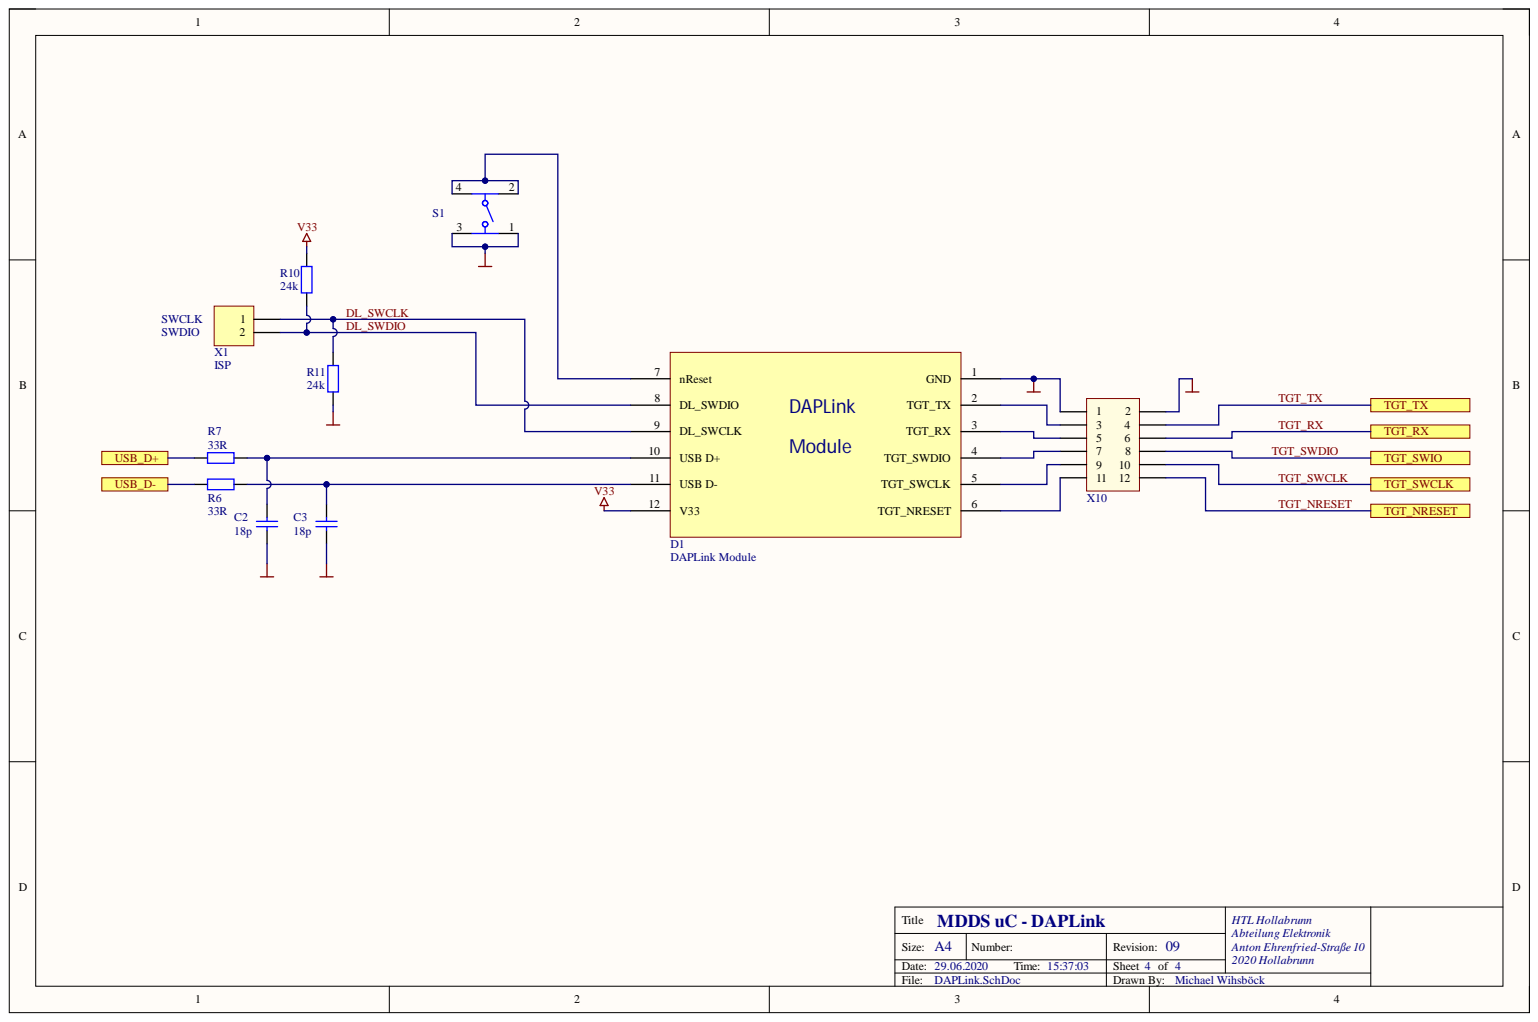
[picture p120: page 4]

T G T_SWCL K

Size: A 4 | N u mber: | Rev i s i o n : 0 9

9.0 . Ti me: : : | | Shee t o f
