SmichaelSmolley/Diplom_Arbeit/Software/firmware/MDDS_Unterlagen_neu/PMOD_Analog/Rev02/PMOD_Analog_Rev02_Schaltplan.pdf

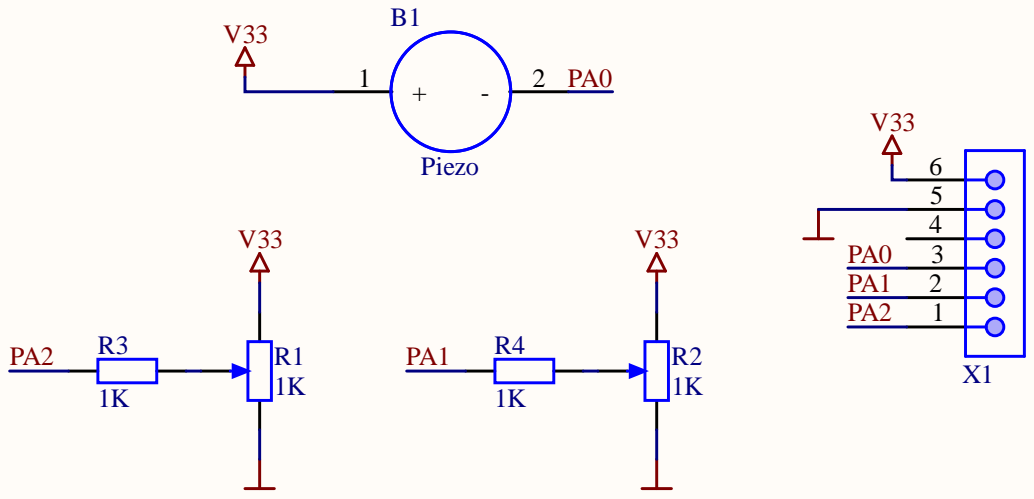
[picture p121: page 1]

Size: Size: A4 A4 | Number: Number: 05/2022 05/2022 | Revision: Revision: 02 02
Date: Date: 04.01.2023 04.01.2023 Time: Time: 17:04:02 17:04:02 | | Sheet Sheet 1 1 of of | 2020 Hollabrunn 1

Drawn By: Florian Kralitschek
