SmichaelSmolley/Diplom_Arbeit/Software/firmware/MDDS_Unterlagen_neu/PMOD_LEDs/Rev03/PMOD_LEDs_Rev03_Schaltplan.pdf

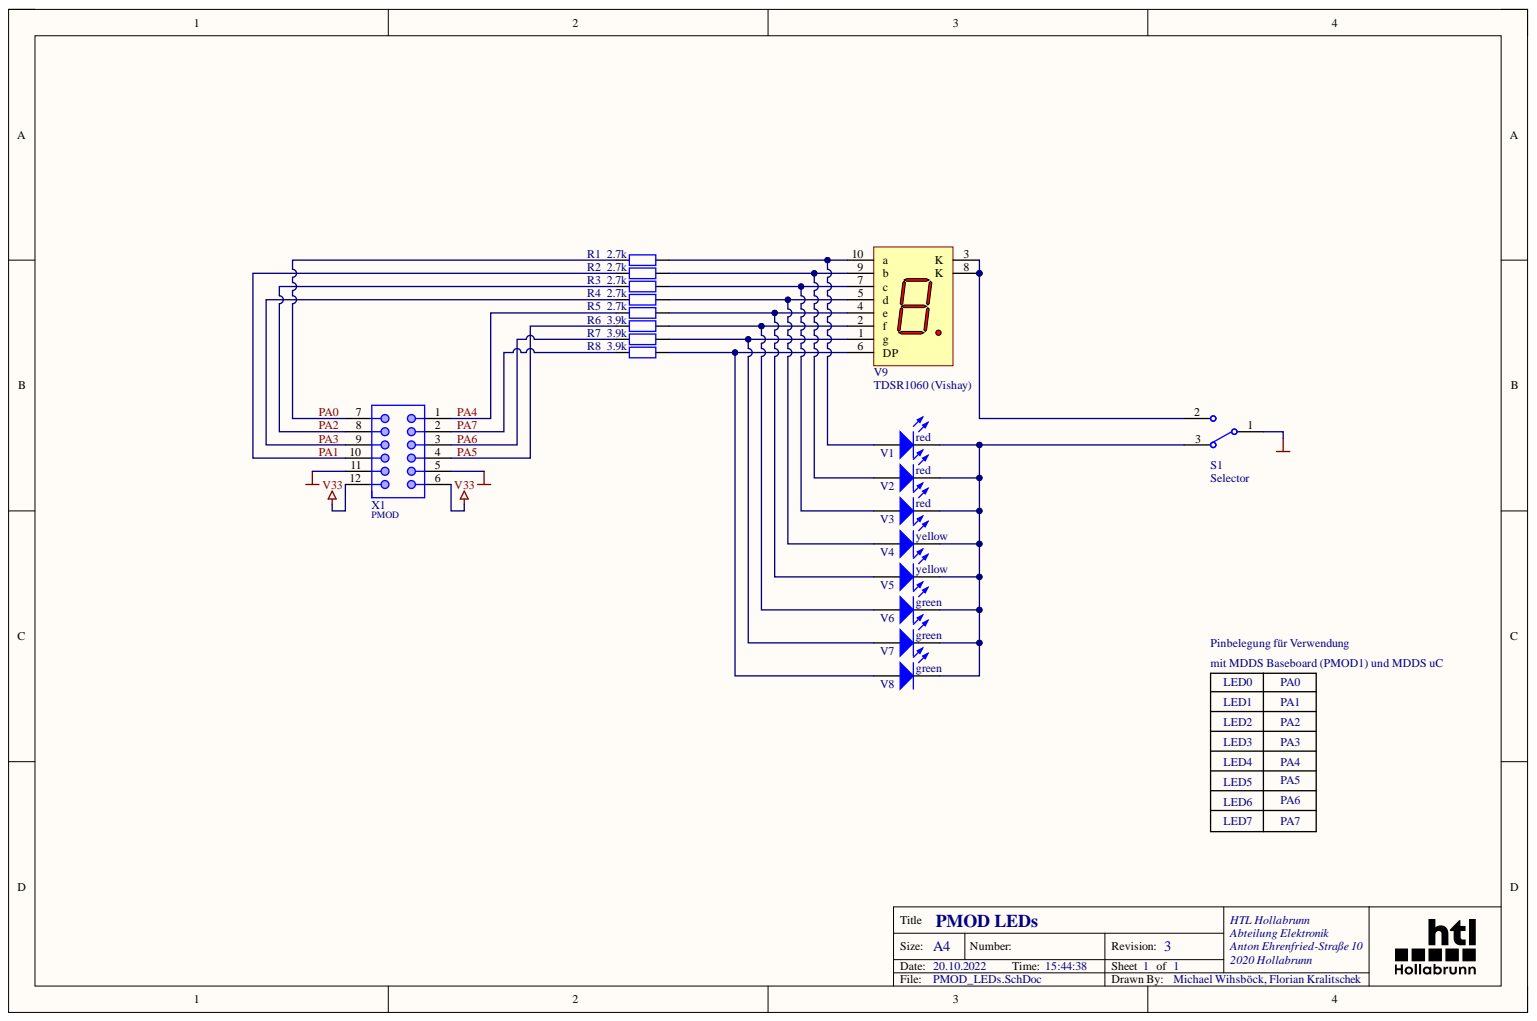
[picture p122: page 1]

R2 2 . | 7 k | | 9 | 8
R3 2 . | 7 k | | 7
R4 2 . | 7 k | | 5
R5 2 . | 7 k | | 4
R6 3 . | 9 k | | 2
R7 3 . | | | 1

L E D 0 | PA 0
L E D 1 | PA 1
L E D 2 | PA 2
L E D 3 | PA 3
L E D 4 | PA 4
L E D 5 | PA 5
L E D 6 | PA 6

Size : A 4 | N umb er : | Rev i s i o n : 3
Dat e : 2 0.1 0 . 2 0 2 2 T ime : 1 5 : 4 4 : 3 8 | | Shee t 1 o f 1
