SmichaelSmolley/Diplom_Arbeit/Software/firmware/MDDS_Unterlagen_neu/PMOD_Switches/Rev03/PMOD_Switches_Rev03_Schaltplan.pdf

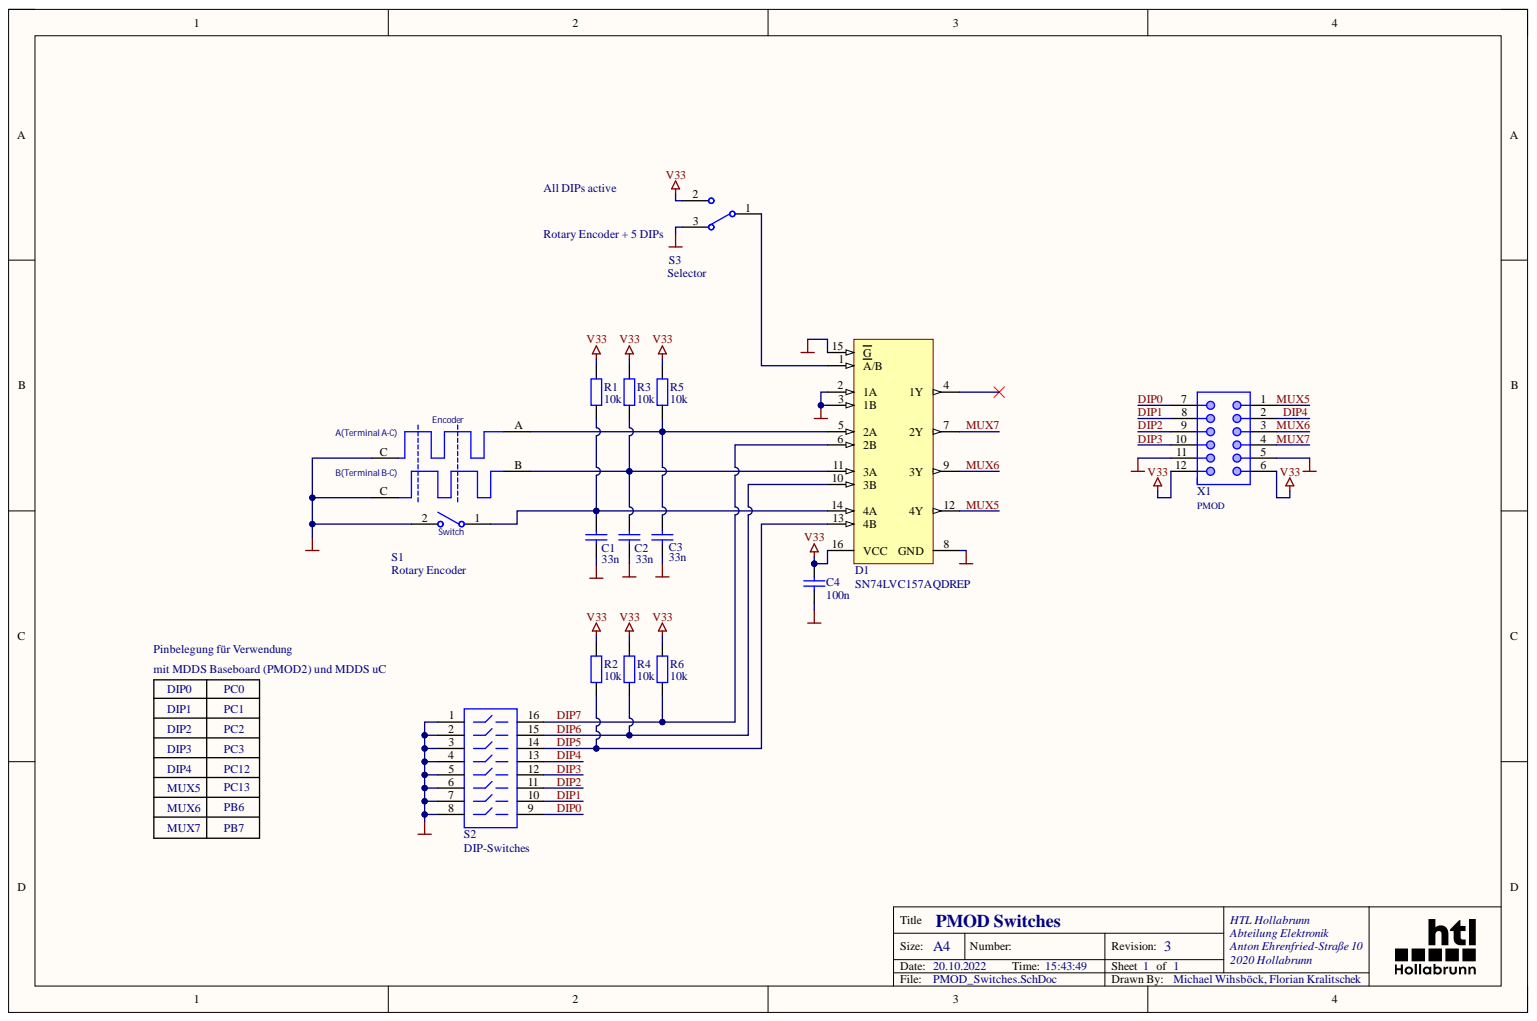
[picture p123: page 1]

V33 | VCC 16

Pinbelegung für Verwendung
mit MDDS Baseboard (PMOD2) und MDDS uC

DIP0 | PC0
DIP1 | PC1

MUX6 | PB6

MUX7 | PB7

Size: A4 | Number: | Revision: 3
Date: 20.10.2022 Time: 15:43:49 | | Sheet 1 of | 2020 Hollabrunn 1

Drawn By: Michael Wihsböck, Florian Kralitschek
