SmichaelSmolley/Diplom_Arbeit/Software/firmware/MDDS_Unterlagen_neu/PMOD_UART_USB/Rev01/PMOD_UART_USB_Rev01_Schaltplan.pdf

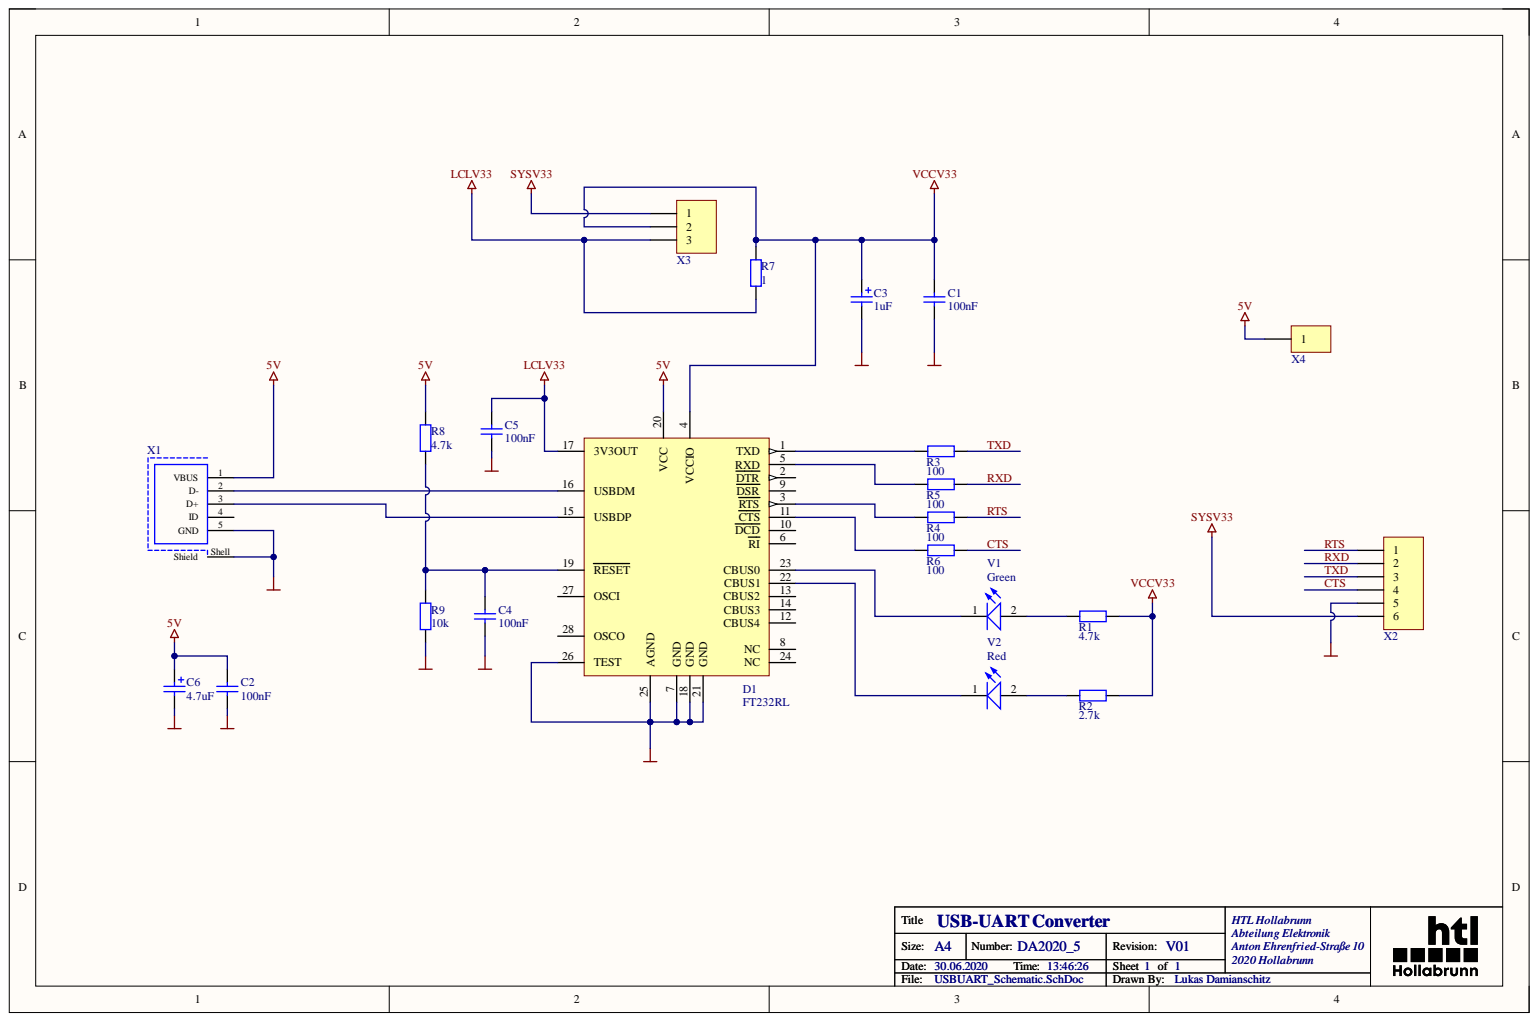
[picture p124: page 1]

Size: Size: A A 4 4 | N N u u mber: mber: DA DA 2 2 0 0 2 2 0 0 _ _ 5 5 | Rev Rev i i s s i i o o n n : : V V 0 0 1 1
Date: Date: 3 3 0.0 0.0 6 6 . . 2 2 0 0 2 2 0 0 Ti Ti me: me: 1 1 3 3 : : 4 4 6 6 : : 2 2 6 6 | | Shee Shee t t 1 1 o o f f 1 1
