SmichaelSmolley/Diplom_Arbeit/Software/firmware/MDDS_Unterlagen_neu/PMOD_UART_USB/Rev01/Fertigungsdokumente/PMOD_UART_USB_Rev01_Bestueckungsplan.pdf

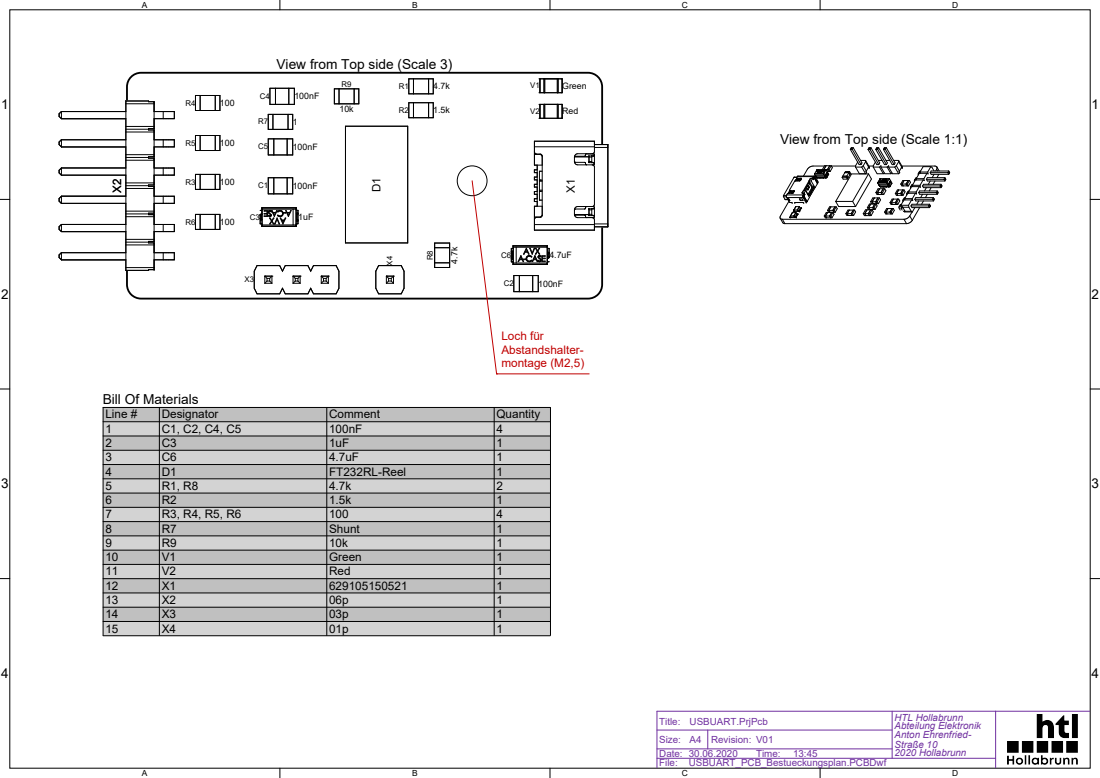
[picture p125: page 1]

View from Top side (Scale 3)

View from Top side (Scale 1:1)
