SmichaelSmolley/Diplom_Arbeit/Software/firmware/MDDS_Unterlagen_neu/PMOD_LEDs/Rev02/PMOD_LEDs_Rev02_Schaltplan.pdf

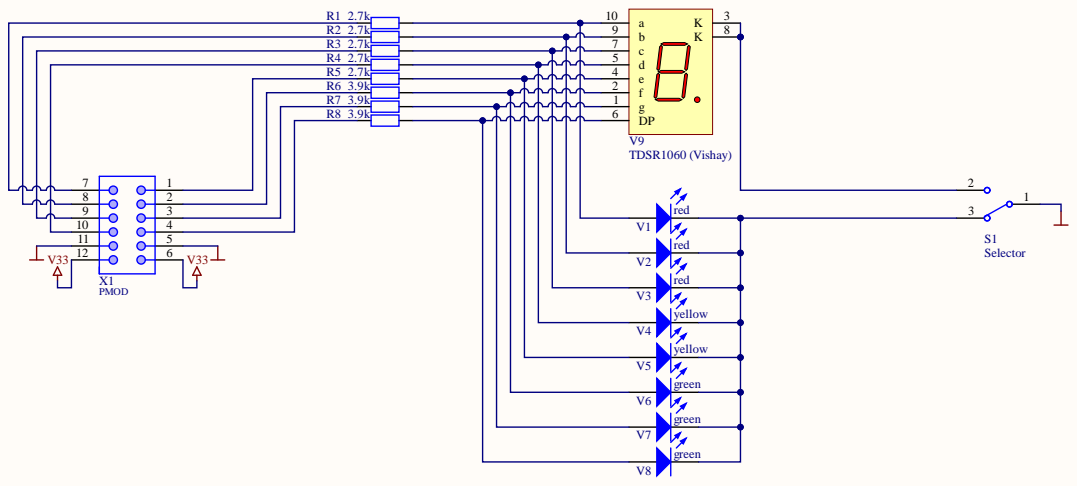
[picture p126: page 1]

R2 2.7 | k | 9 | | 8
R3 2.7 | k | | 7
R4 2.7 | k | | | 5
R5 2.7 | k | | | | 4
R6 3.9 | k | | | | | 2
R7 3.9 | k | | | | | | 1
R8 3.9 | k | | | | | | | 6

1 0 | 4

Size: A 4 | N u mber: | Rev i s i o n : 2
Date: 0 6.0 9 . 2 0 2 0 Ti me: 1 6 : 0 2 : 3 7 | | Shee t 1 o f 1
