SmichaelSmolley/Diplom_Arbeit/Software/firmware/MDDS_Unterlagen_neu/PMOD_Switches/Rev02/PMOD_Switches_Rev02_Schaltplan.pdf

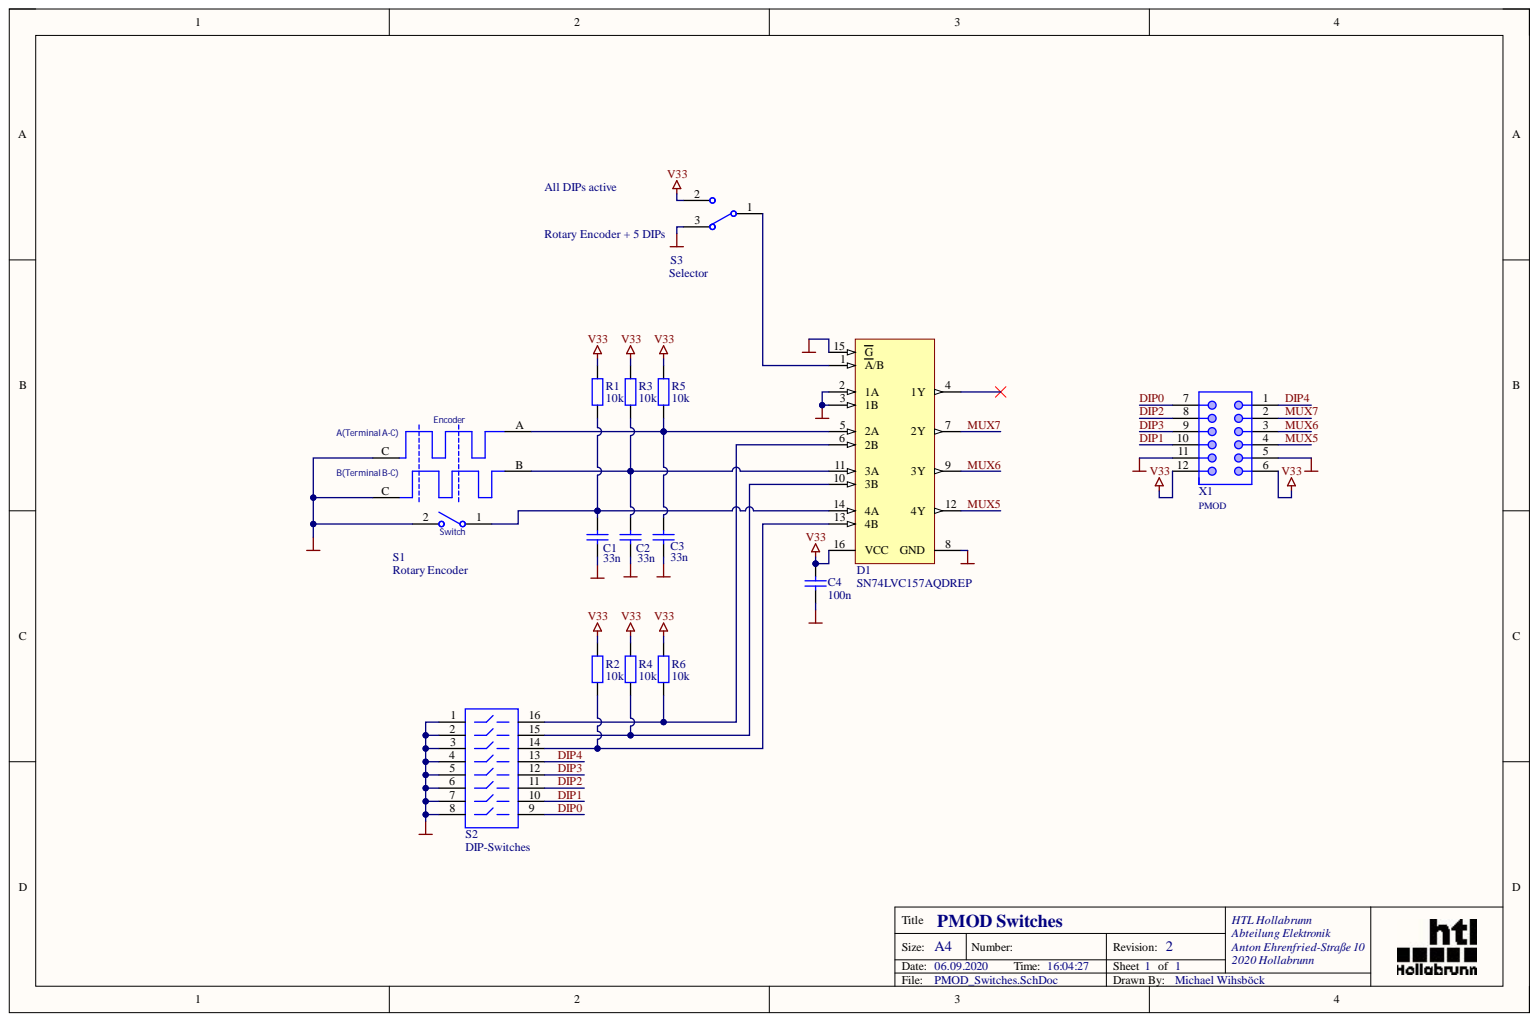
[picture p127: page 1]

V33 | VCC 16

2 | 15
3 | 14

Size: A4 | Number: | Revision: 2
Date: 06.09.2020 Time: 16:04:27 | | Sheet 1 of | 2020 Hollabrunn 1

Drawn By: Michael Wihsböck
