SmichaelSmolley/Diplom_Arbeit/Hardware/noise sim/main.asc

C1: cap; {x1}
R2: res; {x2}
V1: voltage; +8V
V2: voltage; -8V
V3: voltage; 1V
Named nets: 0, -ub, +ub, out, in
.noise V(out) V3 dec 1000 0.1 10Meg
.step param x1 list 1p 6p 12p 20p
.step param x2 list 10Meg 100k
