SmichaelSmolley/Diplom_Arbeit/Dokumentation/Simulationen/sim_idvg.asc

C1: cap; 10uF
C2: cap; 22pF
M1: nmos; BS170
R1: res; 20k
R2: res; 10k
R3: res; 1k
R4: res; 454
R5: res; 10k
R6: res; 100
R7: res; 10k
R8: res; 30k
R9: res; 10Meg
R10: res; 6.8k
R11: res; 1k
U1: LT6001
U2: LT6001
U3: LT6001
U4: LT6001
V1: voltage; 1.65
V2: voltage; 8
V3: voltage; 8
V4: voltage; 1
Named nets: 0, +ub, -ub, mess_out, dac_b_out, +1V
.dc V1 0 3 0.001
