SmichaelSmolley/Diplom_Arbeit/Software/py/psd.py

import numpy as np
import matplotlib.pyplot as plt

# 3 getrennte Messungen aus den 3 Spalten des Bildes (jeweils N = 105 Punkte)
messung_1 = [
    -2.019, -2.014, -2.006, -1.996, -1.983, -1.967, -1.95, -1.928, -1.905, -1.879,
    -1.851, -1.82, -1.786, -1.75, -1.712, -1.672, -1.629, -1.583, -1.537, -1.488,
    -1.436, -1.384, -1.329, -1.271, -1.214, -1.153, -1.092, -1.029, -0.965, -0.898,
    -0.833, -0.766, -0.698, -0.63, -0.56, -0.491, -0.419, -0.348, -0.277, -0.205,
    -0.134, -0.06, 0.012, 0.083, 0.148, 0.213, 0.28, 0.345, 0.41, 0.476,
    0.54, 0.603, 0.667, 0.729, 0.79, 0.851, 0.911, 0.969, 1.026, 1.083,
    1.139, 1.194, 1.247, 1.298, 1.349, 1.398, 1.444, 1.491, 1.534, 1.575,
    1.616, 1.654, 1.691, 1.726, 1.758, 1.789, 1.817, 1.844, 1.868, 1.889,
    1.909, 1.928, 1.943, 1.956, 1.967, 1.975, 1.981, 1.985, 1.987, 1.987,
    1.983, 1.979, 1.971, 1.961, 1.949, 1.935, 1.918, 1.9, 1.878, 1.856,
    1.83, 1.802, 1.774, 1.742, 1.708
]

messung_2 = [
    1.696, 1.254, 0.665, -0.002, -0.644, -1.257, -1.732, -1.99, -1.983, -1.712,
    -1.214, -0.553, 0.177, 0.87, 1.41, 1.791, 1.976, 1.933, 1.671, 1.214,
    0.617, -0.051, -0.703, -1.318, -1.772, -2.002, -1.966, -1.669, -1.149, -0.478,
    0.255, 0.941, 1.463, 1.824, 1.982, 1.914, 1.629, 1.152, 0.547, -0.123,
    -0.771, -1.377, -1.81, -2.012, -1.945, -1.62, -1.08, -0.397, 0.337, 1.014,
    1.518, 1.86, 1.987, 1.885, 1.567, 1.07, 0.449, -0.223, -0.864, -1.453,
    -1.856, -2.019, -1.914, -1.555, -0.989, -0.292, 0.429, 1.093, 1.577, 1.89,
    1.987, 1.854, 1.511, 0.995, 0.362, -0.299, -0.933, -1.506, -1.885, -2.021,
    -1.888, -1.503, -0.919, -0.214, 0.506, 1.158, 1.623, 1.913, 1.983, 1.824,
    1.456, 0.92, 0.275, -0.389, -1.011, -1.563, -1.92, -2.018, -1.849, -1.435,
    -0.829, -0.114, 0.602, 1.238, 1.679
]

messung_3 = [
    1.963, -1.992, 1.802, -1.825, 1.502, -1.518, 1.079, -1.089, 0.588, -0.595,
    -0.068, 0.195, -0.434, 0.973, -1.111, 1.548, -1.596, 1.824, -1.869, 1.965,
    -2.002, 1.967, -1.999, 1.835, -1.859, 1.553, -1.571, 1.165, -1.159, 0.667,
    -0.674, 0.017, 0.116, -0.831, 1.328, -1.451, 1.728, -1.774, 1.932, -1.971,
    1.983, -2.015, 1.878, -1.907, 1.632, -1.651, 1.255, -1.267, 0.773, -0.784,
    0.156, -0.063, -0.579, 0.753, -0.936, 1.398, -1.518, 1.782, -1.826, 1.951,
    -1.989, 1.98, -2.012, 1.861, -1.89, 1.626, -1.649, 1.249, -1.262, 0.767,
    -0.775, 0.146, -0.054, -0.589, 0.75, -0.897, 1.407, -1.526, 1.786, -1.83,
    1.953, -1.993, 1.976, -2.007, 1.858, -1.881, 1.6, -1.619, 1.248, -1.261,
    0.766, -0.774, 0.145, -0.052, -0.607, 0.767, -0.91, 1.377, -1.495, 1.767,
    -1.812, 1.945, -1.987, 1.979, -2.011
]

# Abtastrate festlegen
fs = 953.5

def calculate_psd(data_list, sample_rate):
    data_arr = np.array(data_list)
    N = len(data_arr)
    window = np.hanning(N)
    windowed = data_arr * window
    
    fft_vals = np.fft.rfft(windowed)
    freqs = np.fft.rfftfreq(N, d=1/sample_rate)
    
    psd_vals = (np.abs(fft_vals) ** 2) / (sample_rate * np.sum(window ** 2))
    psd_vals[1:-1] *= 2
    
    return freqs[1:], psd_vals[1:]

freqs1, psd1 = calculate_psd(messung_1, fs)
freqs2, psd2 = calculate_psd(messung_2, fs)
freqs3, psd3 = calculate_psd(messung_3, fs)

# Plot für alle 3 Messungen
plt.figure(figsize=(10, 5))
plt.loglog(freqs1, psd1, label="Messung 1 (Spalte 1, N=105)", color="crimson", linewidth=1.5)
plt.loglog(freqs2, psd2, label="Messung 2 (Spalte 2, N=105)", color="navy", linewidth=1.5)
plt.loglog(freqs3, psd3, label="Messung 3 (Spalte 3, N=105)", color="teal", linewidth=1.5)

plt.title("PSD Vergleich der 3 verschiedenen Messungen (N = 105)")
plt.xlabel("Frequenz [Hz] (log-skaliert)")
plt.ylabel("PSD [V²/Hz] (log-skaliert)")
plt.grid(True, which="both", linestyle="--", alpha=0.6)
plt.legend()
plt.tight_layout()
plt.show()
