SmichaelSmolley/Diplom_Arbeit/Software/firmware/PCB_test_com_code/test_data.h

#ifndef TEST_DATA_H
#define TEST_DATA_H

double messwerte[1000] = {
    2.73322921,
    0.00318755,
    0.00318755,
    0.00318755,
    0.00356255,
    0.00356255,
    0.00356255,
    0.00393756,
    0.00393756,
    0.00393756,
    0.00393756,
    0.00356255,
    0.00356255,
    0.00356255,
    0.00393756,
    0.00393756,
    0.00393756,
    0.00393756,
    0.00393756,
    0.00393756,
    0.00393756,
    0.00356255,
    0.00356255,
    0.00393756,
    0.00393756,
    0.00431257,
    0.00431257,
    0.00431257,
    0.00431257,
    0.00431257,
    0.00393756,
    0.00356255,
    0.00393756,
    0.00431257,
    0.00431257,
    0.00431257,
    0.00431257,
    0.00356255,
    0.00393756,
    0.00393756,
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
};

#endif
